nionio6915/Euclid_Probe/Firmware_Examples/Duet_RRF2.x/probe_deploy.png

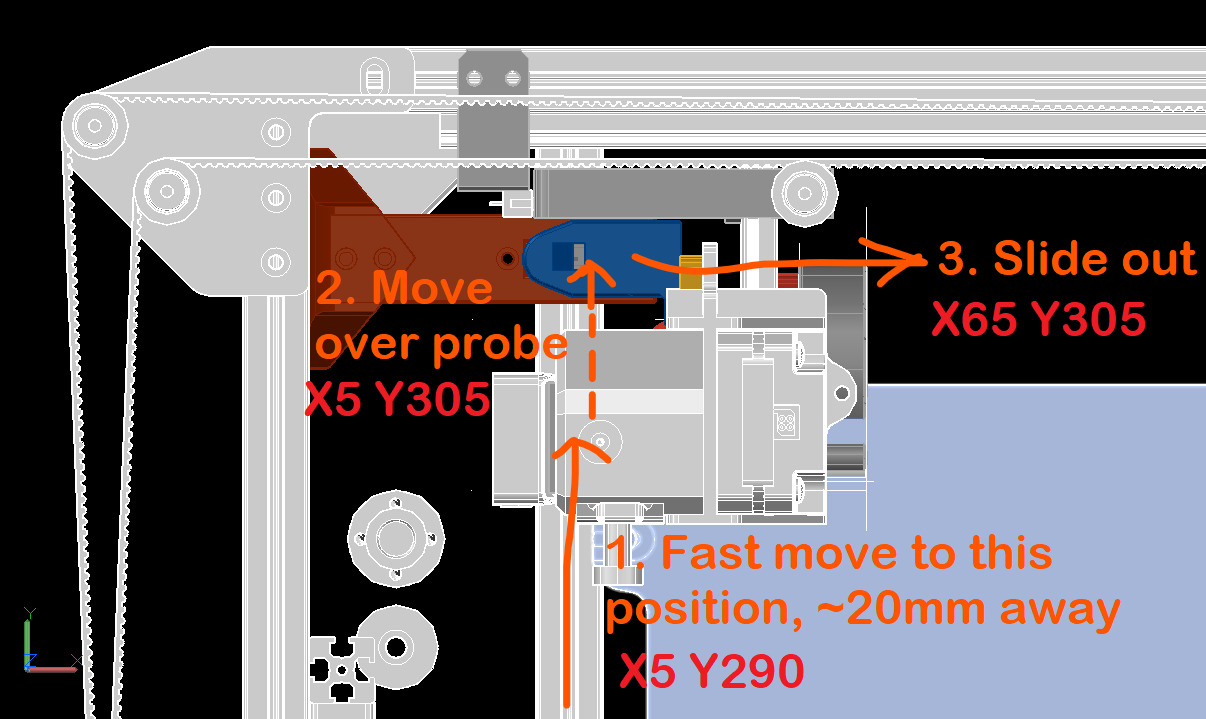
Firmware_Examples/Duet_RRF2.x/probe_deploy.png
