nionio6915/Euclid_Probe/Firmware_Examples/Klipper/user_contrib/FlashForgeCreator_Qidi/QIDI_BED.png

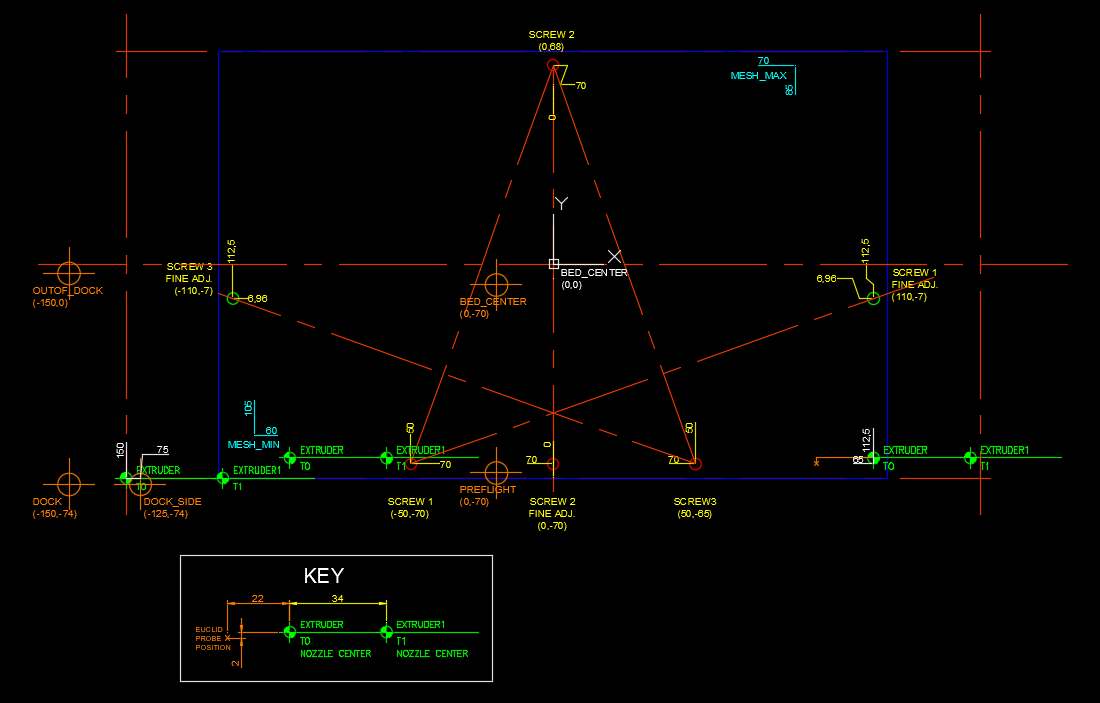
Firmware_Examples/Klipper/user_contrib/FlashForgeCreator_Qidi/QIDI_BED.png
