nionio6915/Euclid_Probe/Firmware_Examples/Klipper/user_contrib/V_Core/vcore3.png

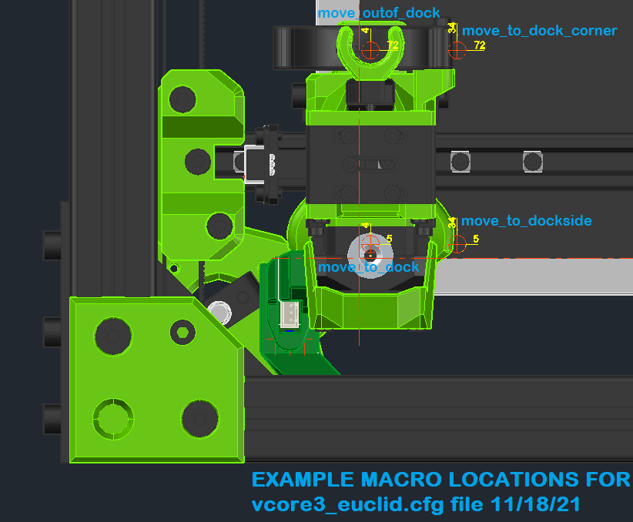
Firmware_Examples/Klipper/user_contrib/V_Core/vcore3.png
