nionio6915/Euclid_Probe/images/EnderMount.png

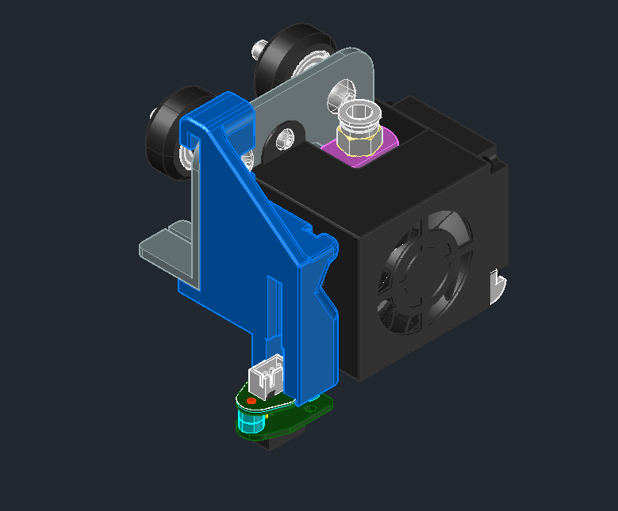
images/EnderMount.png
