nionio6915/Euclid_Probe/images/Front-Probe.png

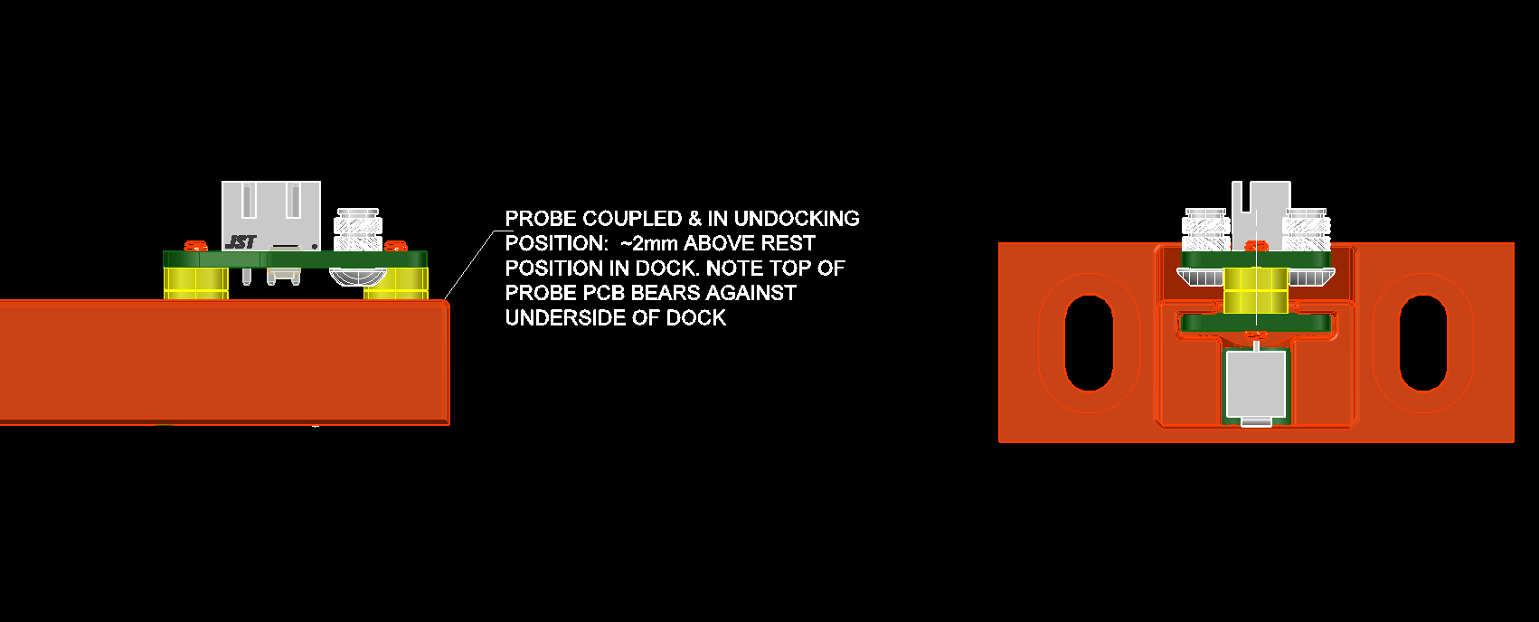
images/Front-Probe.png
