nionio6915/Euclid_Probe/images/Grafting_Mount1.png

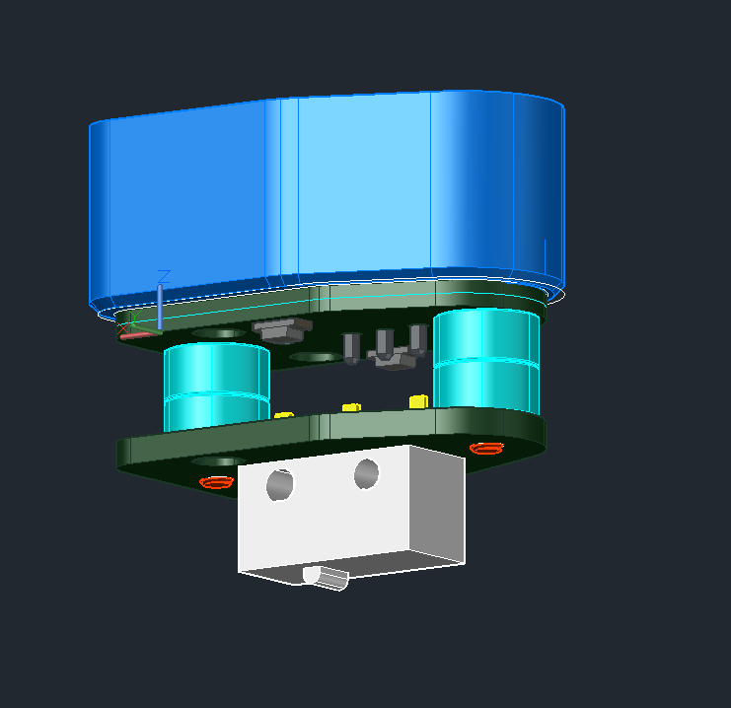
images/Grafting_Mount1.png
