nionio6915/Euclid_Probe/images/Grafting_Mount2.png

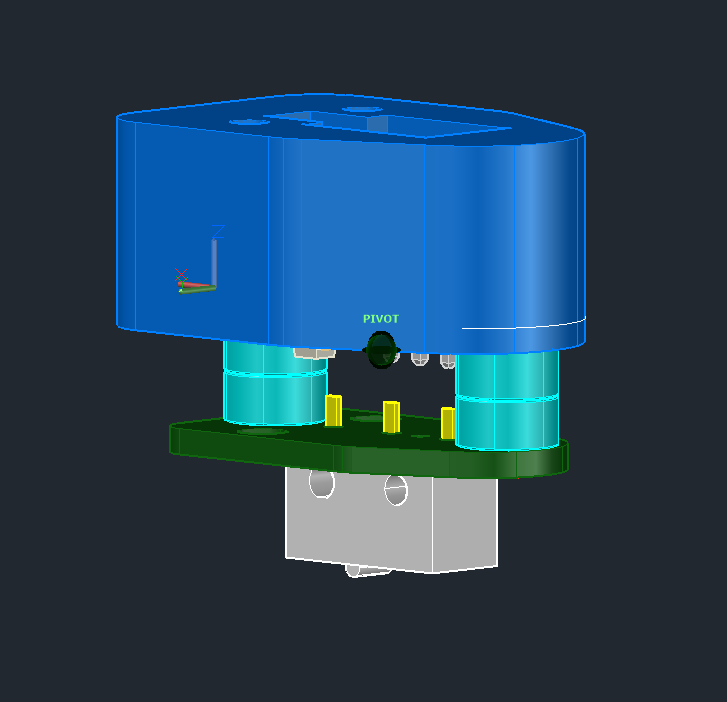
images/Grafting_Mount2.png
