nionio6915/Euclid_Probe/images/IMG_20210708_134827082.jpg

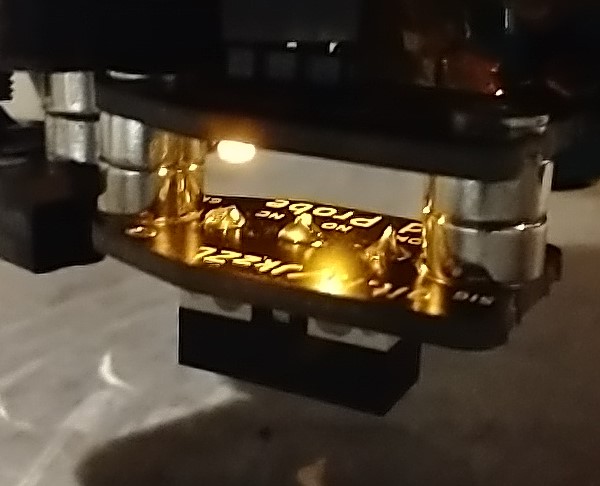
images/IMG_20210708_134827082.jpg
