nionio6915/Euclid_Probe/images/ISO_View1.png

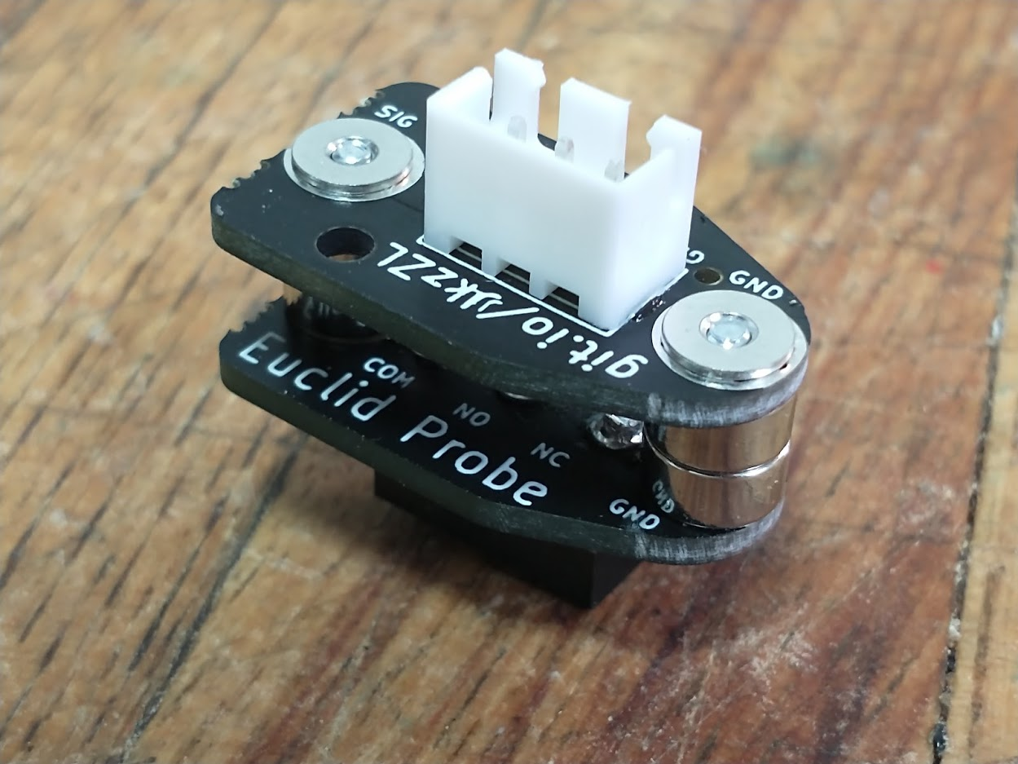
images/ISO_View1.png
