nionio6915/Euclid_Probe/images/ISO_View3.png

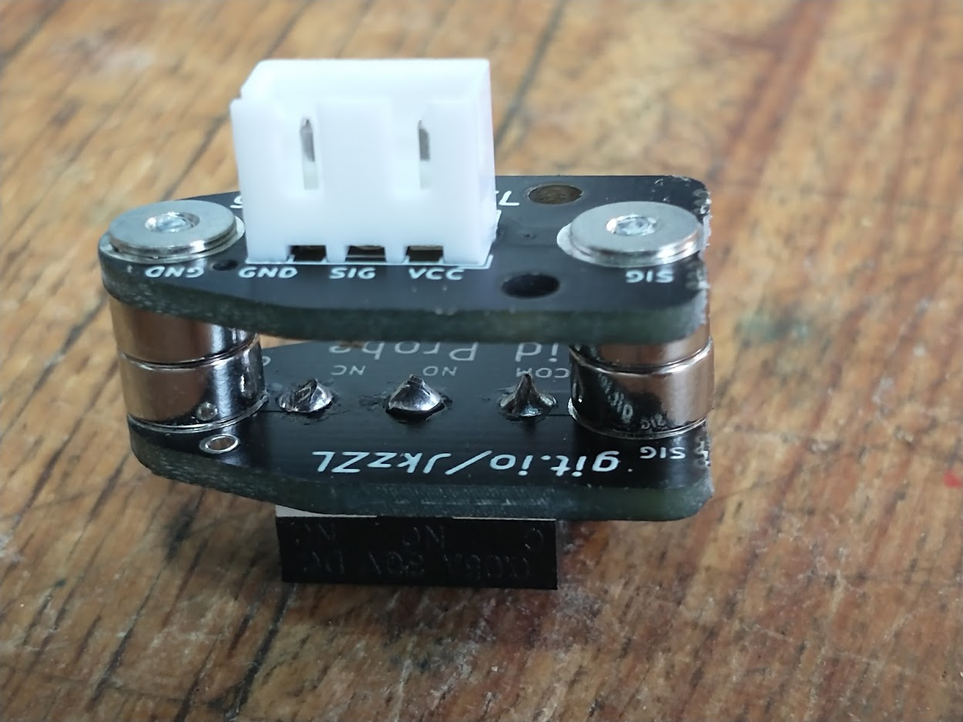
images/ISO_View3.png
