nionio6915/Euclid_Probe/images/ISO_View.png

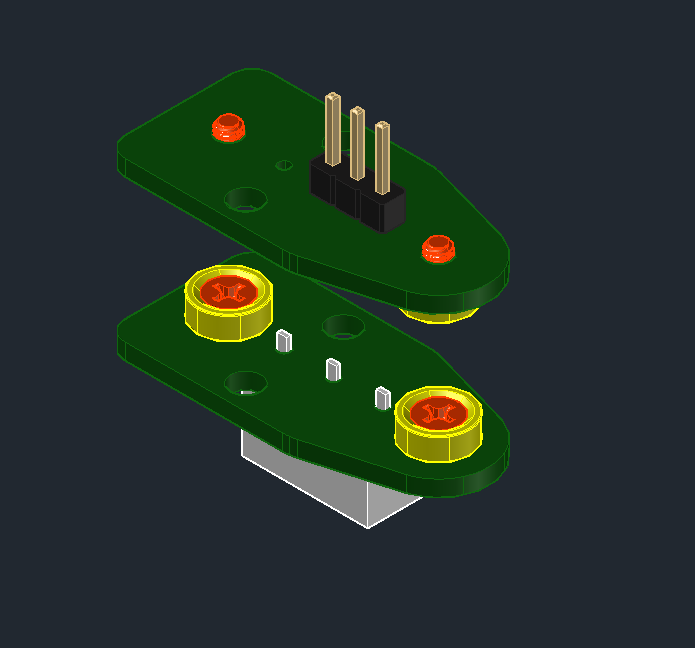
images/ISO_View.png
