nionio6915/Euclid_Probe/images/isobtm2.png

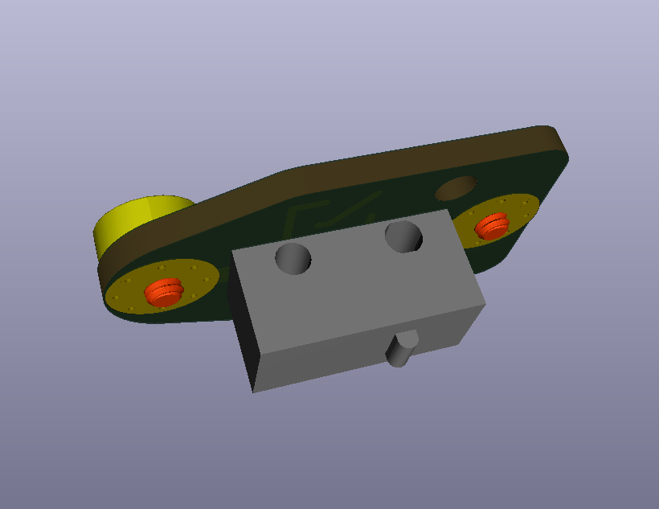
images/isobtm2.png
