nionio6915/Euclid_Probe/images/isobtm.png

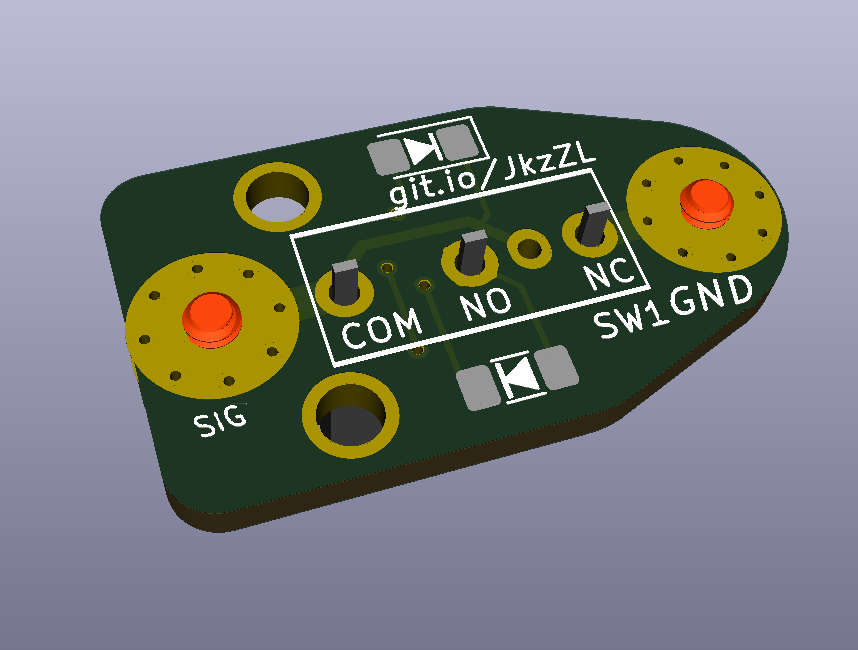
images/isobtm.png
