nionio6915/Euclid_Probe/images/isotop2.png

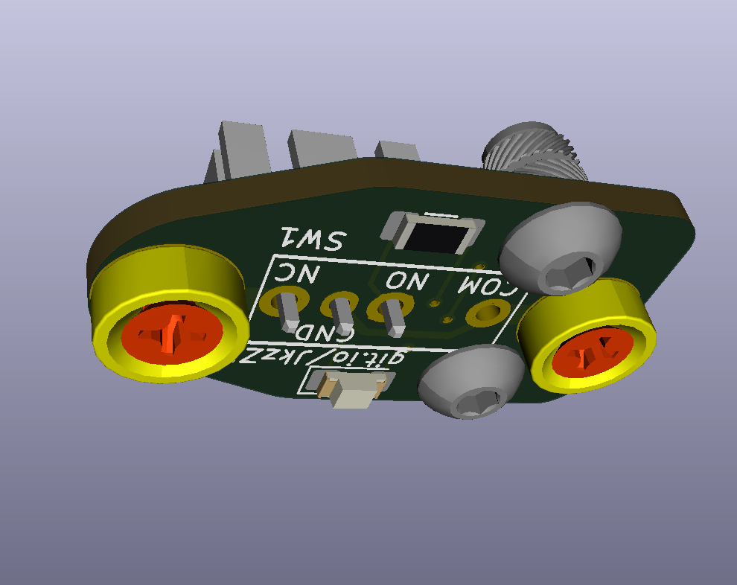
images/isotop2.png
