nionio6915/Euclid_Probe/images/isotop.png

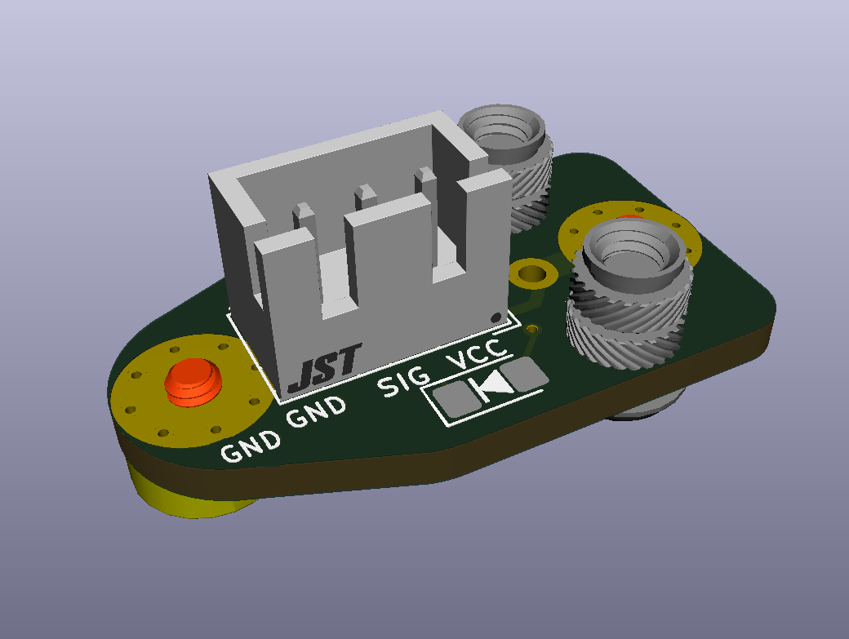
images/isotop.png
