nionio6915/Euclid_Probe/images/Left_View.png

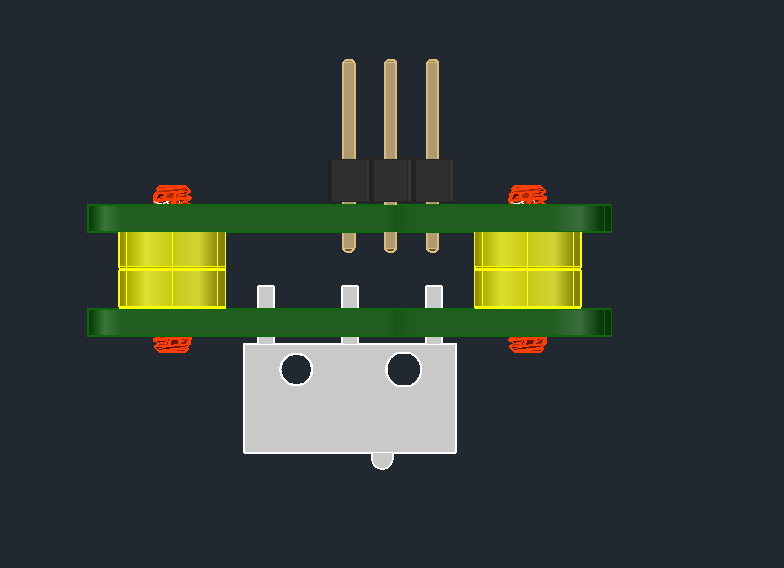
images/Left_View.png
