nionio6915/Euclid_Probe/images/mag-polarity.png

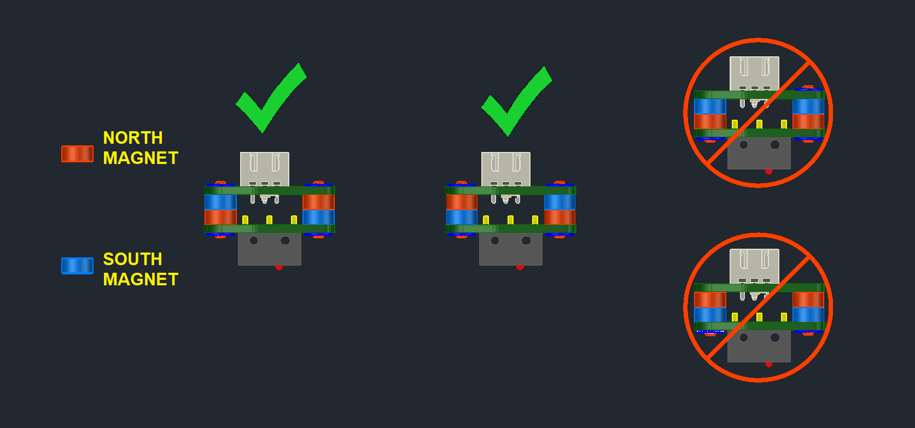
images/mag-polarity.png
