nionio6915/Euclid_Probe/images/PROBE-BOARD.png

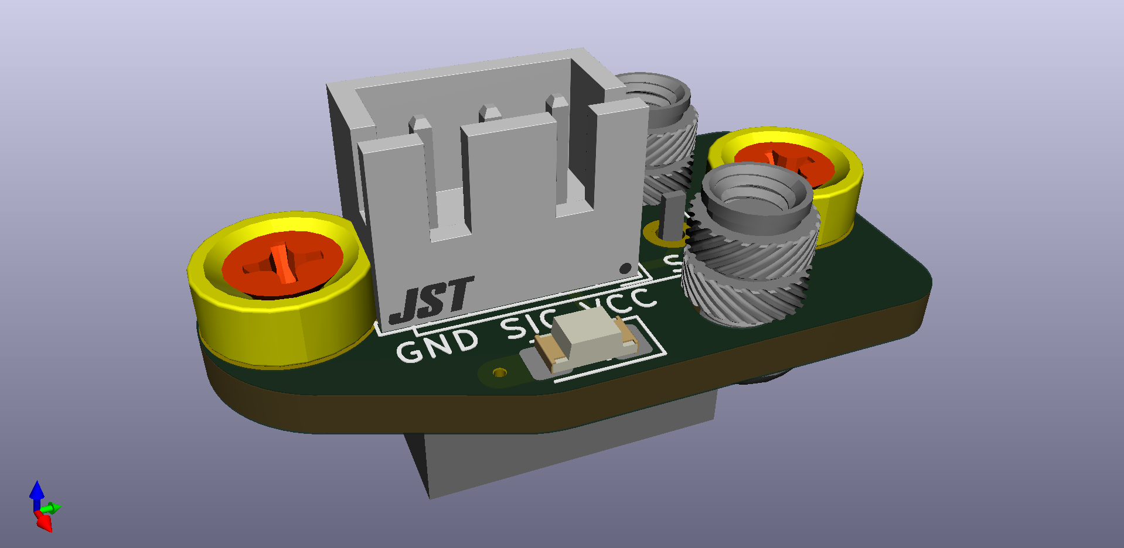
images/PROBE-BOARD.png
