nionio6915/Euclid_Probe/images/probe-offsets.png

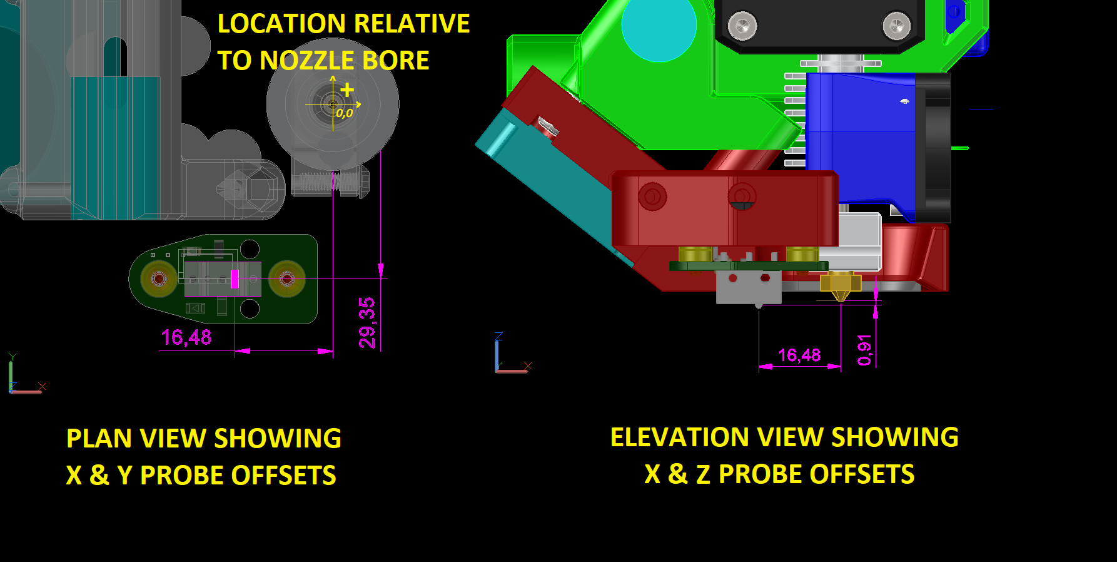
images/probe-offsets.png
