nionio6915/Euclid_Probe/images/Probe_Dock_Fixed.png

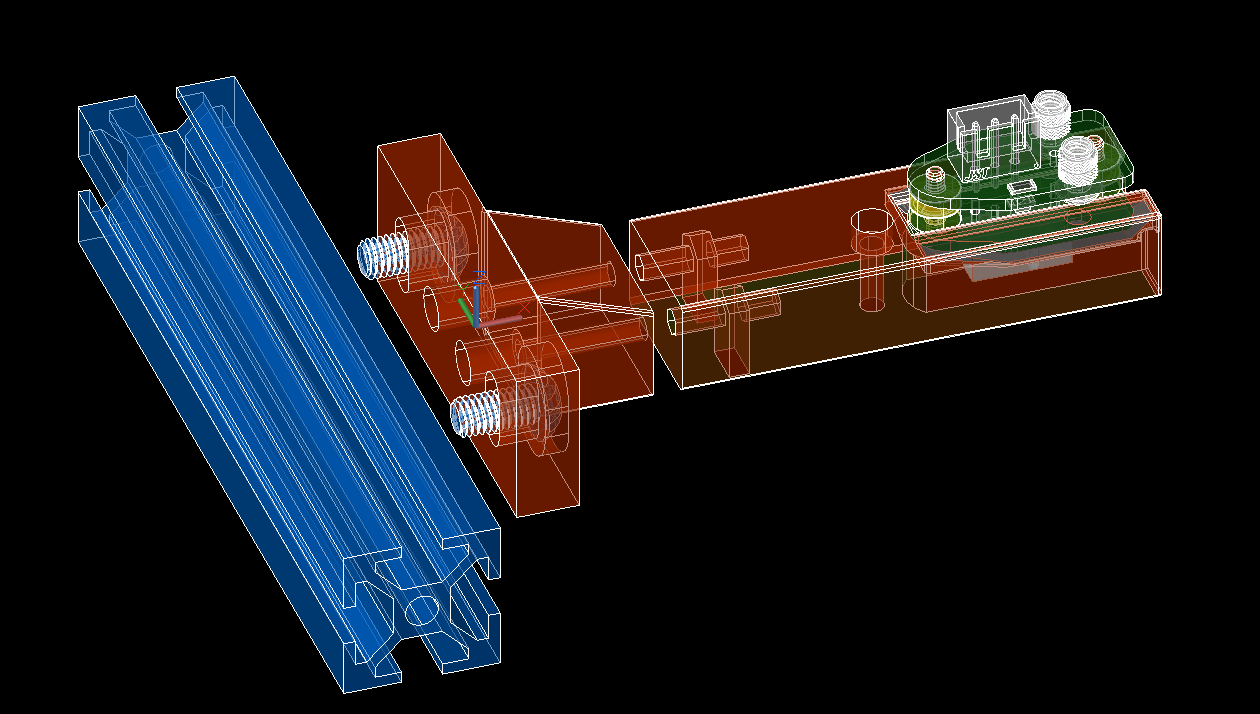
images/Probe_Dock_Fixed.png
