nionio6915/Euclid_Probe/images/RailCore_Native.png

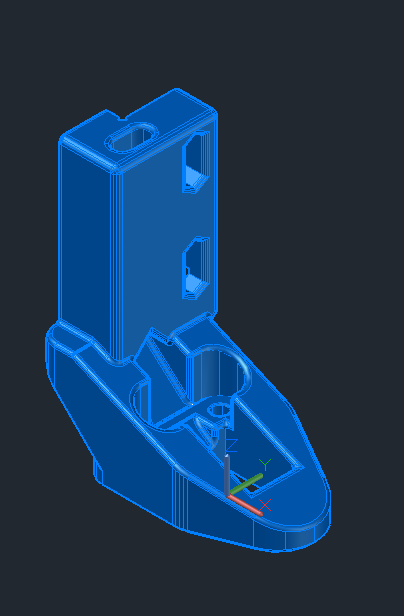
images/RailCore_Native.png
