nionio6915/Euclid_Probe/images/VoronStill3-TN.png

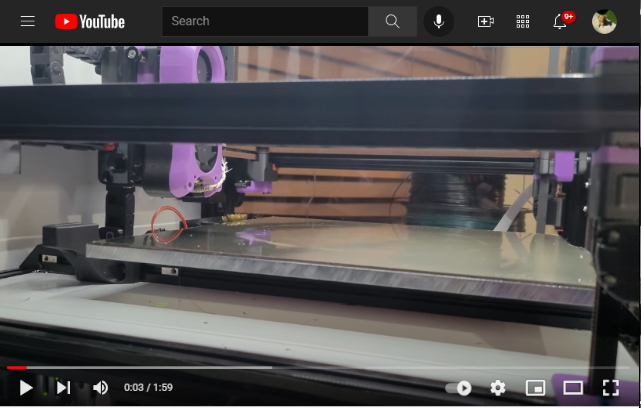
images/VoronStill3-TN.png
