nionio6915/Euclid_Probe/stls/Ender3/EnderDock.jpg

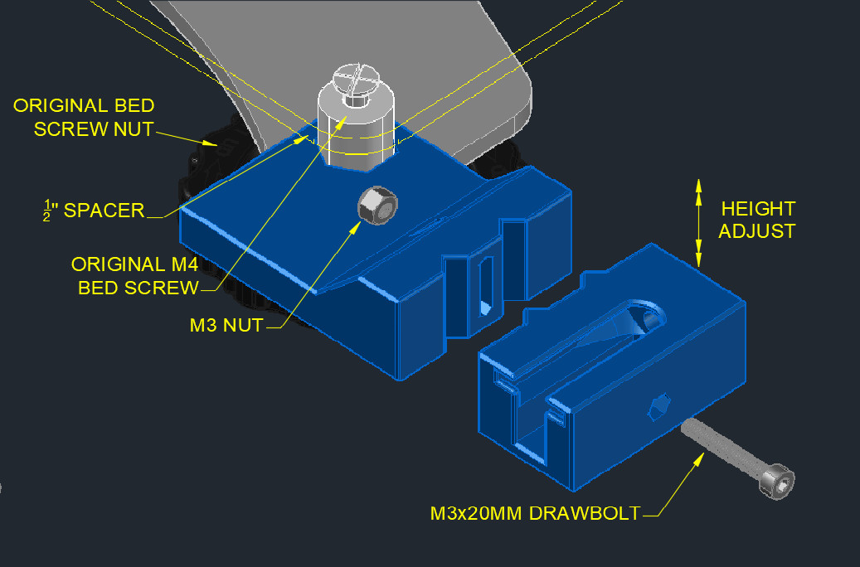
stls/Ender3/EnderDock.jpg
