nionio6915/Euclid_Probe/stls/Ender3/EnderProbeOffsets.jpg

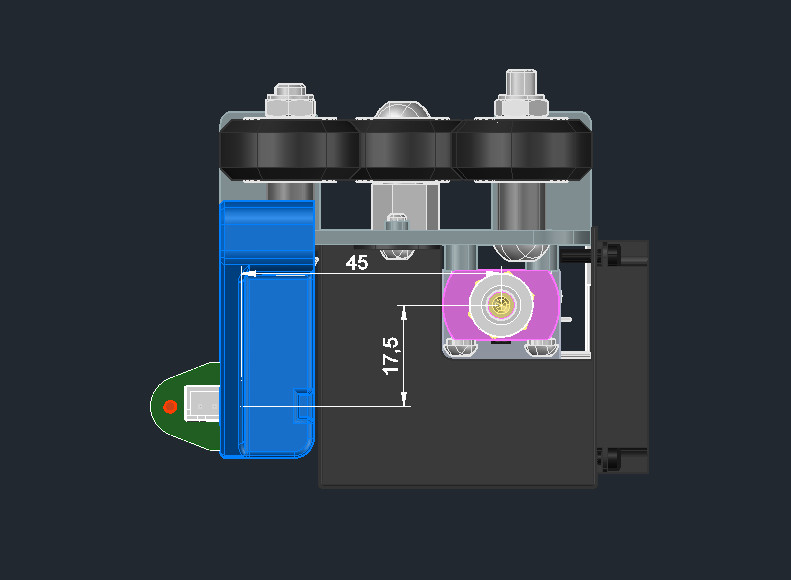
stls/Ender3/EnderProbeOffsets.jpg
