nionio6915/Euclid_Probe/stls/FlashForgeCreator-Qidi/Qidi1.jpg

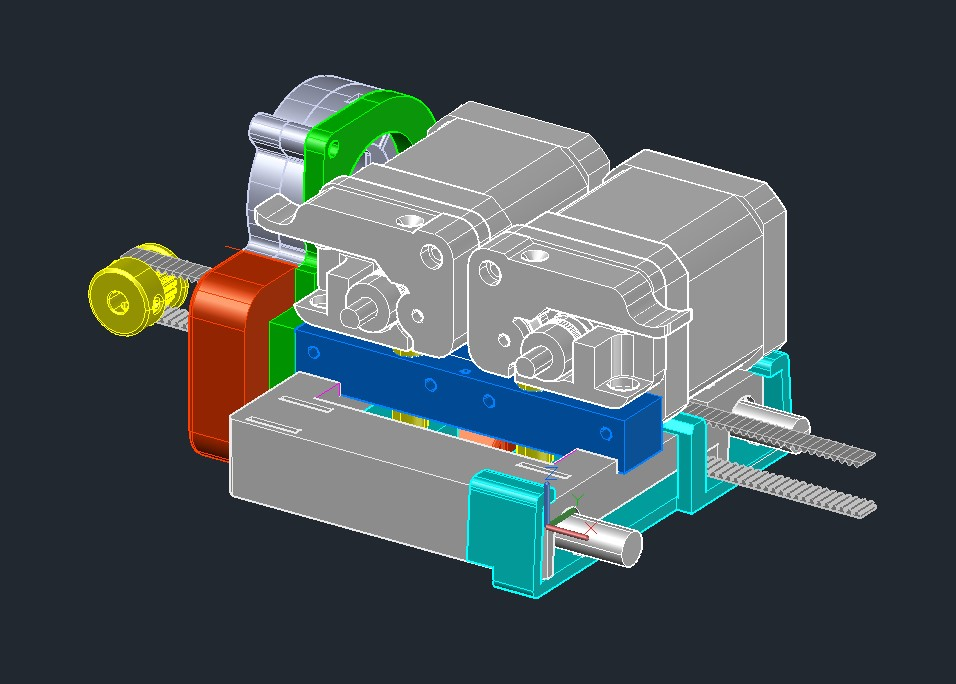
stls/FlashForgeCreator-Qidi/Qidi1.jpg
