nionio6915/Euclid_Probe/stls/FlashForgeCreator-Qidi/Qidi2.jpg

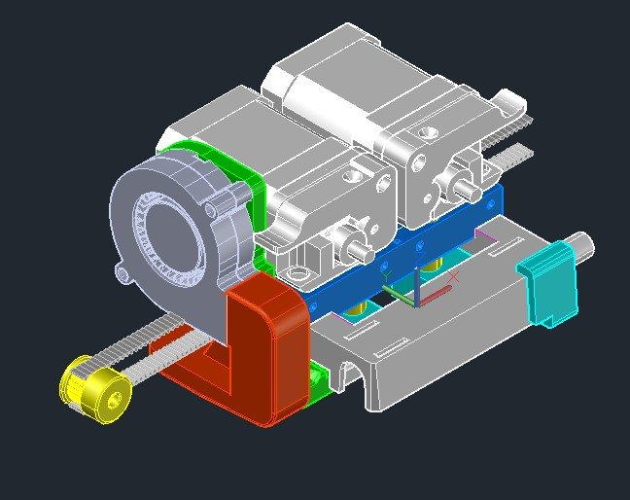
stls/FlashForgeCreator-Qidi/Qidi2.jpg
