nionio6915/Euclid_Probe/stls/FlashForgeCreator-Qidi/Qidi3.jpg

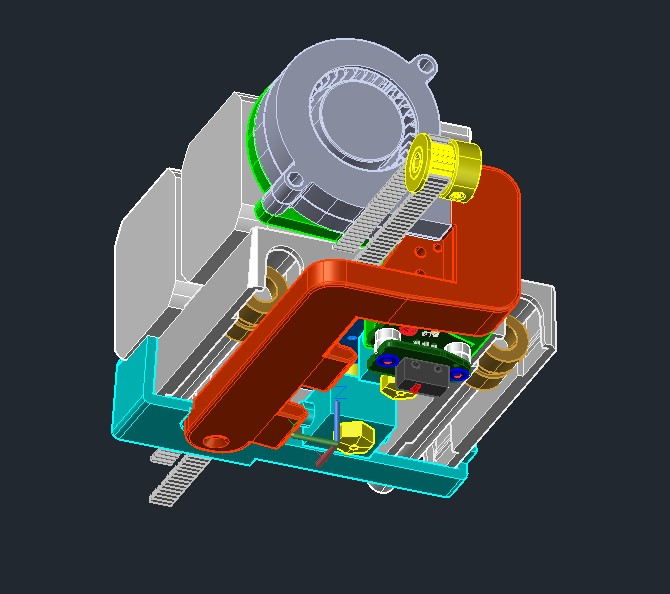
stls/FlashForgeCreator-Qidi/Qidi3.jpg
