nionio6915/Euclid_Probe/stls/Mount Adapters/12mm-186x300.jpg

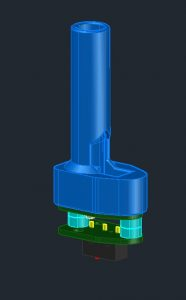
stls/Mount Adapters/12mm-186x300.jpg
