nionio6915/Euclid_Probe/stls/Mount Adapters/BLTouch/BLT.jpg

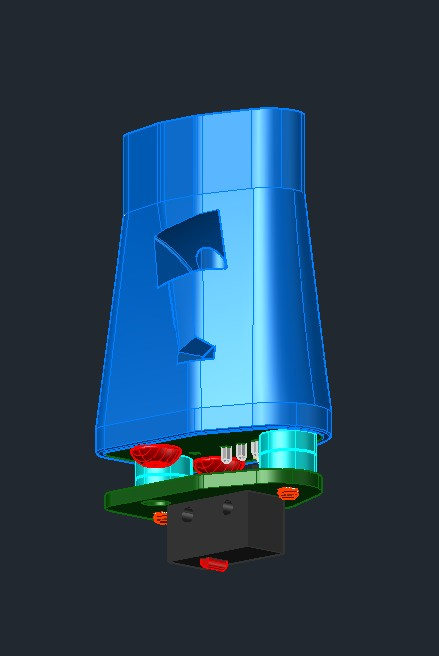
stls/Mount Adapters/BLTouch/BLT.jpg
