nionio6915/Euclid_Probe/stls/Mount Adapters/BLTouch/Screenshot 2022-03-06 101952.jpg

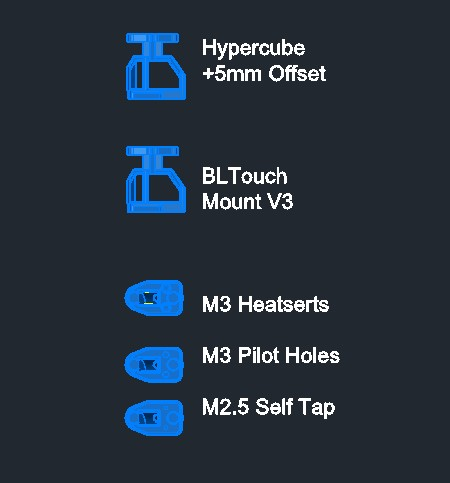
stls/Mount Adapters/BLTouch/Screenshot 2022-03-06 101952.jpg
