nionio6915/Euclid_Probe/stls/Rail Core/DrillJig1.png

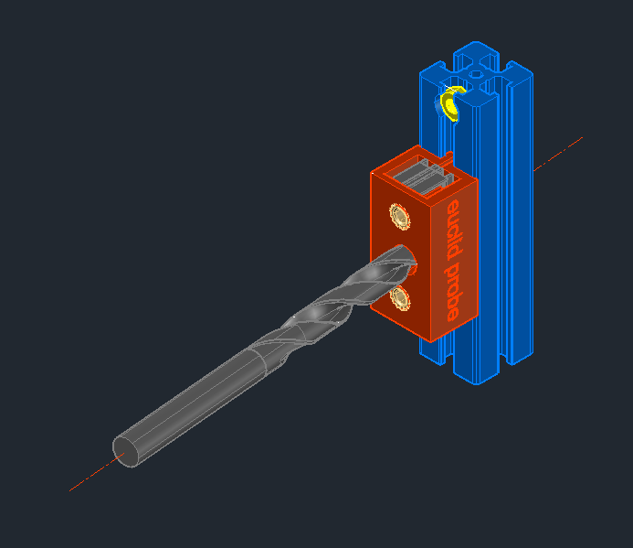
stls/Rail Core/DrillJig1.png
