nionio6915/Euclid_Probe/stls/Rail Core/DrillJig2.png

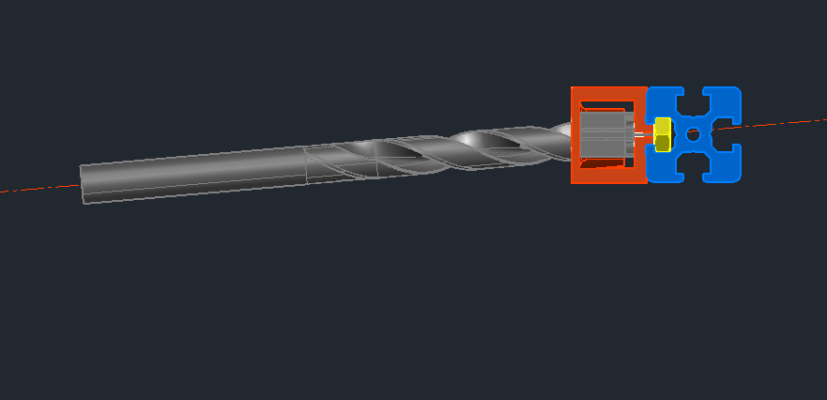
stls/Rail Core/DrillJig2.png
