nionio6915/Euclid_Probe/stls/V-Core/EVA_Mount/EVA2.x_MountV5.jpg

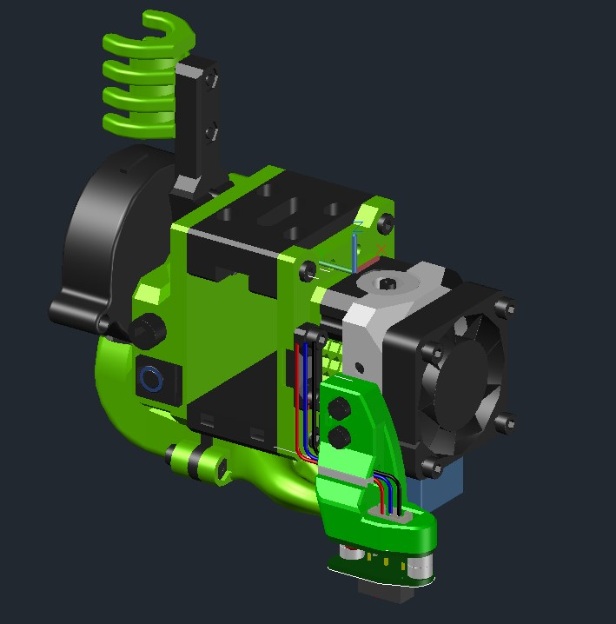
stls/V-Core/EVA_Mount/EVA2.x_MountV5.jpg
