nionio6915/Euclid_Probe/stls/V-Core/EVA_Mount/EVA3.x_Mount.webp

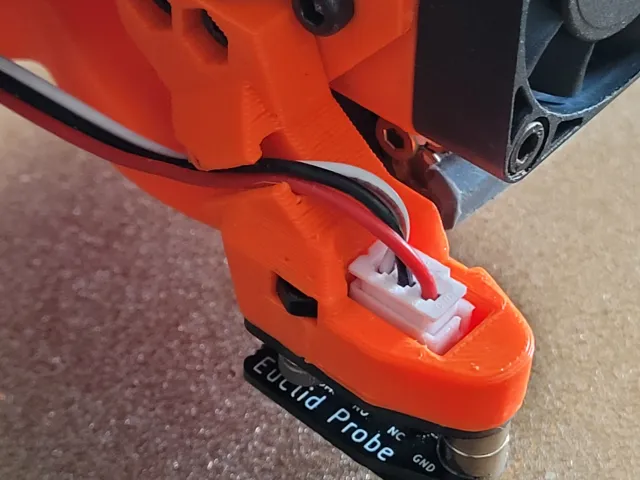
stls/V-Core/EVA_Mount/EVA3.x_Mount.webp
