nionio6915/Euclid_Probe/stls/V-Core/EVA_Mount/Screenshot 2021-12-29 203222.png

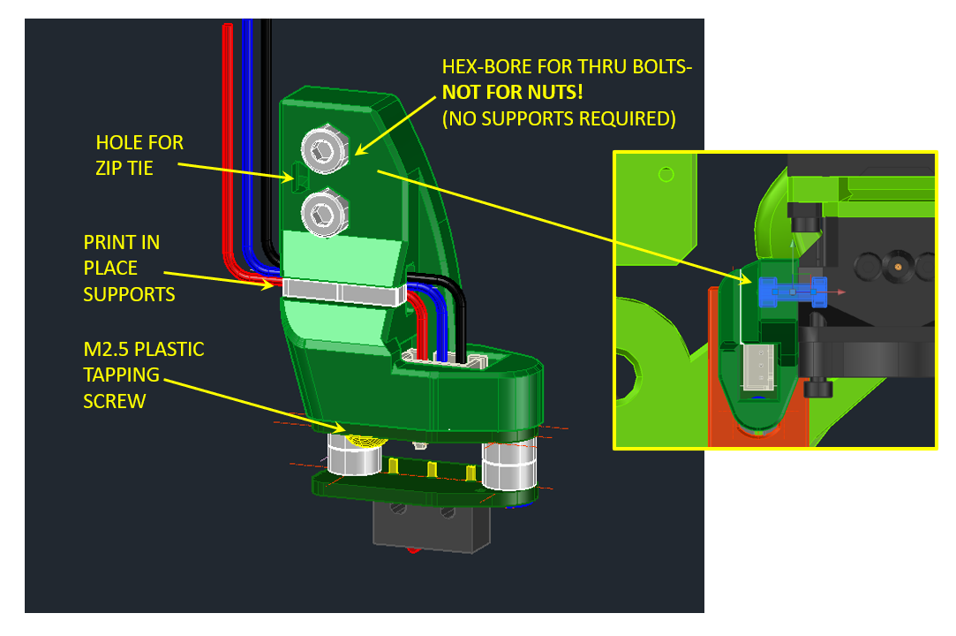
stls/V-Core/EVA_Mount/Screenshot 2021-12-29 203222.png
