nionio6915/Euclid_Probe/stls/V-Core/V-Core3/Euclid_Probe_Screen2.jpg

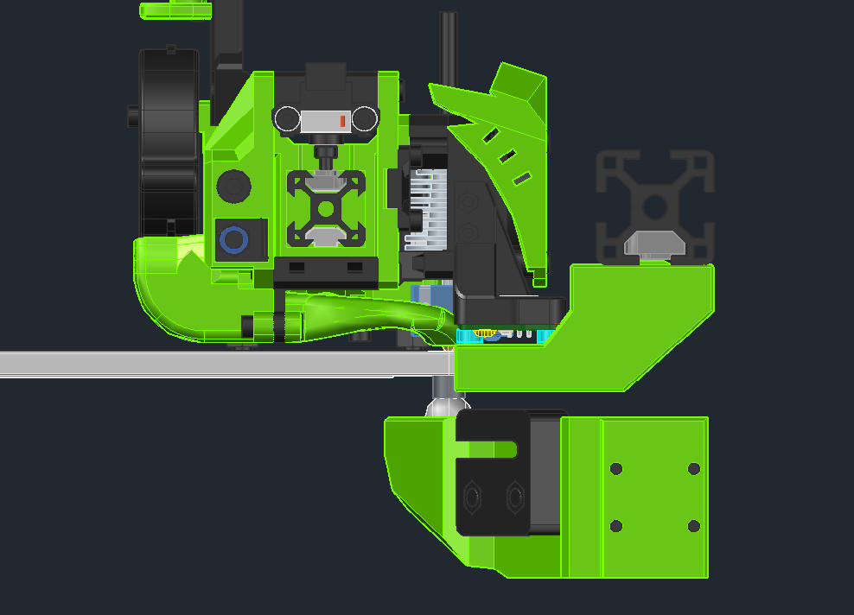
stls/V-Core/V-Core3/Euclid_Probe_Screen2.jpg
