nionio6915/Euclid_Probe/stls/V-Core/V-Core3/unknown-768x550.jpg

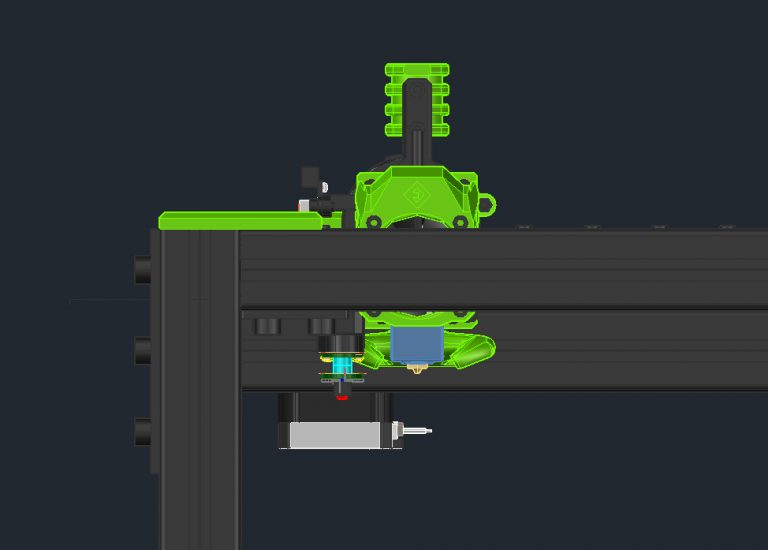
stls/V-Core/V-Core3/unknown-768x550.jpg
