nionio6915/Euclid_Probe/stls/Voron/User_Contrib/Dust_Gantry_Dock2.jpg

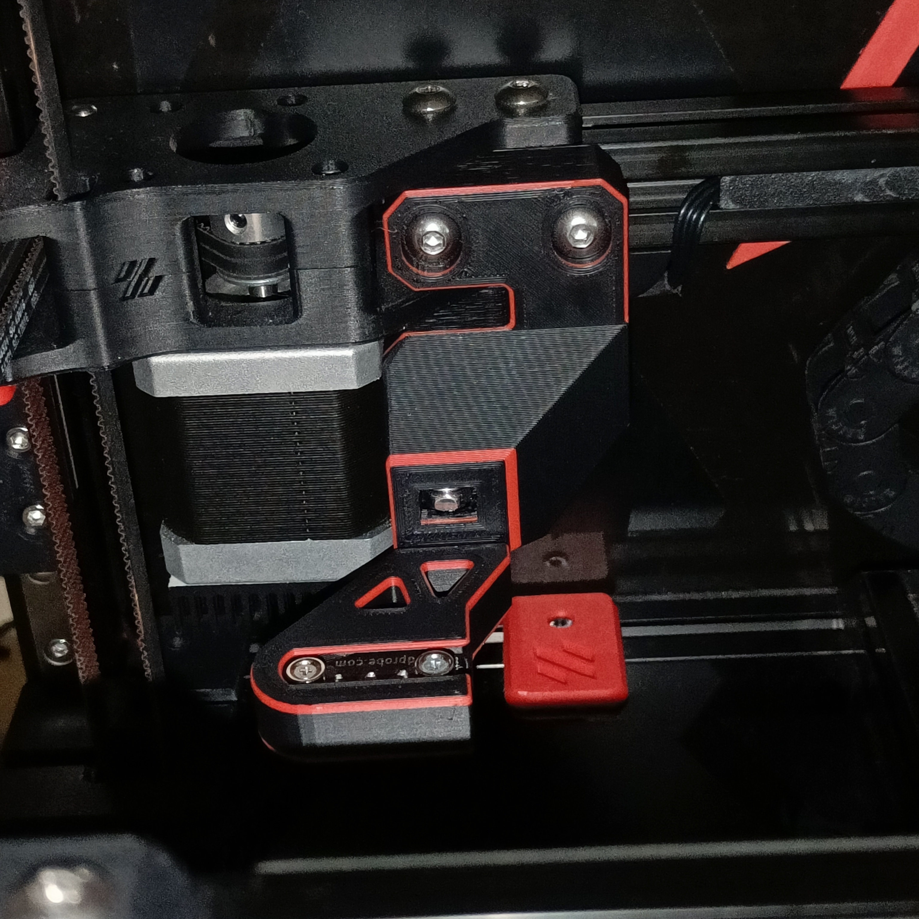
stls/Voron/User_Contrib/Dust_Gantry_Dock2.jpg
