nionio6915/Euclid_Probe/stls/Fan Mounts/5015_LeftP1.5V4.stl

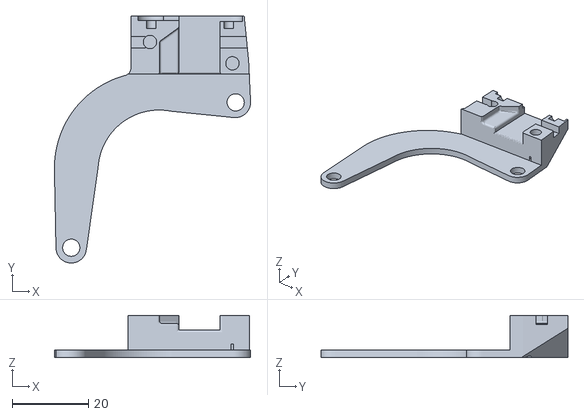
[picture p93: CAD file, 2021-12-24]
stls/Fan Mounts/5015_LeftP1.5V4.stl
51.3 x 64.6 x 11.0
