nionio6915/Euclid_Probe/stls/FlashForgeCreator-Qidi/FanMount.stl

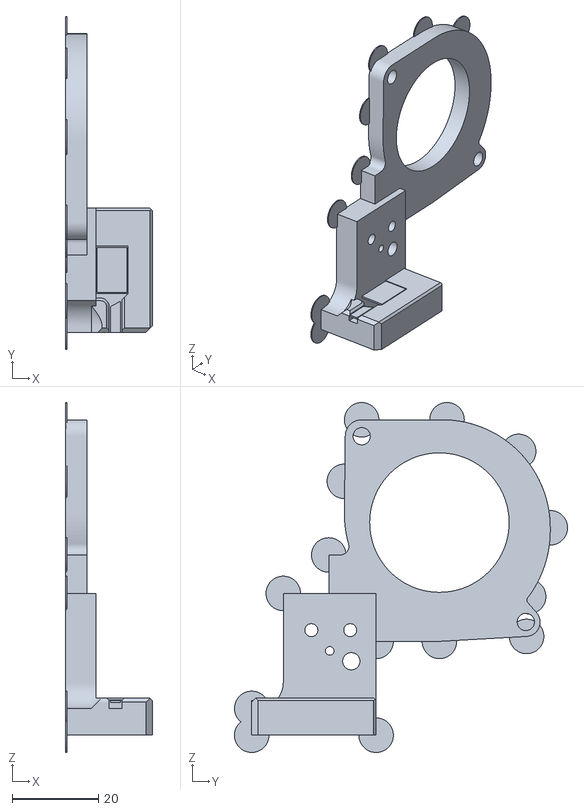
[picture p94: CAD file, 2023-03-29]
stls/FlashForgeCreator-Qidi/FanMount.stl
20.1 x 77.1 x 81.0
