nionio6915/Euclid_Probe/stls/Mount Adapters/18mmInductive.stl

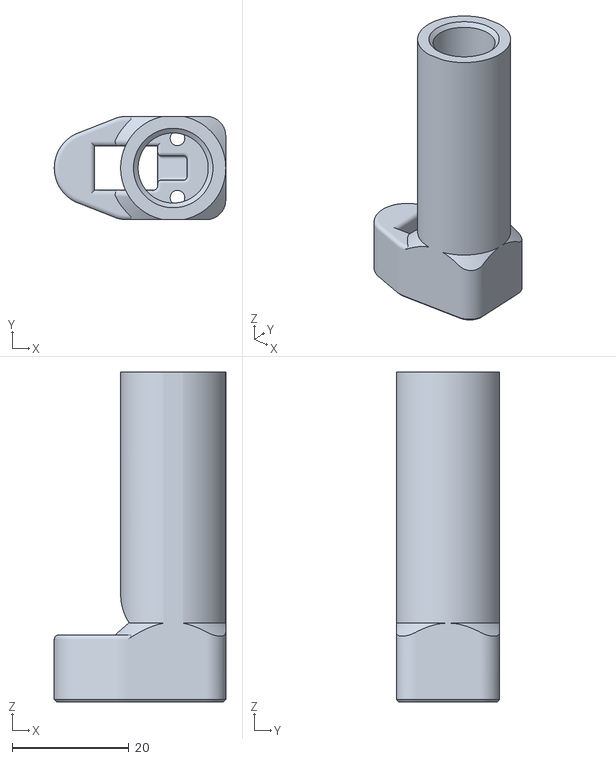
[picture p95: CAD file, 2021-08-17]
stls/Mount Adapters/18mmInductive.stl
29.4 x 17.7 x 56.5
