nionio6915/Euclid_Probe/stls/Mount Adapters/2020_End_Mount/2020_Rail_Vert.stl

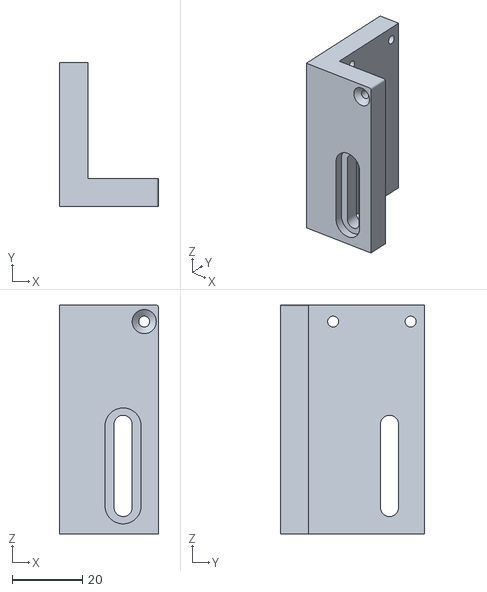
[picture p96: CAD file, 2021-06-21]
stls/Mount Adapters/2020_End_Mount/2020_Rail_Vert.stl
28.0 x 41.0 x 65.0
