nionio6915/Euclid_Probe/stls/Mount Adapters/Omron/OmronFotekV4.3mf

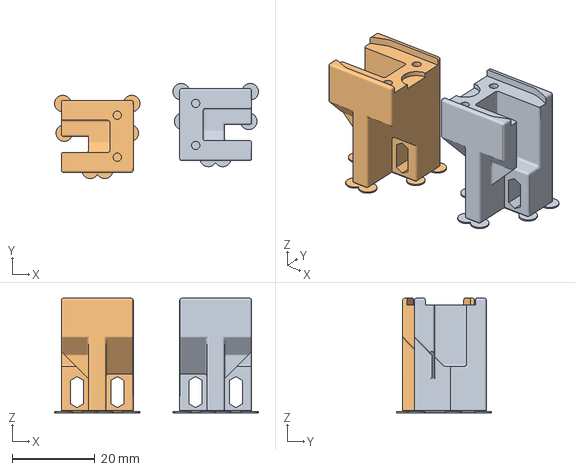
[picture p97: CAD file, 2023-02-20]
stls/Mount Adapters/Omron/OmronFotekV4.3mf
49.3 x 23.0 x 27.7 mm
OmronFotekV4.stl x 2
