nionio6915/Euclid_Probe/stls/probe-dock_fixed.stl

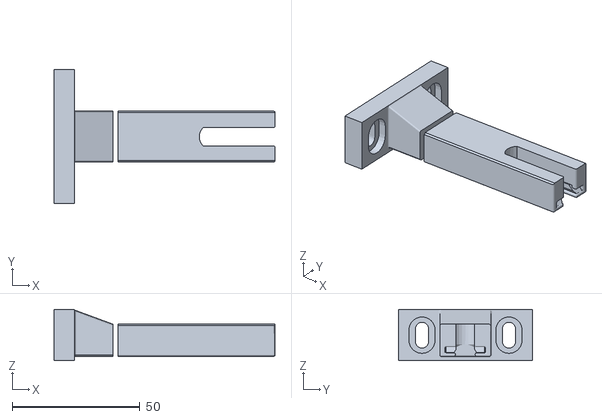
[picture p98: CAD file, 2021-06-24]
stls/probe-dock_fixed.stl
86.4 x 52.2 x 20.1
