nionio6915/Euclid_Probe/stls/Rail Core/RailcoreMount713NativeV5_M3Holes.3mf

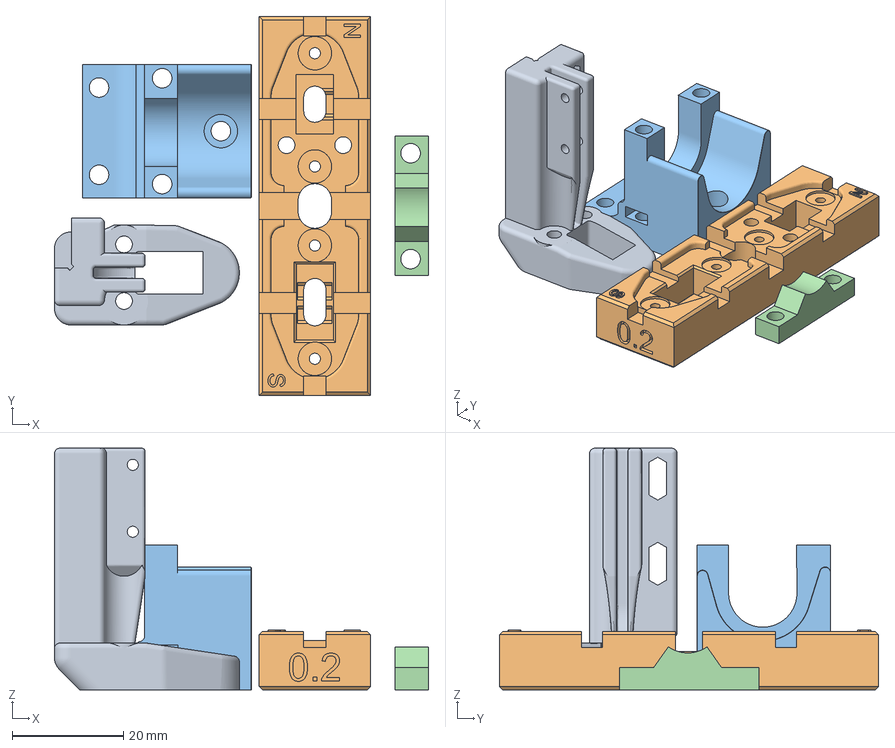
[picture p99: CAD file, 2023-11-06]
stls/Rail Core/RailcoreMount713NativeV5_M3Holes.3mf
67.1 x 68.0 x 43.4 mm
RailcoreMount713NativeV5_M3Holes.stl
soldering_jigV5-0.2mm_margin.stl
E3DV6_Mount.stl
E3DV6_clamp.stl
