nionio6915/Euclid_Probe/stls/UserContrib/akhamar_No Short Cover/euclid_noshort_cover.stl

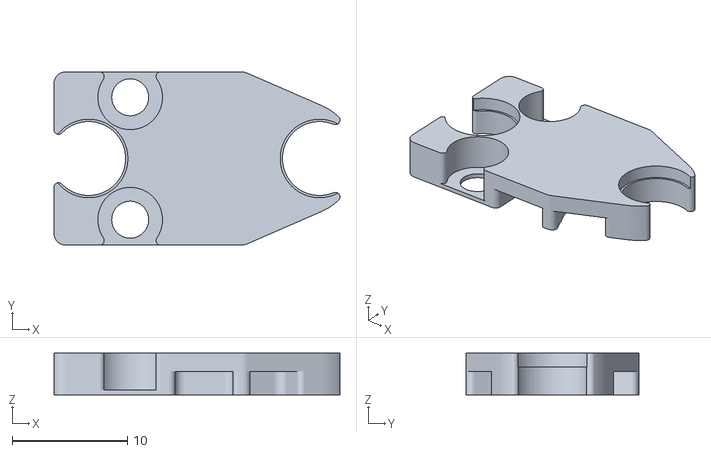
[picture p100: CAD file, 2022-07-11]
stls/UserContrib/akhamar_No Short Cover/euclid_noshort_cover.stl
24.8 x 15.0 x 3.60
