nionio6915/Euclid_Probe/stls/UserContrib/esc247_vzbot_vzprinthead/Euclid mount VZ-printhead v5.stl

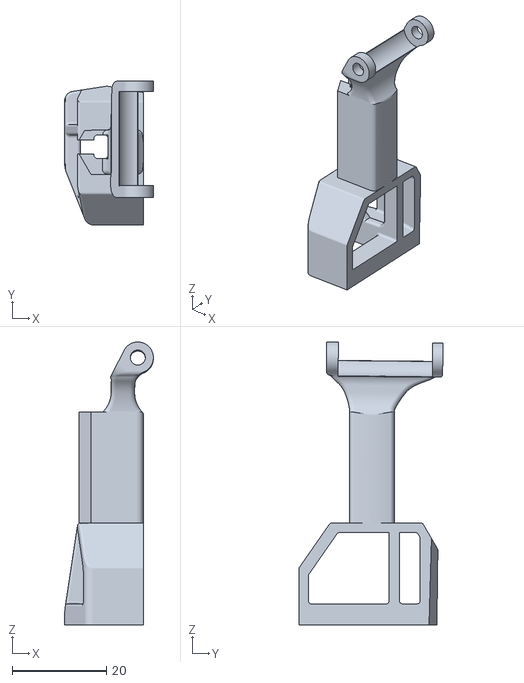
[picture p101: CAD file, 2023-08-14]
stls/UserContrib/esc247_vzbot_vzprinthead/Euclid mount VZ-printhead v5.stl
18.8 x 30.6 x 60.1
