nionio6915/Euclid_Probe/stls/UserContrib/v6cl_skinny_mount/euclid_slim.stl

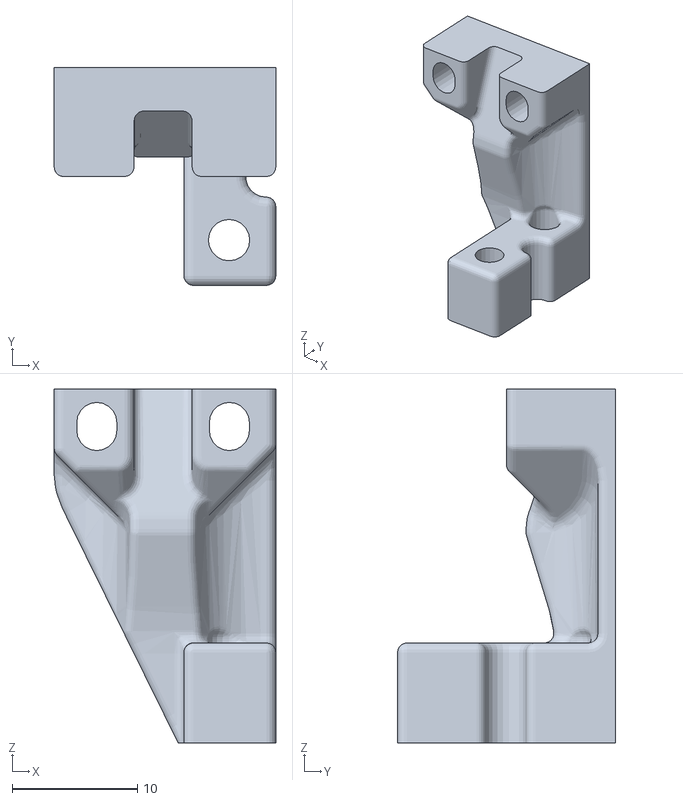
[picture p102: CAD file, 2022-07-11]
stls/UserContrib/v6cl_skinny_mount/euclid_slim.stl
17.7 x 17.4 x 28.3
