nionio6915/Euclid_Probe/stls/V-Core/EVA_Mount/EuclidDock_EVA3_0_v01.stl

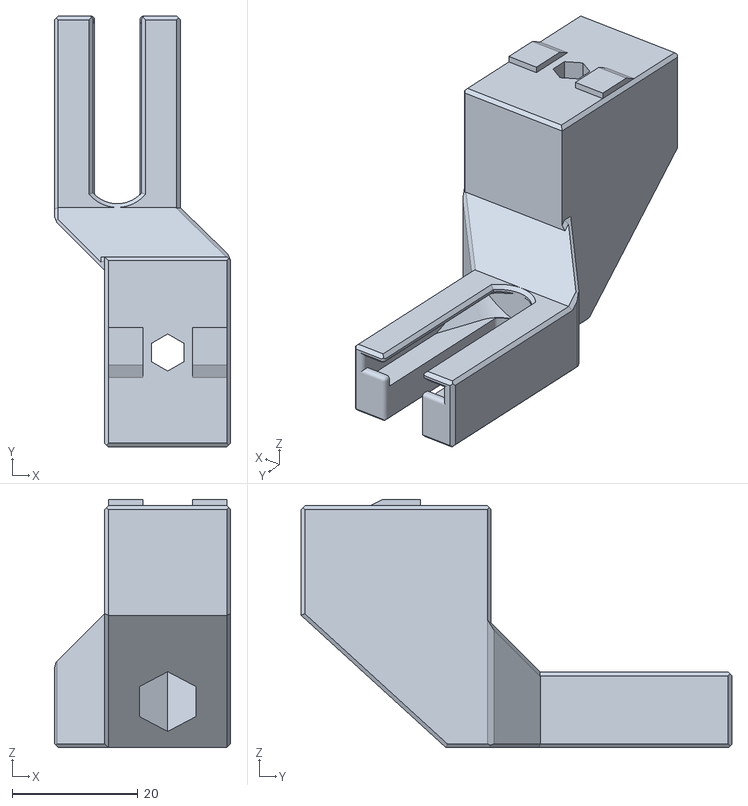
[picture p103: CAD file, 2022-06-29]
stls/V-Core/EVA_Mount/EuclidDock_EVA3_0_v01.stl
28.0 x 68.4 x 39.4
