nionio6915/Euclid_Probe/stls/V-Core/V-Core3/Euclid_EVA_DockV5_3030.stl

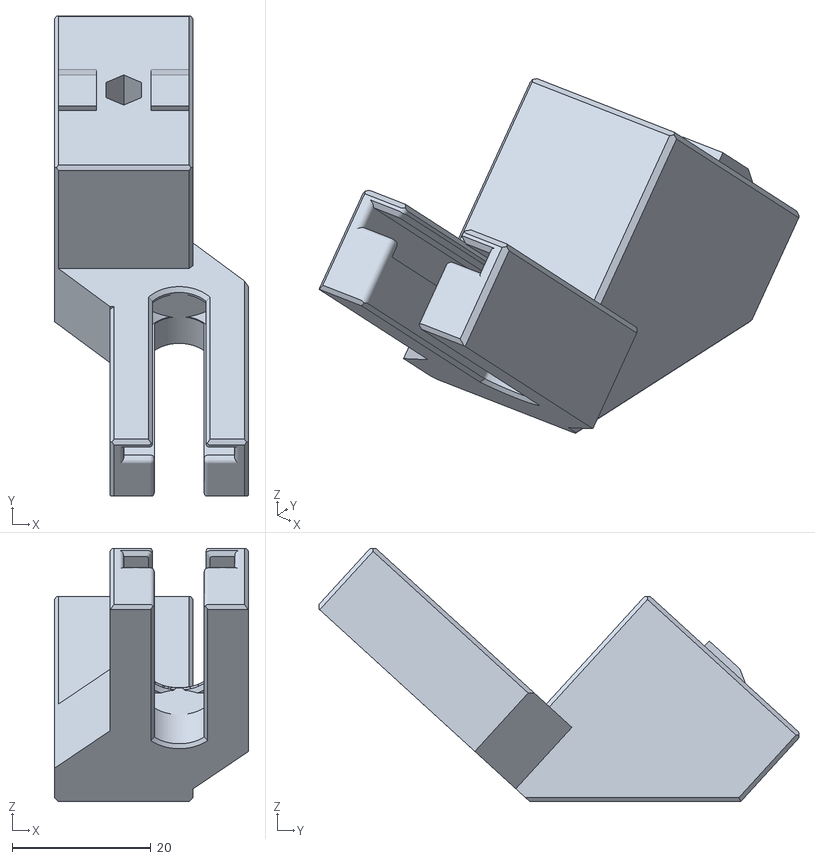
[picture p104: CAD file, 2021-12-25]
stls/V-Core/V-Core3/Euclid_EVA_DockV5_3030.stl
28.0 x 69.2 x 36.5
