nionio6915/Euclid_Probe/stls/Voron/Clockwork2_Euclid_MGN12X_RIGHT_Carriage_Ver2.stl

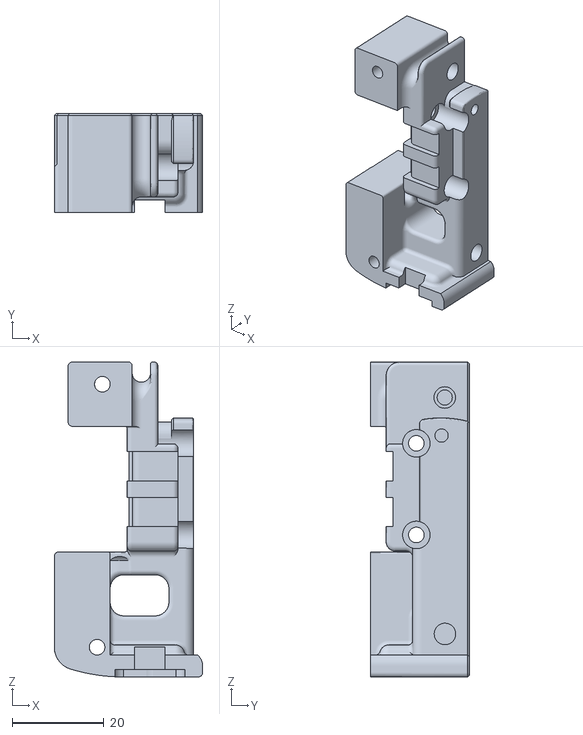
[picture p105: CAD file, 2022-10-25]
stls/Voron/Clockwork2_Euclid_MGN12X_RIGHT_Carriage_Ver2.stl
32.4 x 21.6 x 68.8
