nionio6915/Euclid_Probe/stls/Voron/User_Contrib/Dust_Euclid_Gantry_Face_Mount.stl

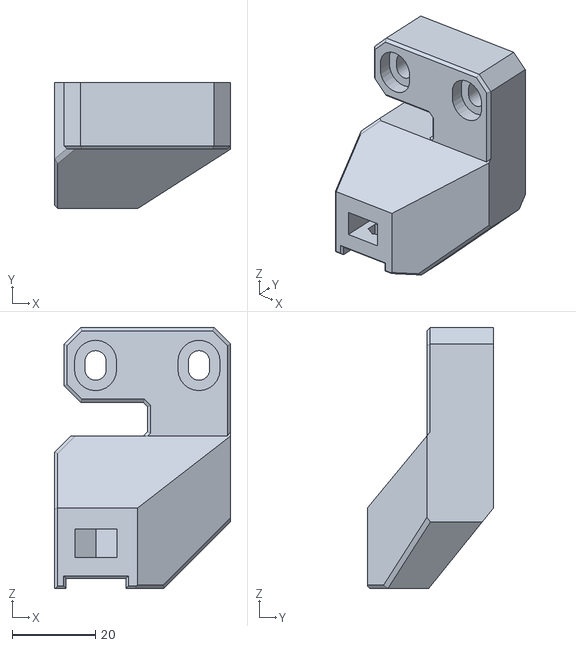
[picture p106: CAD file, 2022-11-09]
stls/Voron/User_Contrib/Dust_Euclid_Gantry_Face_Mount.stl
42.3 x 30.3 x 62.6
