nionio6915/Euclid_Probe/CAD/Building_Blocks/CleanDock.stp

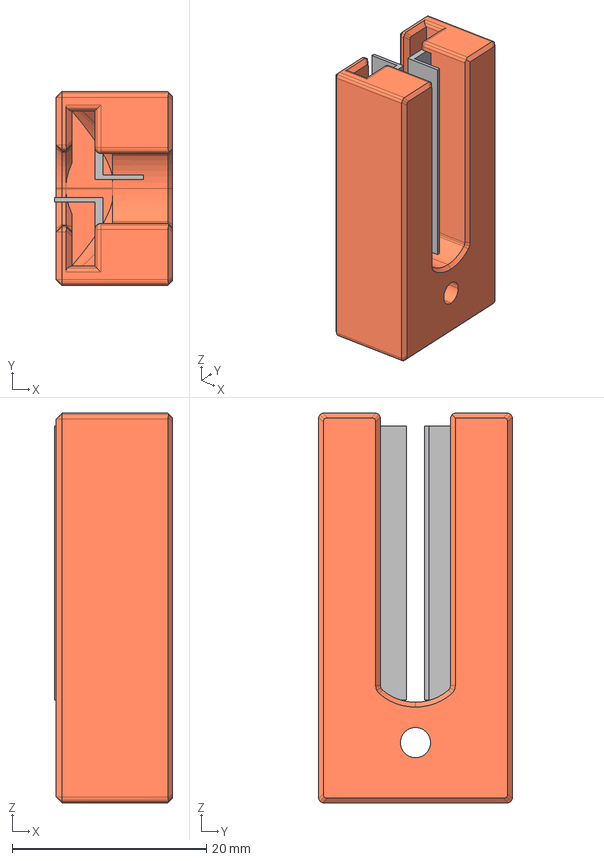
[picture p107: CAD file, 2022-05-13]
CAD/Building_Blocks/CleanDock.stp
12.2 x 20.0 x 40.2 mm
