nionio6915/Euclid_Probe/CAD/MountAdapters/BLTouch-M3HeatSerts.stp

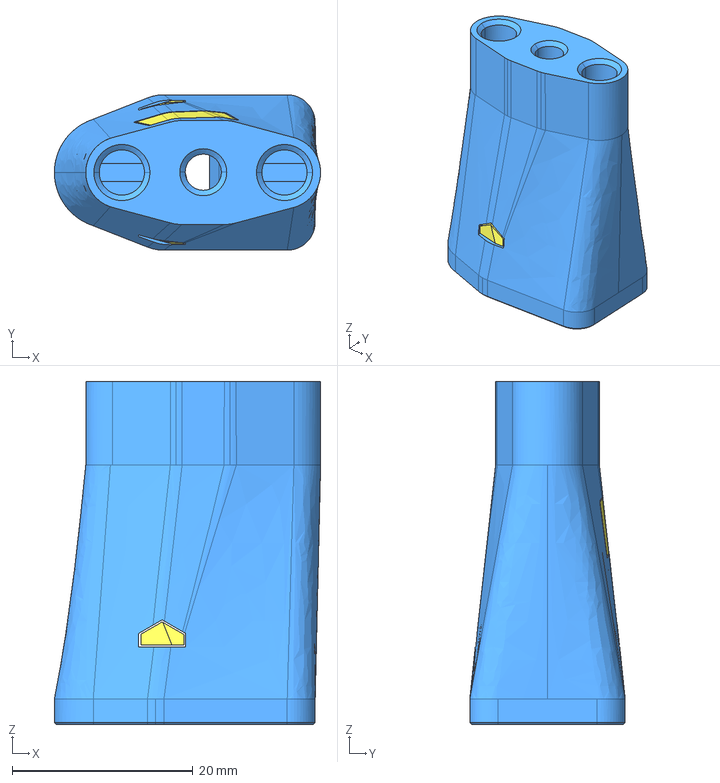
[picture p108: CAD file, 2022-03-06]
CAD/MountAdapters/BLTouch-M3HeatSerts.stp
29.5 x 17.2 x 38.0 mm
