nionio6915/Euclid_Probe/CAD/Rat-Rig V-Core/EuclidDockVCore3_3030_V5.stp

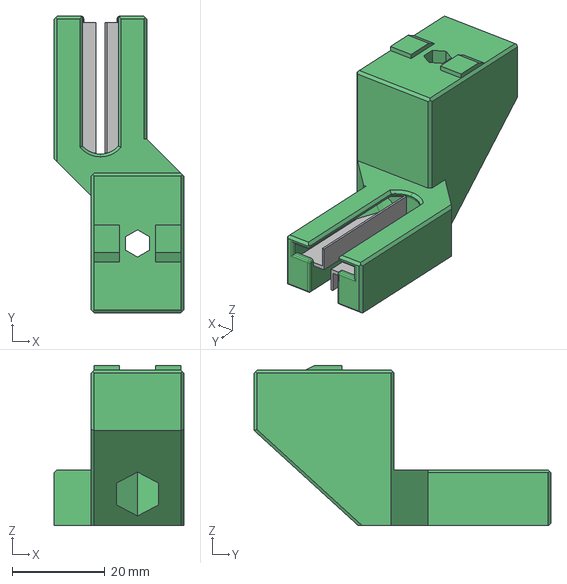
[picture p109: CAD file, 2021-12-30]
CAD/Rat-Rig V-Core/EuclidDockVCore3_3030_V5.stp
28.0 x 64.1 x 34.6 mm
