nionio6915/Euclid_Probe/CAD/Voron/Voron_Adjustable_Bed_DockV2_Beta.stp

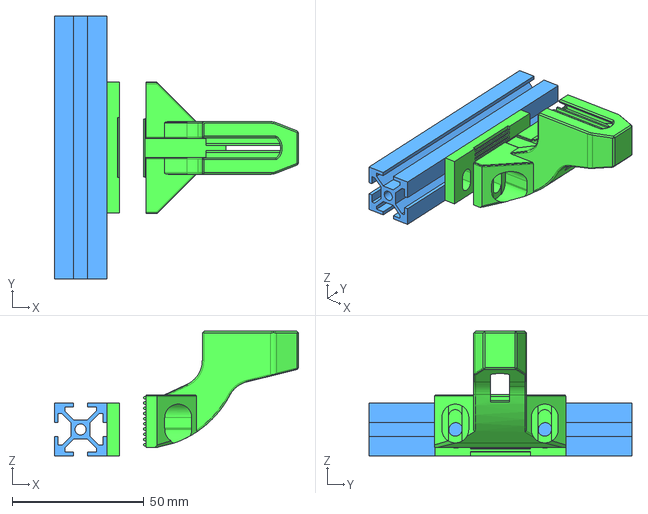
[picture p110: CAD file, 2022-06-29]
CAD/Voron/Voron_Adjustable_Bed_DockV2_Beta.stp
92.9 x 100.0 x 47.3 mm
