nionio6915/Euclid_Probe/scad/board-with_threads.stl

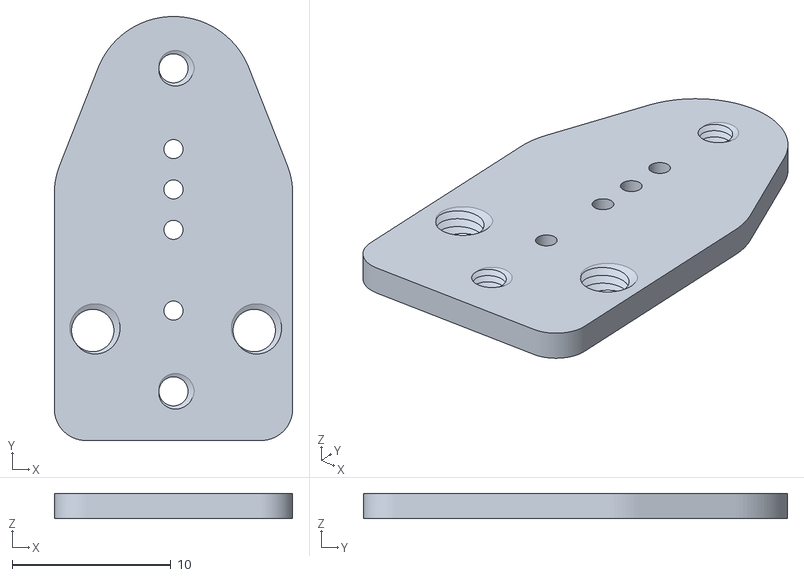
[picture p111: CAD file, 2020-12-01]
scad/board-with_threads.stl
15.0 x 26.7 x 1.60
