nionio6915/Euclid_Probe/stls/Building Blocks/Grafting_DockV3.stl

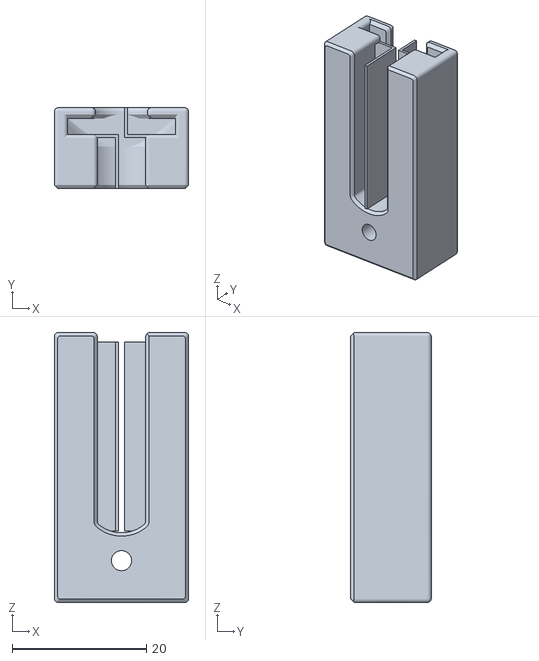
[picture p112: CAD file, 2021-12-24]
stls/Building Blocks/Grafting_DockV3.stl
20.0 x 12.0 x 40.2
