nionio6915/Euclid_Probe/stls/Bump Dock/dock_V5.stl

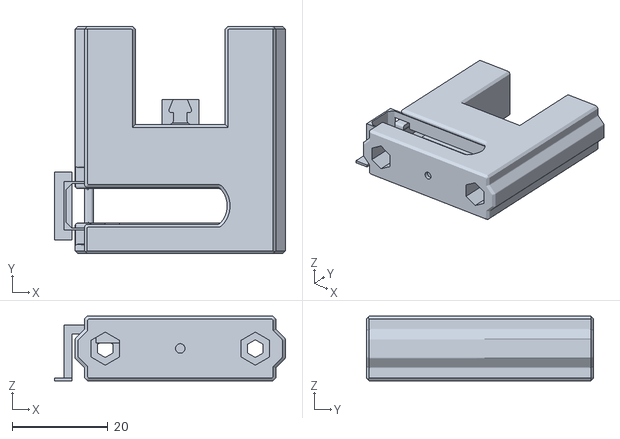
[picture p113: CAD file, 2023-03-30]
stls/Bump Dock/dock_V5.stl
48.3 x 47.6 x 13.5
