nionio6915/Euclid_Probe/stls/Ender3/M4_DblNut_Spacer_Handwheels.stl

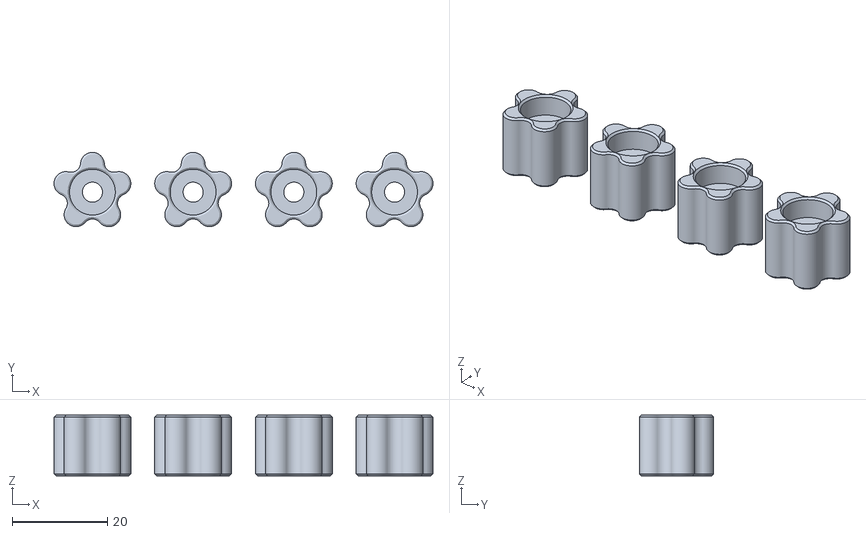
[picture p114: CAD file, 2022-03-24]
stls/Ender3/M4_DblNut_Spacer_Handwheels.stl
79.5 x 15.6 x 12.7
