nionio6915/Euclid_Probe/stls/Ender5/Ender5MountV8_Alt.stl

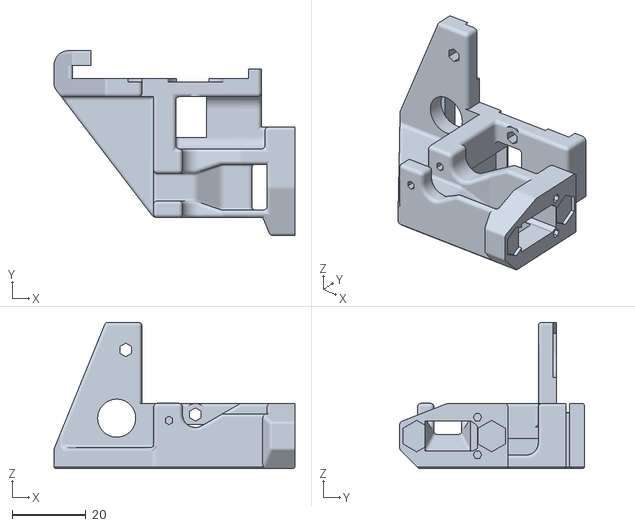
[picture p115: CAD file, 2021-12-24]
stls/Ender5/Ender5MountV8_Alt.stl
65.3 x 50.1 x 39.7
