nionio6915/Euclid_Probe/stls/FlashForgeCreator-Qidi/PartFanCoolingDuct.stl

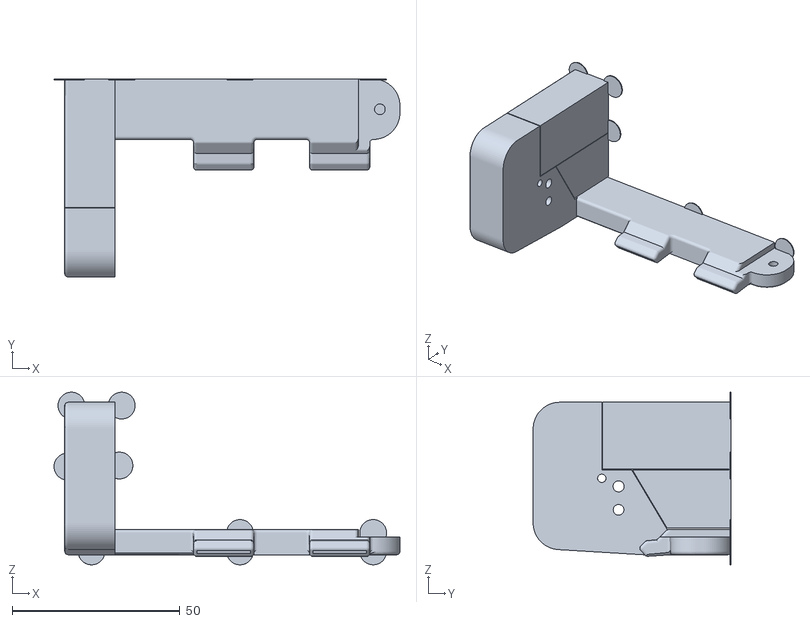
[picture p117: CAD file, 2023-03-03]
stls/FlashForgeCreator-Qidi/PartFanCoolingDuct.stl
103.2 x 59.0 x 51.5
