nionio6915/Euclid_Probe/stls/Mount Adapters/12mmInductive.stl

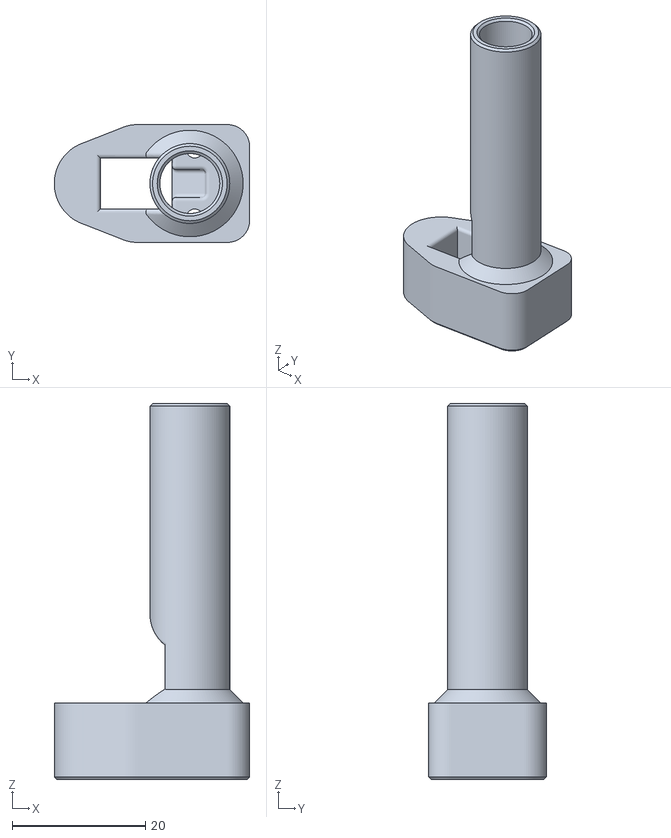
[picture p118: CAD file, 2021-08-17]
stls/Mount Adapters/12mmInductive.stl
29.4 x 17.7 x 56.5
