nionio6915/Euclid_Probe/stls/Mount Adapters/2020_End_Mount/2020_Rail_Horiz_PIPSprts.stl

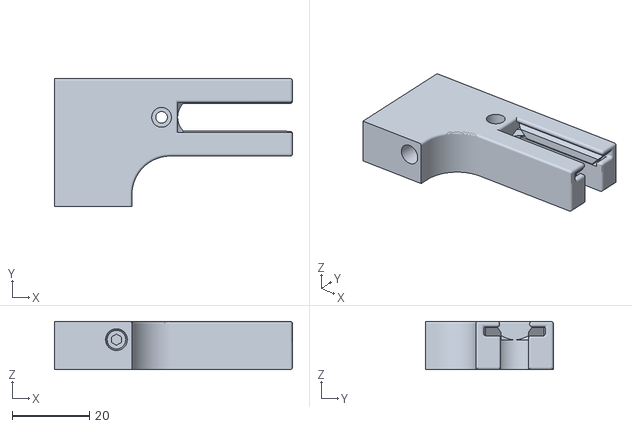
[picture p119: CAD file, 2021-06-21]
stls/Mount Adapters/2020_End_Mount/2020_Rail_Horiz_PIPSprts.stl
61.4 x 33.0 x 12.4
