nionio6915/Euclid_Probe/stls/Mount Adapters/BLTouch/BLTouch-M3HeatSerts.stl

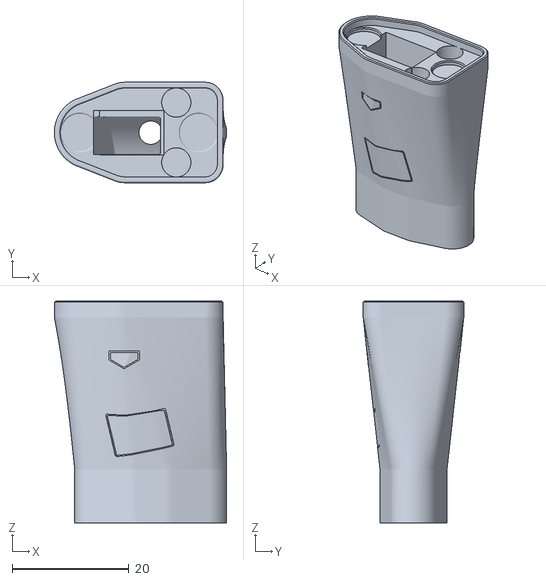
[picture p120: CAD file, 2022-03-06]
stls/Mount Adapters/BLTouch/BLTouch-M3HeatSerts.stl
29.5 x 17.2 x 38.0
