nionio6915/Euclid_Probe/stls/Mount Adapters/Omron/OmronFotek_90_V4.stl

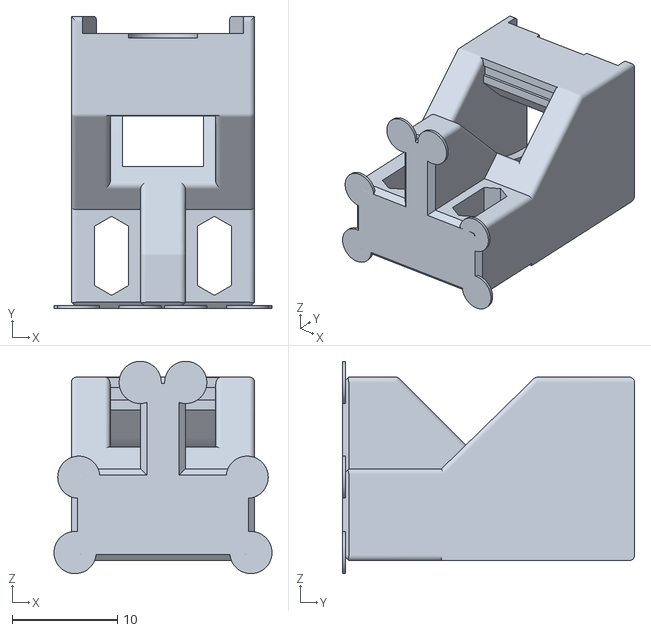
[picture p121: CAD file, 2022-10-25]
stls/Mount Adapters/Omron/OmronFotek_90_V4.stl
20.7 x 27.7 x 20.1
