nionio6915/Euclid_Probe/stls/Rail Core/1515ExpanderDrillingJigM3Nuts.stl

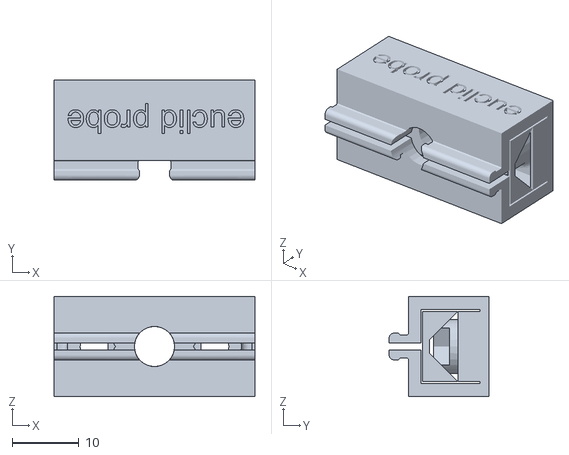
[picture p123: CAD file, 2023-03-29]
stls/Rail Core/1515ExpanderDrillingJigM3Nuts.stl
30.0 x 14.9 x 15.0
