nionio6915/Euclid_Probe/stls/UserContrib/esc247_vzbot_vzprinthead/VoronGantryMountRev_4_Set.stl

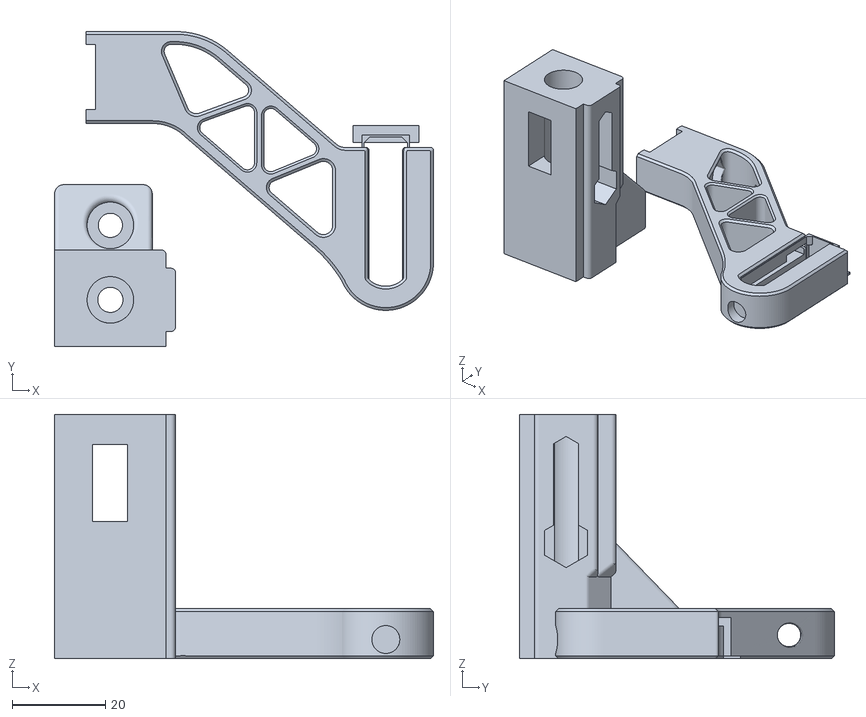
[picture p124: CAD file, 2022-05-12]
stls/UserContrib/esc247_vzbot_vzprinthead/VoronGantryMountRev_4_Set.stl
81.4 x 67.6 x 52.4
