nionio6915/Euclid_Probe/stls/V-Core/EVA_Mount/EuclidMount_EVA3_0_v05.stl

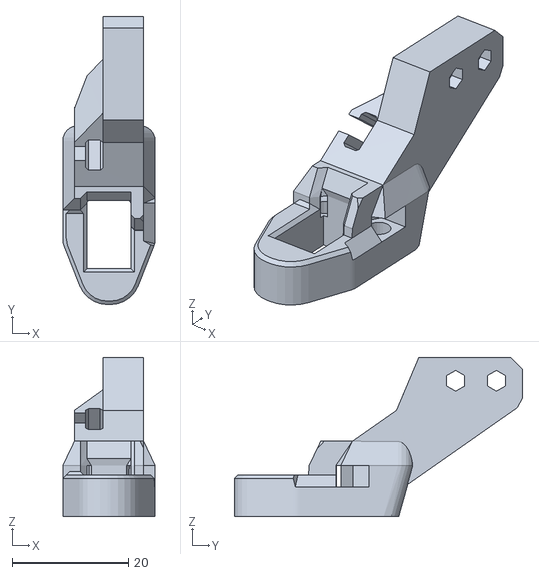
[picture p125: CAD file, 2022-06-29]
stls/V-Core/EVA_Mount/EuclidMount_EVA3_0_v05.stl
15.9 x 49.5 x 27.3
