nionio6915/Euclid_Probe/stls/Voron/User_Contrib/Dust_Euclid_Dock.stl

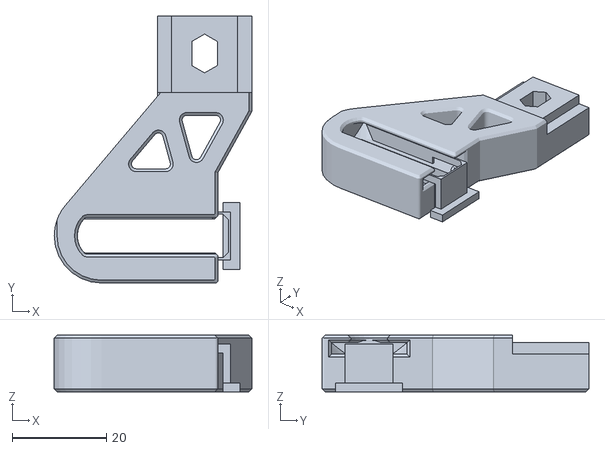
[picture p127: CAD file, 2022-11-09]
stls/Voron/User_Contrib/Dust_Euclid_Dock.stl
41.8 x 56.6 x 12.0
