nionio6915/Euclid_Probe/CAD/Ender/Ender5DockV7.stp

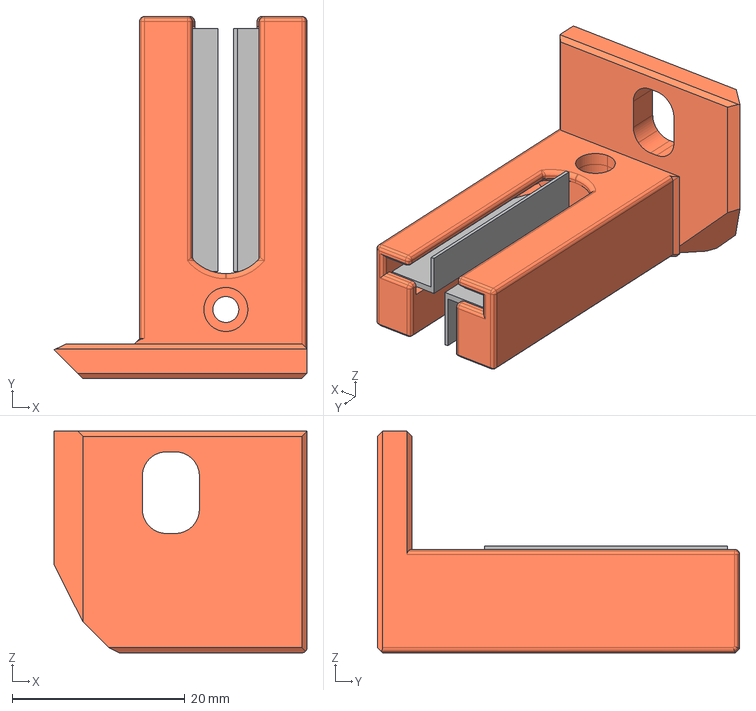
[picture p128: CAD file, 2022-04-05]
CAD/Ender/Ender5DockV7.stp
29.3 x 42.0 x 25.7 mm
