nionio6915/Euclid_Probe/CAD/PROBE-BOARD_Bot.step

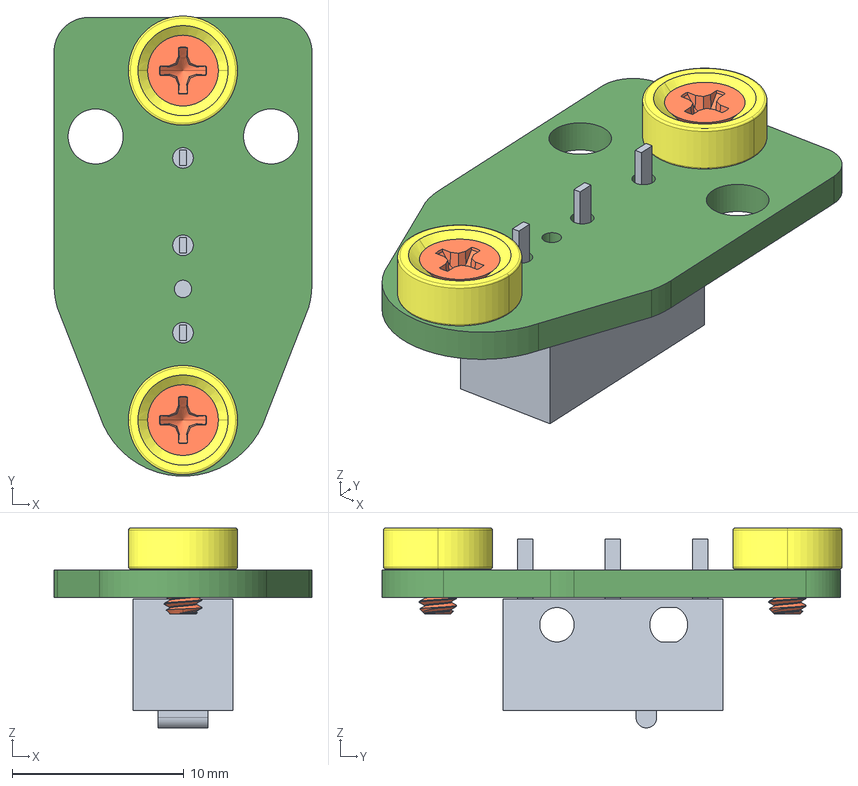
[picture p129: CAD file, 2020-11-25]
CAD/PROBE-BOARD_Bot.step
15.0 x 26.7 x 11.6 mm
