nionio6915/Euclid_Probe/CAD/RailCore/RC_Corner1515_DockMountV4.stp

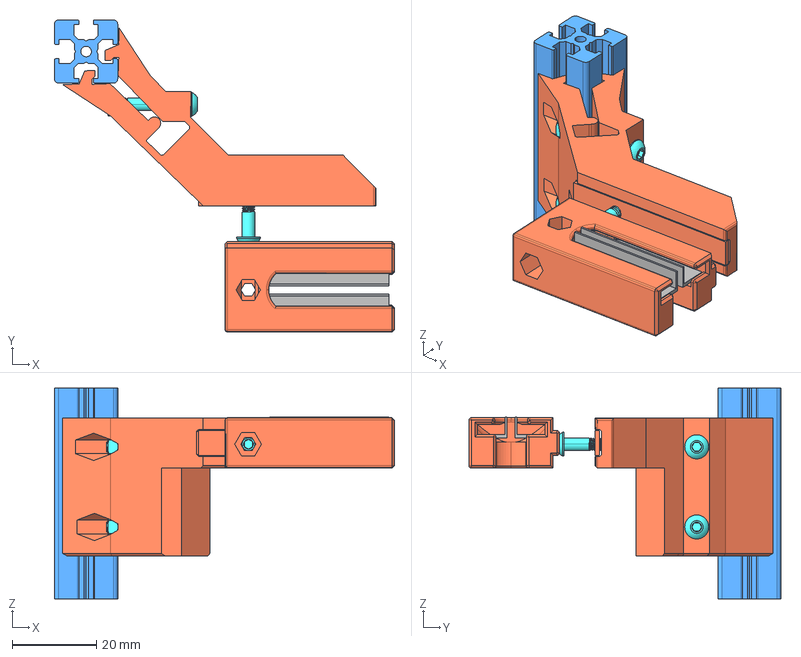
[picture p130: CAD file, 2022-05-06]
CAD/RailCore/RC_Corner1515_DockMountV4.stp
80.6 x 74.0 x 50.0 mm
