nionio6915/Euclid_Probe/CAD/Rat-Rig V-Core/VCoreProDock_2040.stp

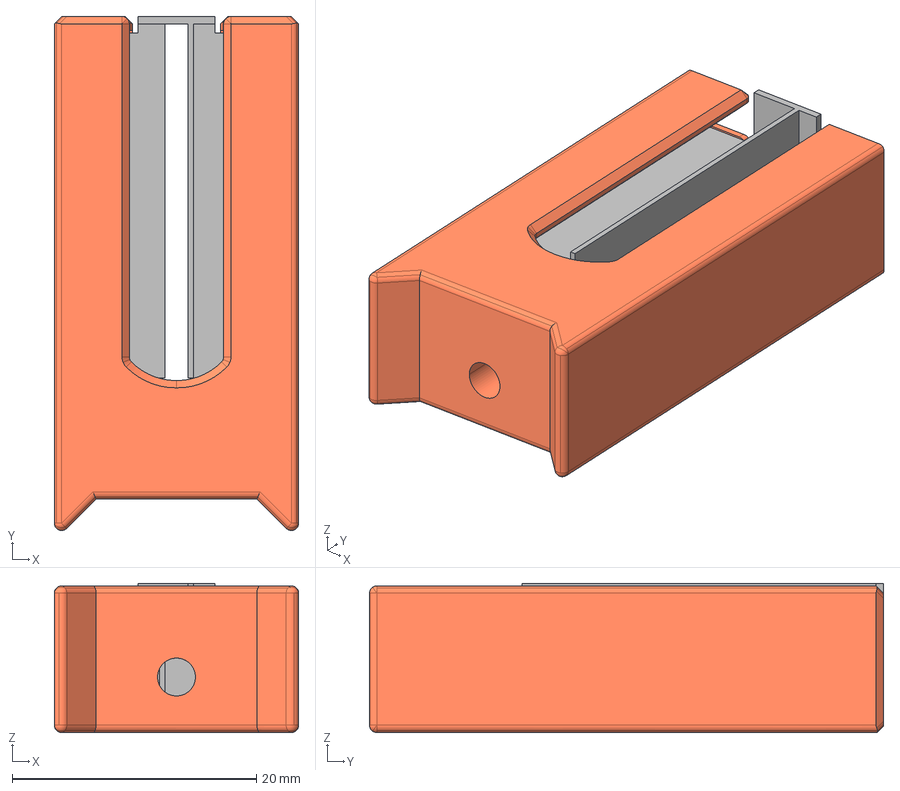
[picture p131: CAD file, 2021-12-30]
CAD/Rat-Rig V-Core/VCoreProDock_2040.stp
20.0 x 42.1 x 12.2 mm
