nionio6915/Euclid_Probe/CAD/Voron/Voron2.4BedMountV3.stp

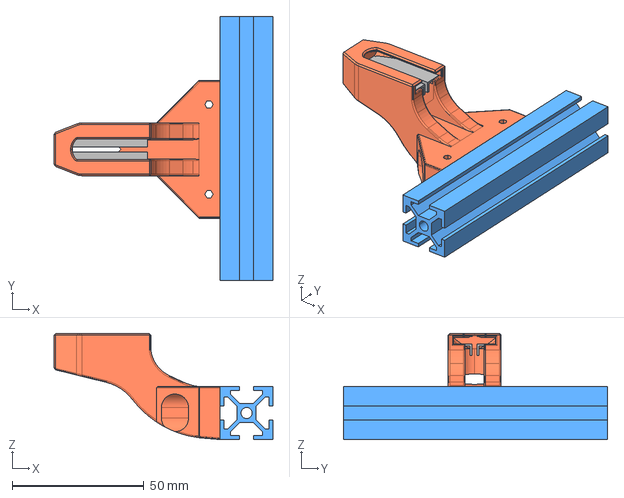
[picture p132: CAD file, 2022-06-29]
CAD/Voron/Voron2.4BedMountV3.stp
82.9 x 100.0 x 40.2 mm
