nionio6915/Euclid_Probe/scad/board.stl

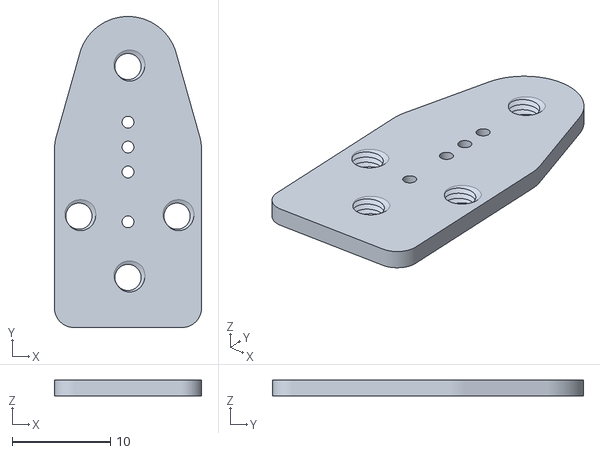
[picture p133: CAD file, 2020-11-25]
scad/board.stl
15.0 x 31.7 x 1.60
