nionio6915/Euclid_Probe/stls/Building Blocks/Modular_Parts.stl

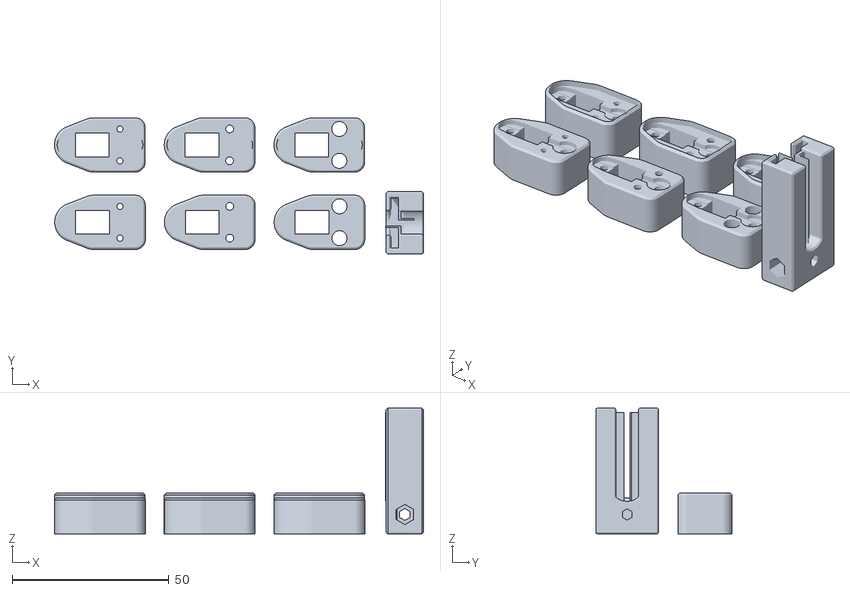
[picture p134: CAD file, 2021-12-06]
stls/Building Blocks/Modular_Parts.stl
117.7 x 43.5 x 40.2
