nionio6915/Euclid_Probe/stls/Ender3/Ender3DockMountV4.stl

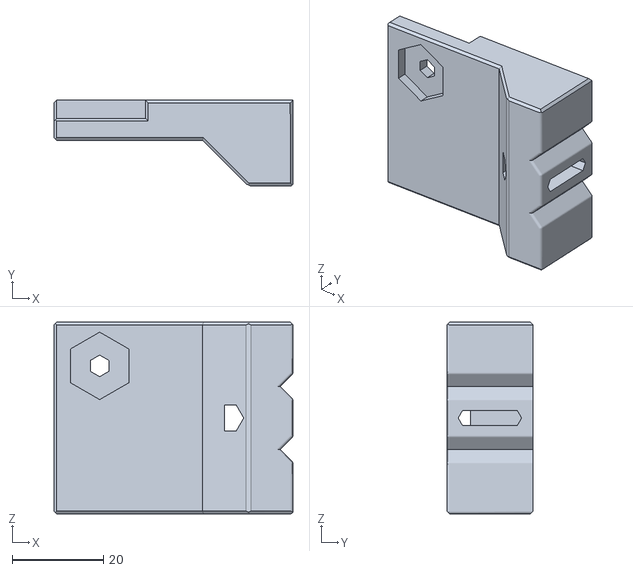
[picture p135: CAD file, 2021-12-08]
stls/Ender3/Ender3DockMountV4.stl
52.3 x 18.8 x 42.0
