nionio6915/Euclid_Probe/stls/Ender5/Ender5DockV8.stl

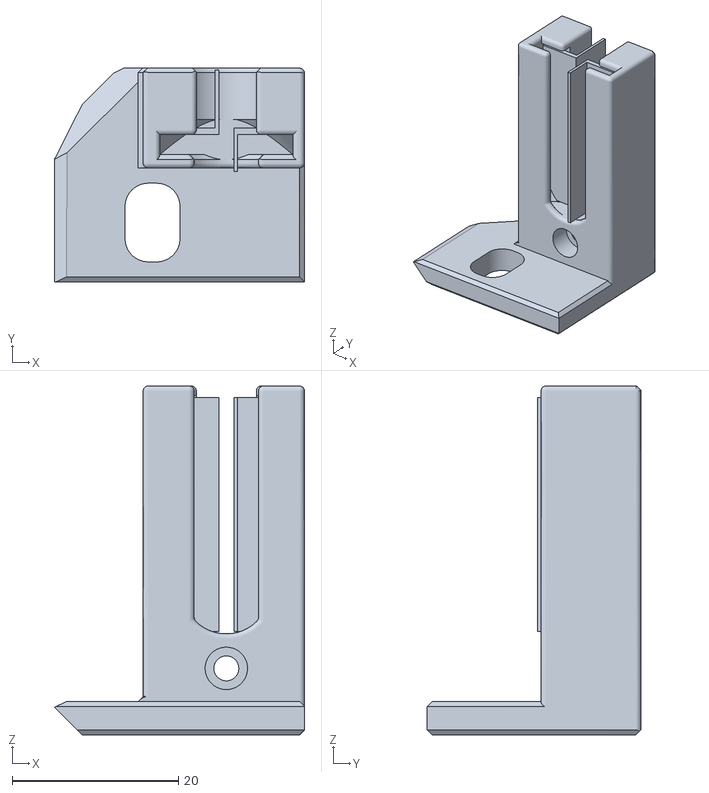
[picture p136: CAD file, 2021-12-08]
stls/Ender5/Ender5DockV8.stl
30.1 x 25.7 x 42.0
