nionio6915/Euclid_Probe/stls/Fan Mounts/5015_LeftV4.stl

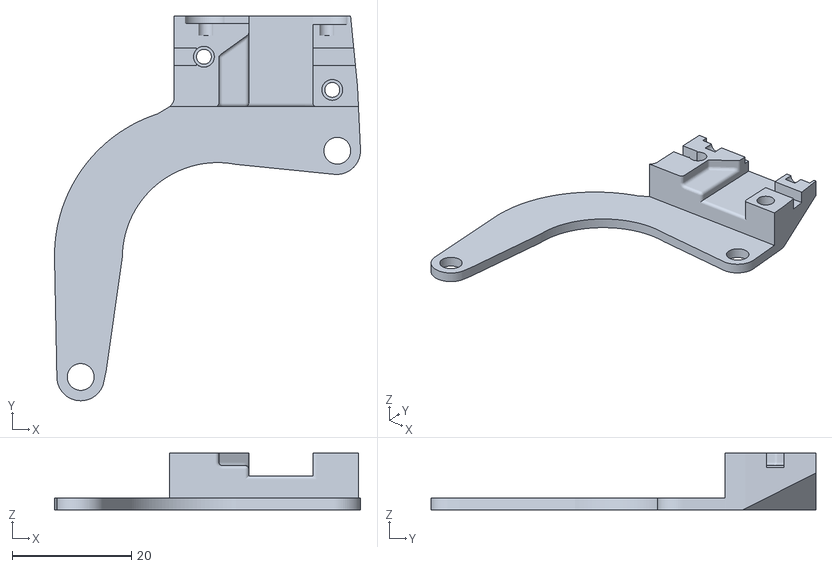
[picture p137: CAD file, 2021-12-24]
stls/Fan Mounts/5015_LeftV4.stl
51.4 x 64.6 x 9.50
