nionio6915/Euclid_Probe/stls/FlashForgeCreator-Qidi/DuctSupport.stl

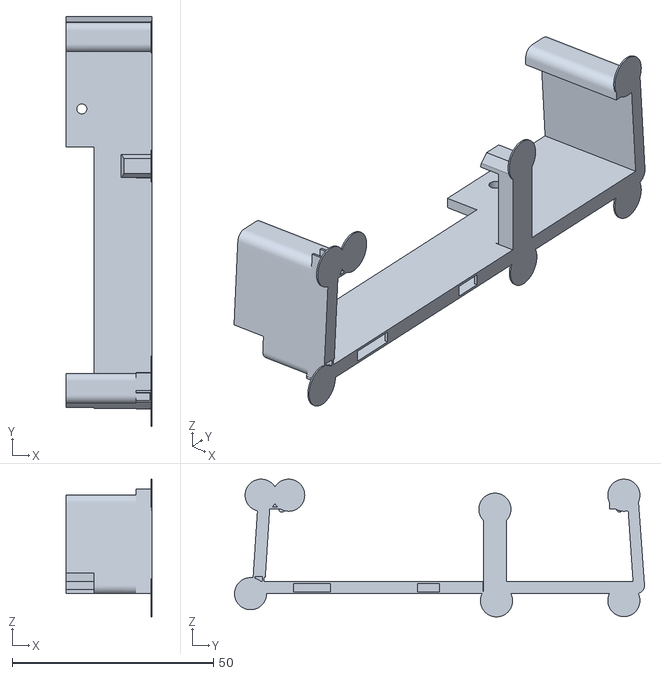
[picture p138: CAD file, 2023-03-03]
stls/FlashForgeCreator-Qidi/DuctSupport.stl
21.5 x 102.0 x 34.3
