nionio6915/Euclid_Probe/stls/Mount Adapters/BLTouch/BLTouch4HypercubeM3Nuts.stl

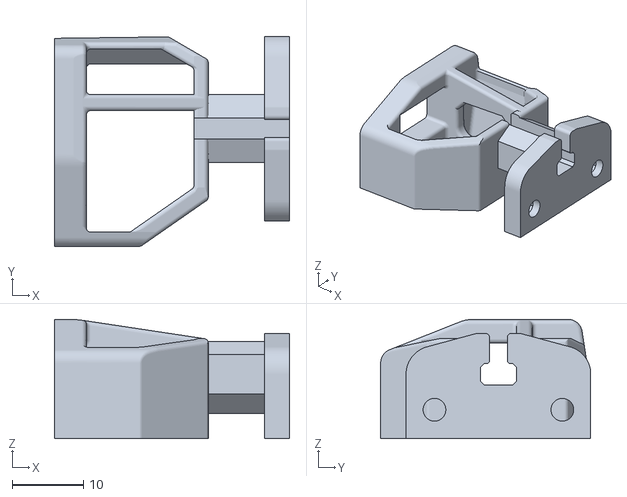
[picture p139: CAD file, 2022-01-26]
stls/Mount Adapters/BLTouch/BLTouch4HypercubeM3Nuts.stl
33.1 x 29.5 x 16.8
