nionio6915/Euclid_Probe/stls/probe-dock_fixed_1.stl

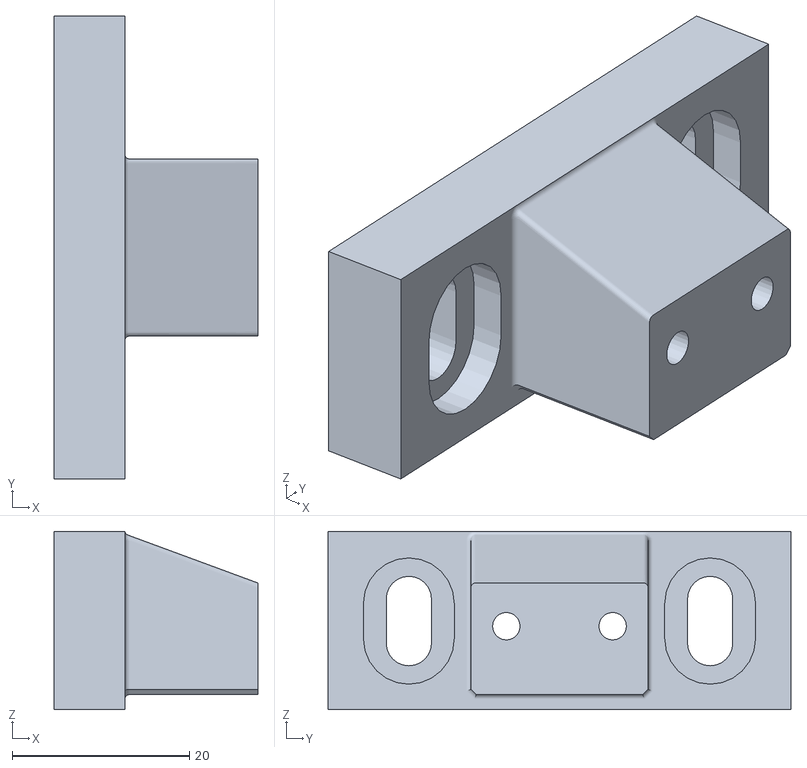
[picture p141: CAD file, 2021-06-21]
stls/probe-dock_fixed_1.stl
23.0 x 52.2 x 20.1
