nionio6915/Euclid_Probe/stls/UserContrib/esc247_vzbot_vzprinthead/VoronGantryMountRev_4.stl

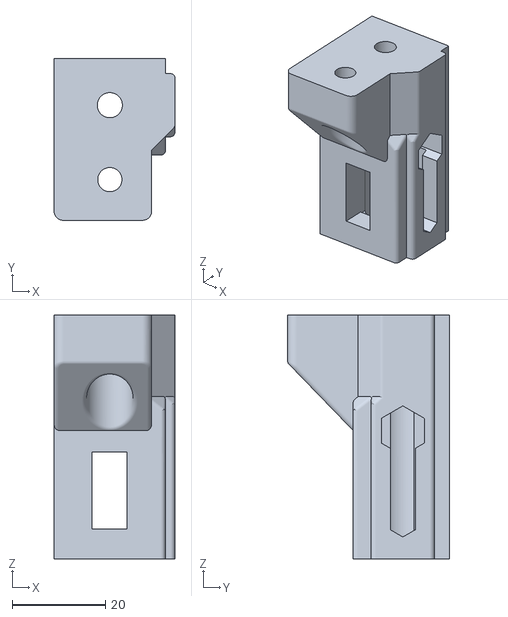
[picture p142: CAD file, 2022-04-10]
stls/UserContrib/esc247_vzbot_vzprinthead/VoronGantryMountRev_4.stl
26.0 x 34.8 x 52.4
