nionio6915/Euclid_Probe/stls/Voron/User_Contrib/euclid_mgn12_cw2_left.3mf

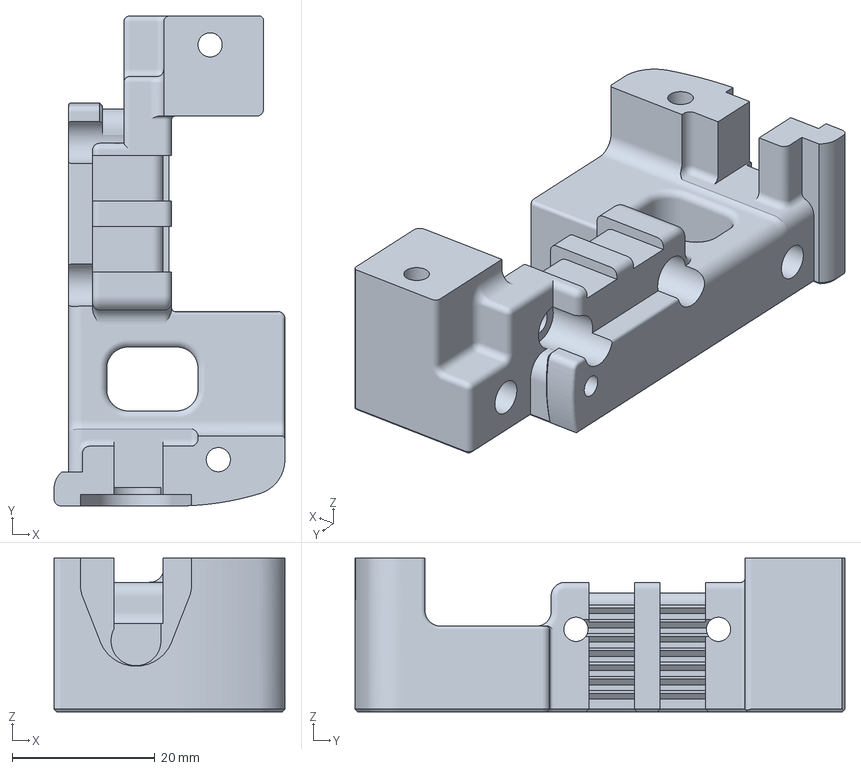
[picture p143: CAD file, 2022-07-11]
stls/Voron/User_Contrib/euclid_mgn12_cw2_left.3mf
32.4 x 68.8 x 21.6 mm
