nionio6915/Euclid_Probe/stls/Voron/Voron_Adjustable_Bed_DockV2A.stl

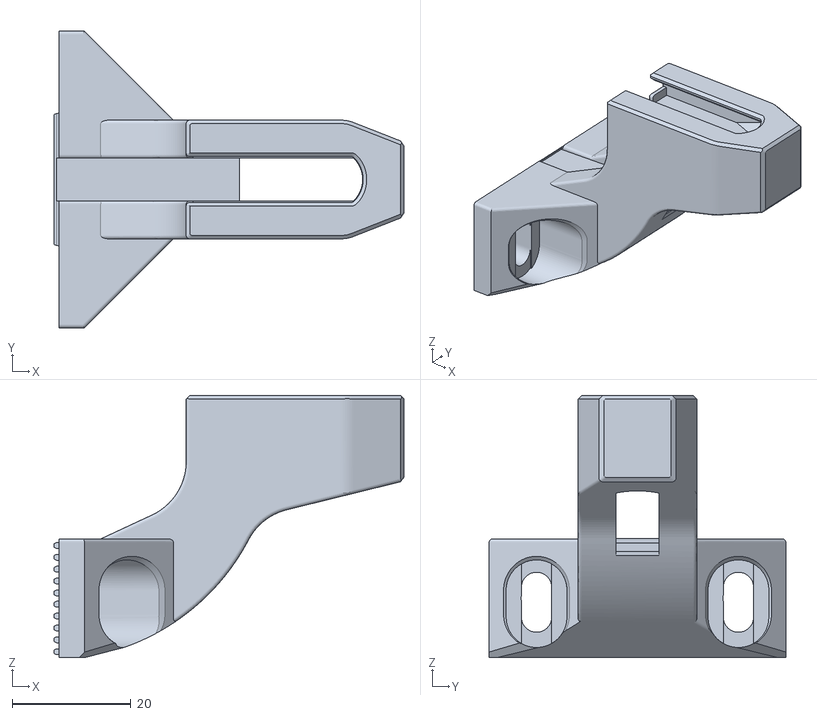
[picture p144: CAD file, 2022-06-27]
stls/Voron/Voron_Adjustable_Bed_DockV2A.stl
58.9 x 50.0 x 44.2
