nionio6915/Euclid_Probe/CAD/Ender/Ender3_Dock_Modular_All_Parts.stp

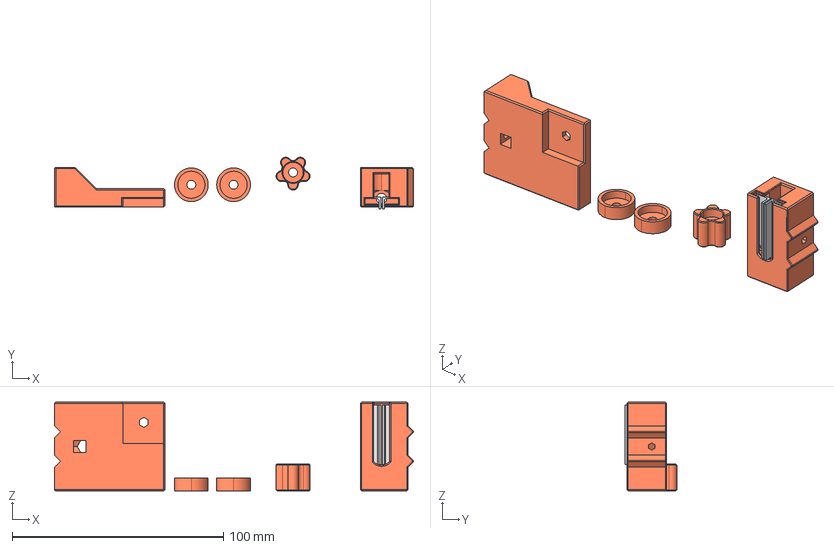
[picture p145: CAD file, 2022-04-05]
CAD/Ender/Ender3_Dock_Modular_All_Parts.stp
170.1 x 24.5 x 42.0 mm
