nionio6915/Euclid_Probe/CAD/PROBE-BOARD.step

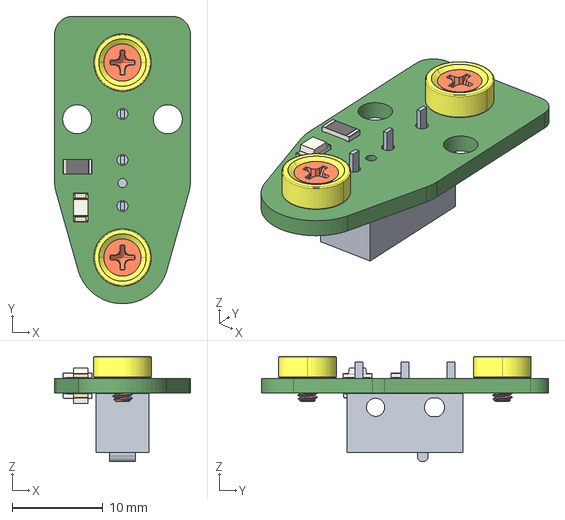
[picture p146: CAD file, 2020-11-21]
CAD/PROBE-BOARD.step
15.0 x 31.7 x 11.6 mm
