nionio6915/Euclid_Probe/CAD/RailCore/RailcoreMount713Native.stp

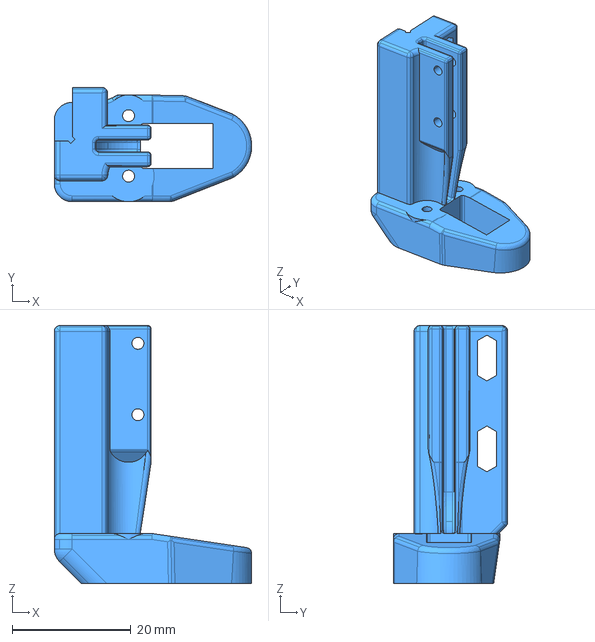
[picture p147: CAD file, 2022-04-20]
CAD/RailCore/RailcoreMount713Native.stp
33.2 x 19.2 x 43.4 mm
