nionio6915/Euclid_Probe/CAD/Rat-Rig V-Core/VCoreProDockMount2040.stp

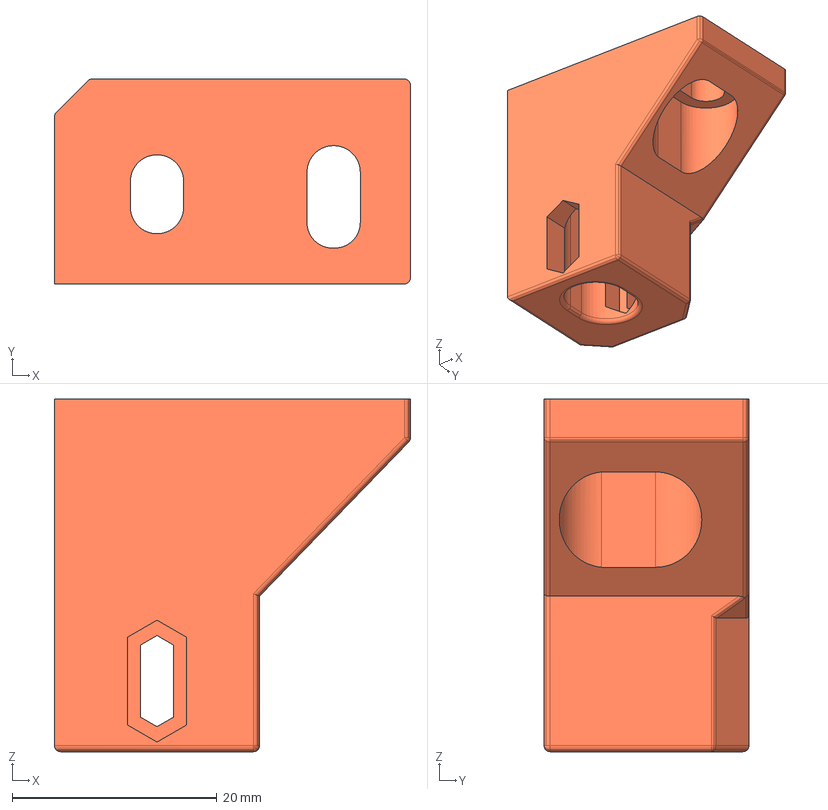
[picture p148: CAD file, 2021-12-30]
CAD/Rat-Rig V-Core/VCoreProDockMount2040.stp
34.7 x 20.0 x 34.4 mm
