nionio6915/Euclid_Probe/CAD/Voron/Voron2.4BedMount_TallerV3.stp

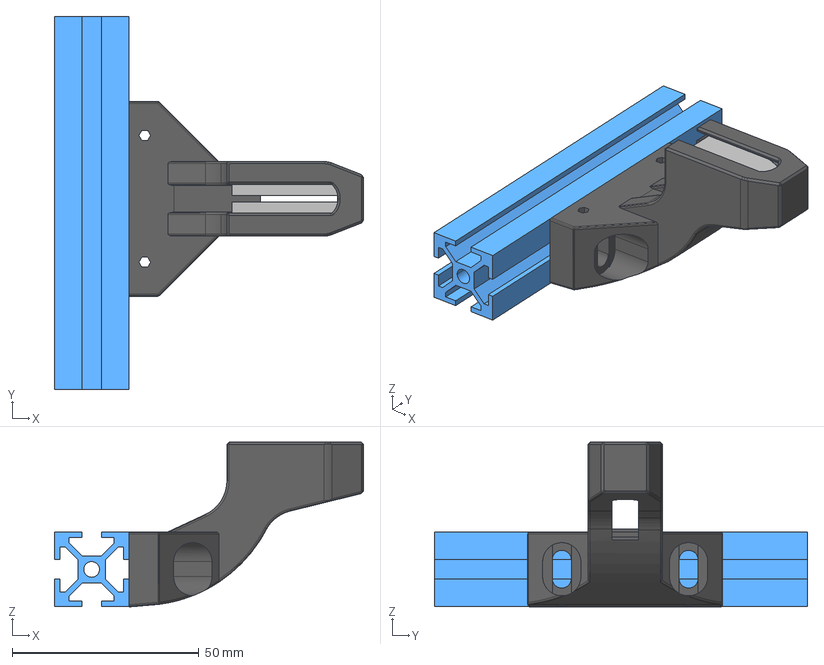
[picture p149: CAD file, 2022-06-29]
CAD/Voron/Voron2.4BedMount_TallerV3.stp
82.9 x 100.0 x 44.2 mm
