nionio6915/Euclid_Probe/stls/Ender3/Ender3DockV4.stl

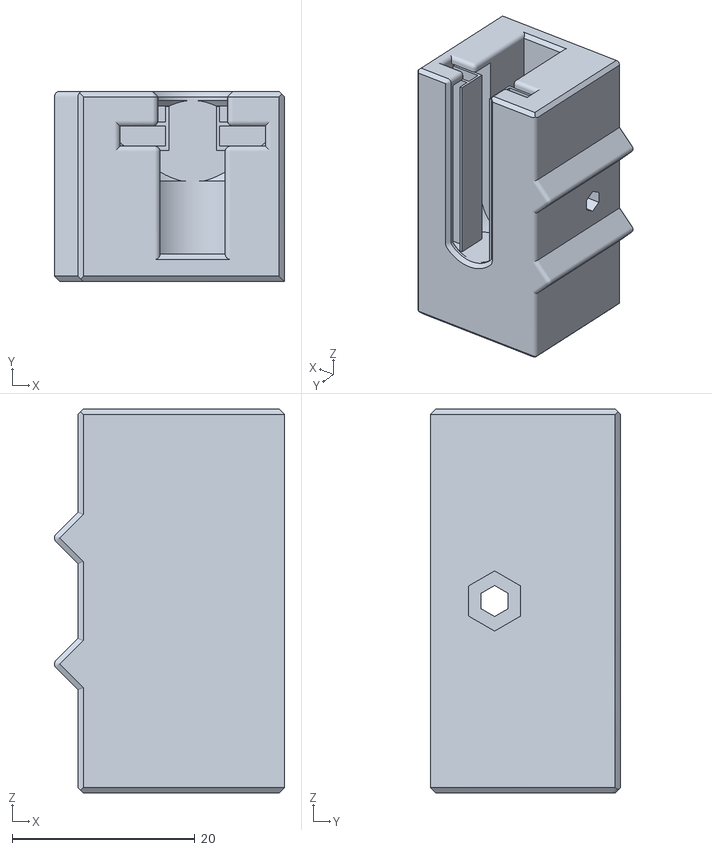
[picture p151: CAD file, 2021-12-06]
stls/Ender3/Ender3DockV4.stl
25.2 x 20.8 x 42.0
