nionio6915/Euclid_Probe/stls/FlashForgeCreator-Qidi/FanDuctSupport6.stl

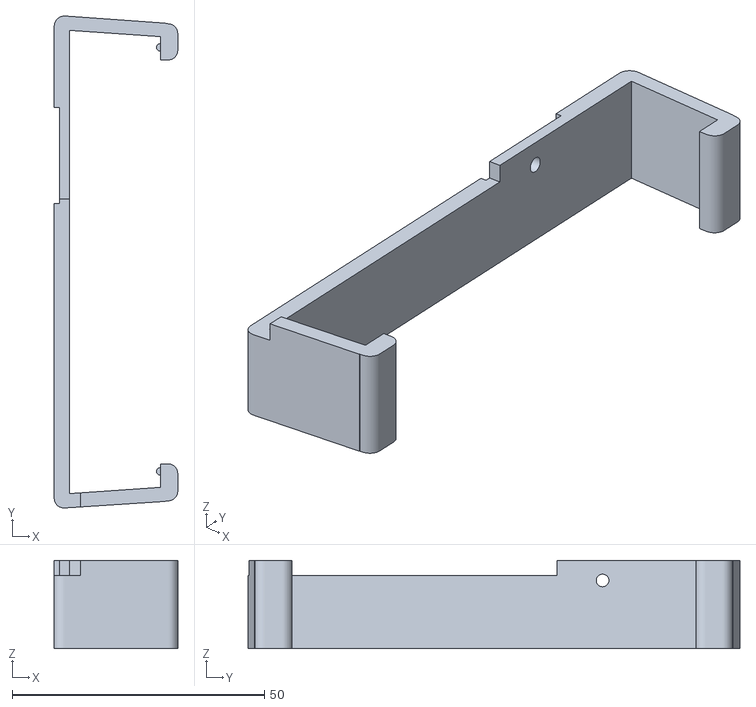
[picture p152: CAD file, 2021-12-10]
stls/FlashForgeCreator-Qidi/FanDuctSupport6.stl
24.5 x 97.5 x 17.5
