nionio6915/Euclid_Probe/stls/Mount Adapters/Omron/OmronFotek90HeatsertV3.stl

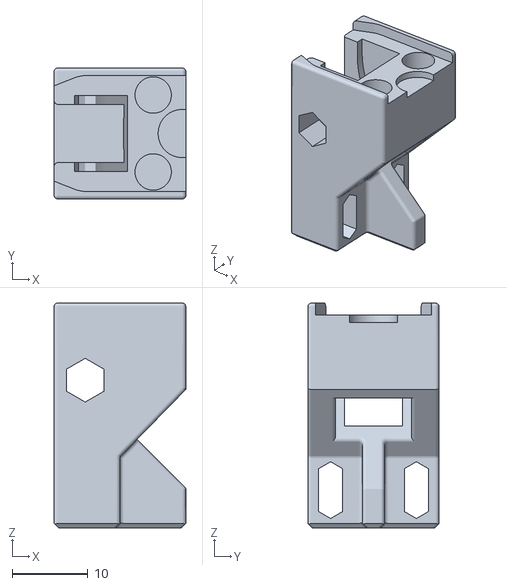
[picture p153: CAD file, 2021-12-12]
stls/Mount Adapters/Omron/OmronFotek90HeatsertV3.stl
17.4 x 17.3 x 29.7
