nionio6915/Euclid_Probe/stls/probe-dock_fixed_2PIP.stl

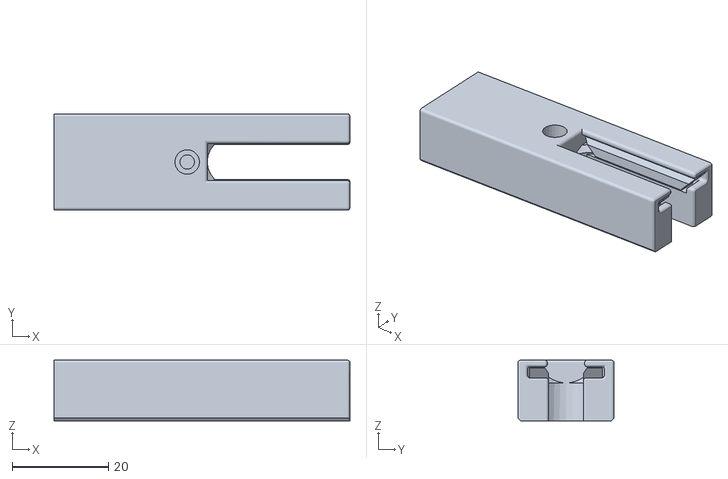
[picture p154: CAD file, 2021-06-21]
stls/probe-dock_fixed_2PIP.stl
61.4 x 20.0 x 12.6
