nionio6915/Euclid_Probe/stls/Rail Core/1515ExpanderDrillingJigHeatsert85deg.stl

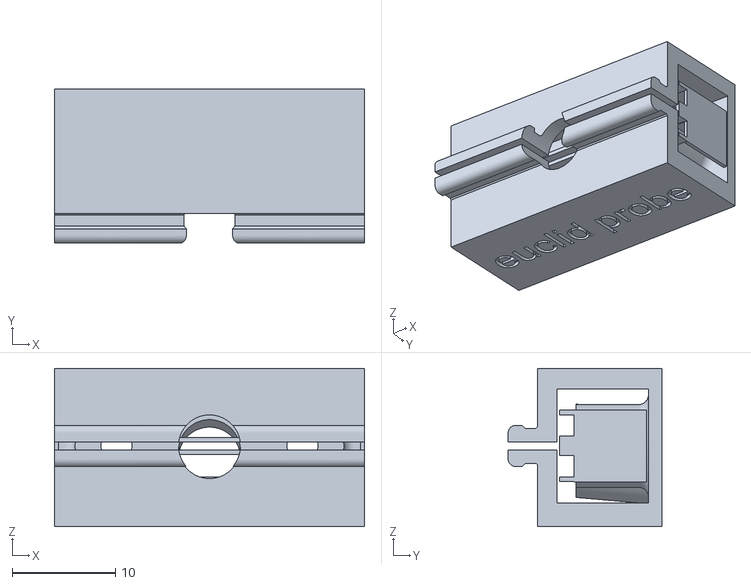
[picture p155: CAD file, 2022-04-08]
stls/Rail Core/1515ExpanderDrillingJigHeatsert85deg.stl
30.0 x 14.9 x 15.3
