nionio6915/Euclid_Probe/stls/UserContrib/esc247_vzbot_vzprinthead/VoronGantryMountRev_4Dock.stl

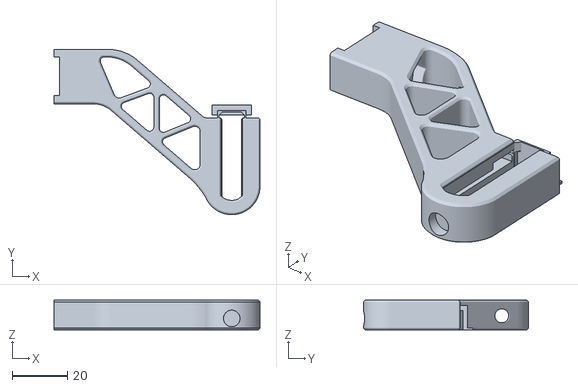
[picture p156: CAD file, 2022-04-10]
stls/UserContrib/esc247_vzbot_vzprinthead/VoronGantryMountRev_4Dock.stl
74.6 x 59.9 x 10.7
