nionio6915/Euclid_Probe/stls/Voron/Voron_Adjustable_Bed_DockV2B.stl

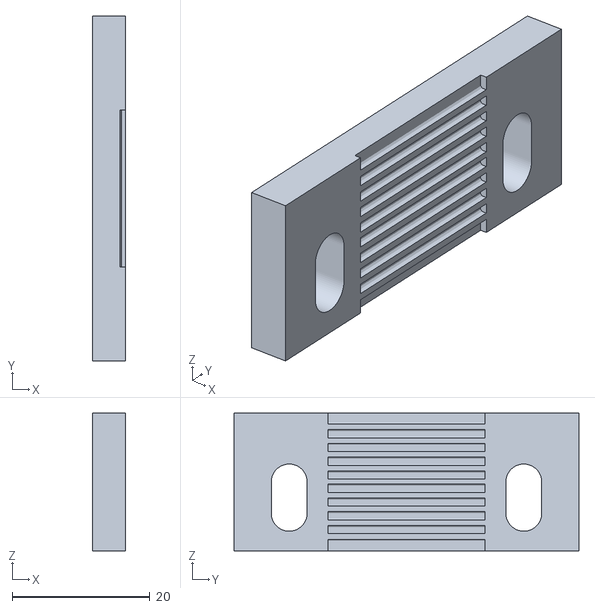
[picture p158: CAD file, 2022-06-27]
stls/Voron/Voron_Adjustable_Bed_DockV2B.stl
4.80 x 50.0 x 20.0
