nionio6915/Euclid_Probe/CAD/Ender/Ender_Spacer_Handwheels.stp

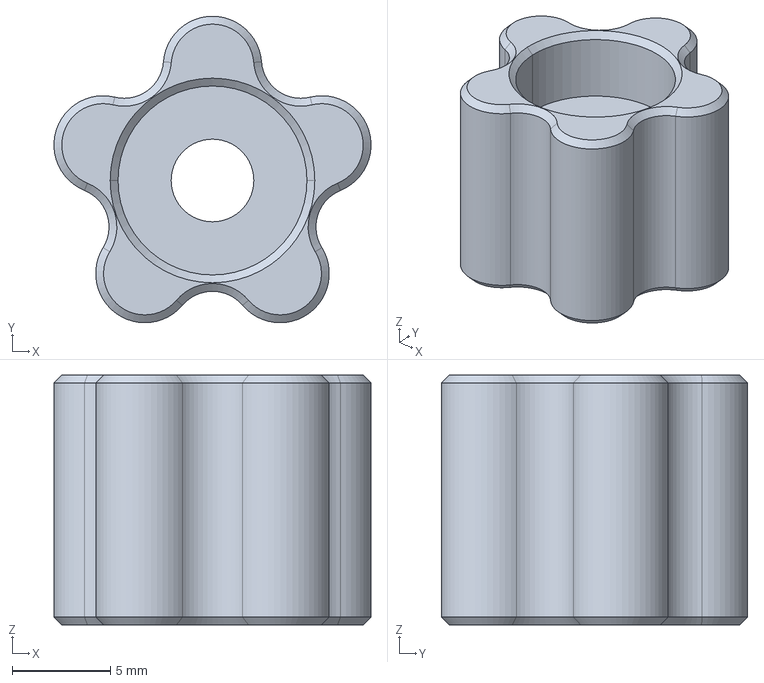
[picture p159: CAD file, 2022-04-05]
CAD/Ender/Ender_Spacer_Handwheels.stp
16.1 x 15.6 x 12.7 mm
