nionio6915/Euclid_Probe/CAD/MountAdapters/BLTouchV3.stp

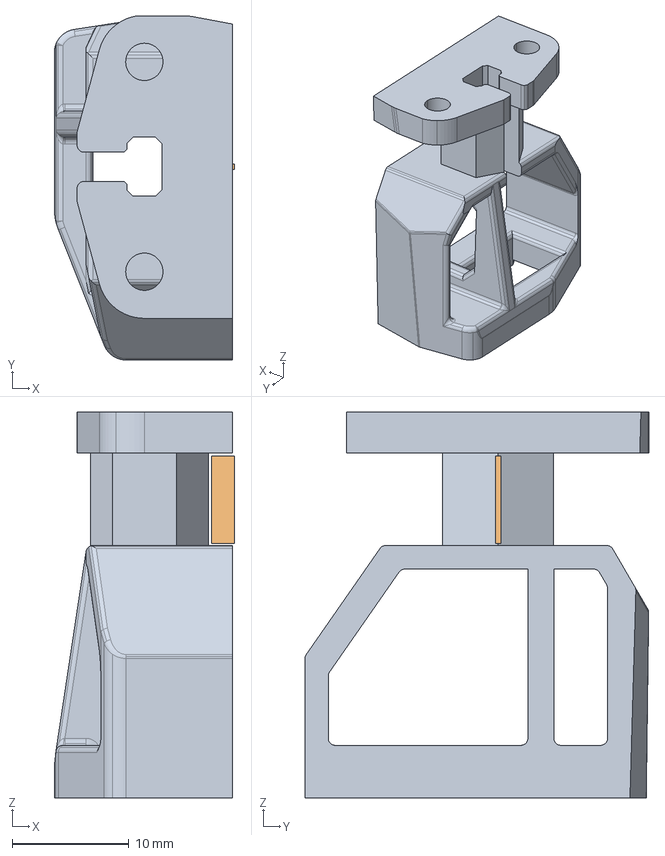
[picture p160: CAD file, 2022-03-06]
CAD/MountAdapters/BLTouchV3.stp
15.5 x 29.5 x 33.1 mm
