nionio6915/Euclid_Probe/CAD/RailCore/RailCoreMountMRW_SD_MountV4.stp

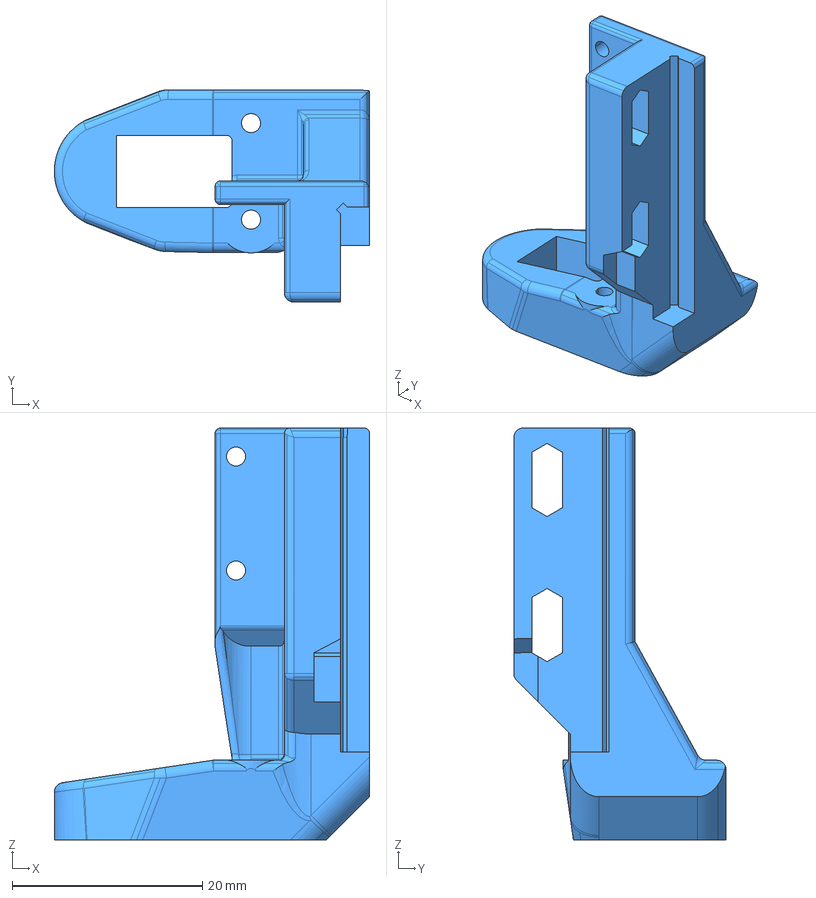
[picture p161: CAD file, 2022-01-05]
CAD/RailCore/RailCoreMountMRW_SD_MountV4.stp
33.2 x 22.3 x 43.4 mm
