nionio6915/Euclid_Probe/CAD/Voron/Gantry_Face_Mount.stp

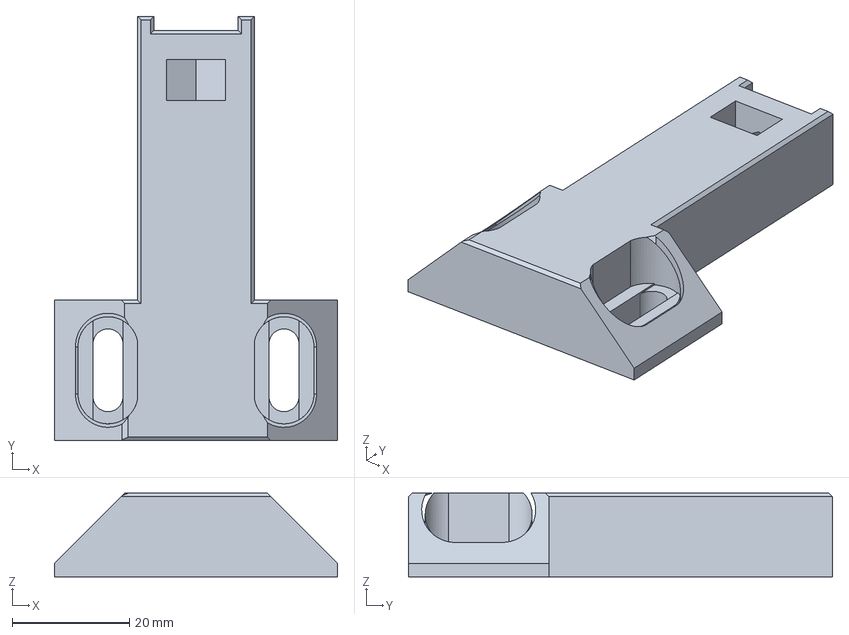
[picture p162: CAD file, 2022-06-27]
CAD/Voron/Gantry_Face_Mount.stp
48.2 x 72.4 x 14.3 mm
CADSOFTTOOLS 4.1
CADSOFTTOOLS 4.2
CADSOFTTOOLS 4.3
CADSOFTTOOLS 4.4
CADSOFTTOOLS 4.5
CADSOFTTOOLS 4.6
CADSOFTTOOLS 4.7
CADSOFTTOOLS 4.8
CADSOFTTOOLS 4.9
CADSOFTTOOLS 4.10
CADSOFTTOOLS 4.11
CADSOFTTOOLS 4.12
CADSOFTTOOLS 4.13
CADSOFTTOOLS 4.14
CADSOFTTOOLS 4.15
CADSOFTTOOLS 4.16
CADSOFTTOOLS 4.17
CADSOFTTOOLS 4.18
CADSOFTTOOLS 4.19
CADSOFTTOOLS 4.20
CADSOFTTOOLS 4.21
CADSOFTTOOLS 4.22
CADSOFTTOOLS 4.23
CADSOFTTOOLS 4.24
CADSOFTTOOLS 4.25
CADSOFTTOOLS 4.26
CADSOFTTOOLS 4.27
CADSOFTTOOLS 4.28
CADSOFTTOOLS 4.29
CADSOFTTOOLS 4.30
CADSOFTTOOLS 4.31
CADSOFTTOOLS 4.32
CADSOFTTOOLS 4.33
CADSOFTTOOLS 4.34
CADSOFTTOOLS 4.35
CADSOFTTOOLS 4.36
CADSOFTTOOLS 4.37
CADSOFTTOOLS 4.38
CADSOFTTOOLS 4.39
CADSOFTTOOLS 4.40
CADSOFTTOOLS 4.41
CADSOFTTOOLS 4.42
CADSOFTTOOLS 4.43
CADSOFTTOOLS 4.44
CADSOFTTOOLS 4.45
CADSOFTTOOLS 4.46
CADSOFTTOOLS 4.47
CADSOFTTOOLS 4.48
CADSOFTTOOLS 4.49
CADSOFTTOOLS 4.50
CADSOFTTOOLS 4.51
CADSOFTTOOLS 4.52
CADSOFTTOOLS 4.53
CADSOFTTOOLS 4.54
CADSOFTTOOLS 4.55
CADSOFTTOOLS 4.56
CADSOFTTOOLS 4.57
CADSOFTTOOLS 4.58
CADSOFTTOOLS 4.59
CADSOFTTOOLS 4.60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
