nionio6915/Euclid_Probe/stls/Building Blocks/Modular_Parts_M2.0Holes.stl

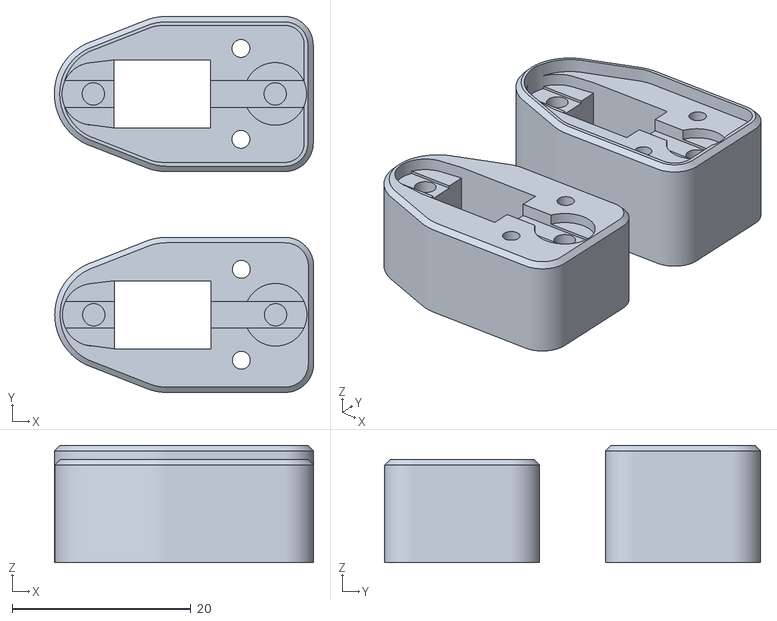
[picture p163: CAD file, 2021-12-06]
stls/Building Blocks/Modular_Parts_M2.0Holes.stl
29.0 x 42.0 x 13.1
