nionio6915/Euclid_Probe/stls/Ender3/Ender3SpacerRisers.stl

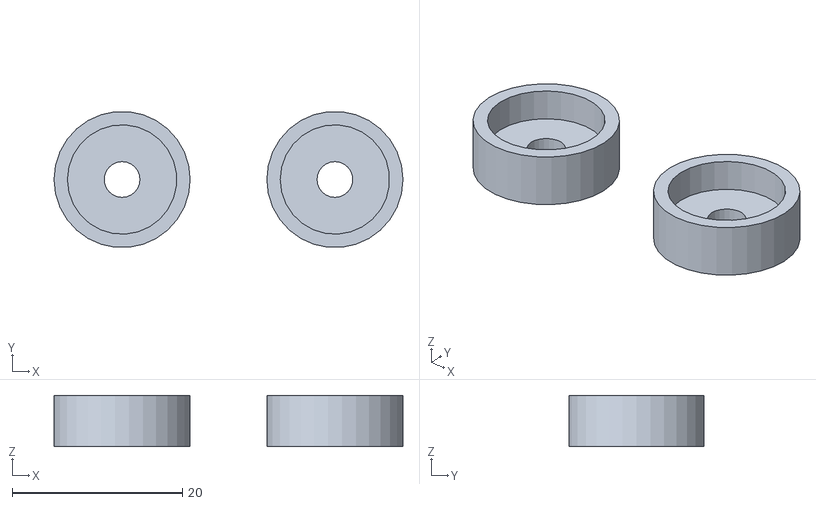
[picture p164: CAD file, 2021-09-30]
stls/Ender3/Ender3SpacerRisers.stl
41.0 x 15.9 x 6.00
