nionio6915/Euclid_Probe/stls/FlashForgeCreator-Qidi/FanBracketV6.stl

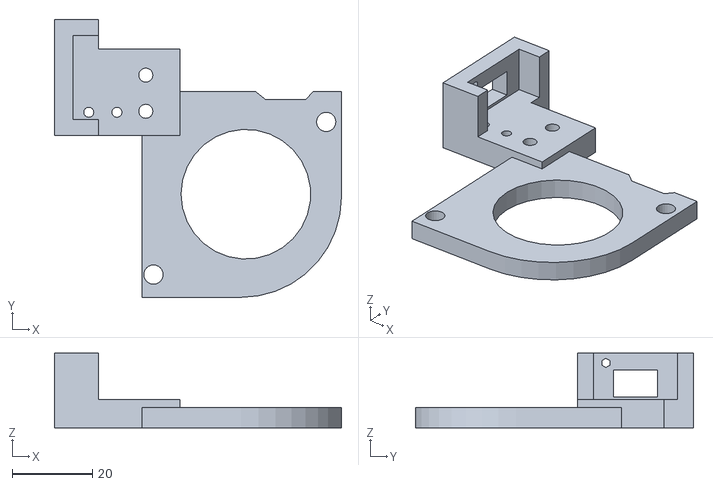
[picture p165: CAD file, 2021-12-10]
stls/FlashForgeCreator-Qidi/FanBracketV6.stl
71.4 x 69.1 x 18.6
