nionio6915/Euclid_Probe/stls/UserContrib/esc247_vzbot_vzprinthead/VoronGantryMountRev2_Short.stl

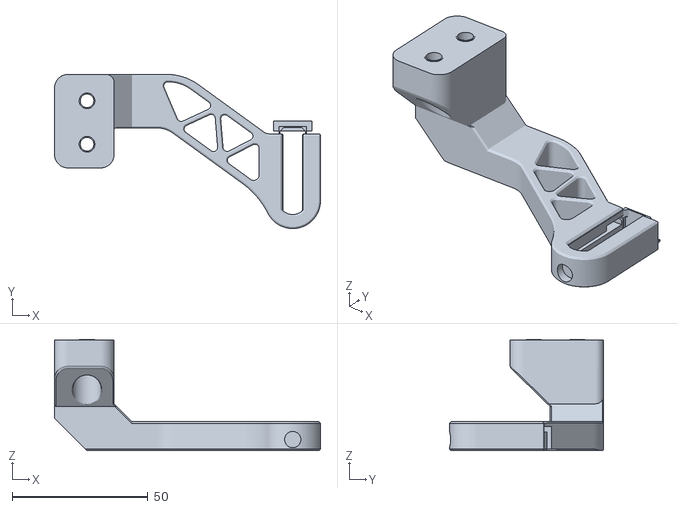
[picture p166: CAD file, 2022-03-30]
stls/UserContrib/esc247_vzbot_vzprinthead/VoronGantryMountRev2_Short.stl
98.1 x 56.9 x 41.1
