nionio6915/Euclid_Probe/stls/Voron/User_Contrib/Euclid_x_carriage_mgn12_m3_locknut_for_new_lgx_adapter.3mf

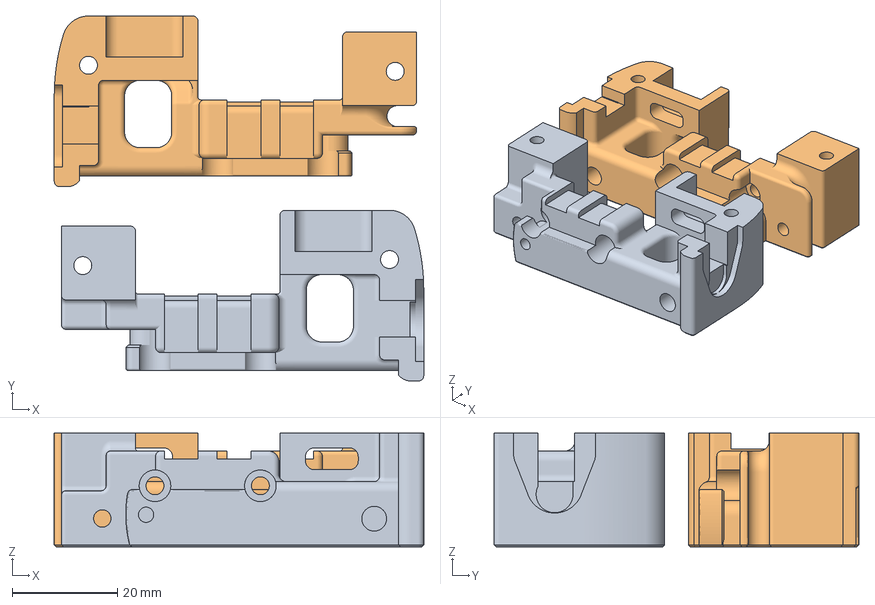
[picture p167: CAD file, 2022-07-11]
stls/Voron/User_Contrib/Euclid_x_carriage_mgn12_m3_locknut_for_new_lgx_adapter.3mf
70.1 x 69.3 x 21.6 mm
