nionio6915/Euclid_Probe/stls/Voron/Voron_Adjustable_Bed_Dock_Experimental_1.stl

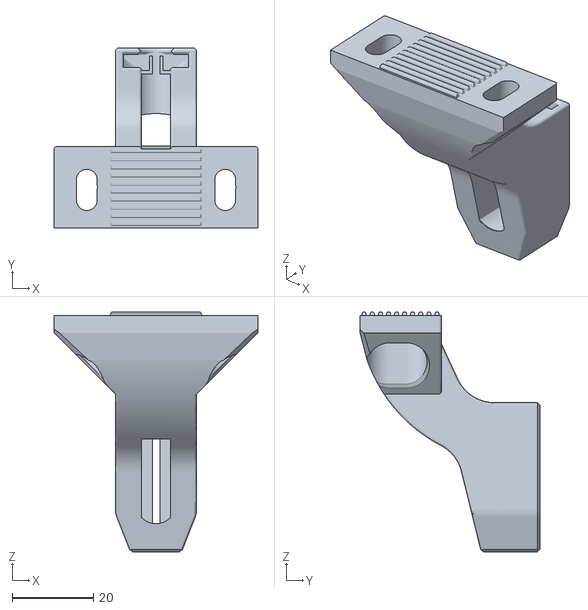
[picture p168: CAD file, 2022-06-12]
stls/Voron/Voron_Adjustable_Bed_Dock_Experimental_1.stl
50.0 x 44.2 x 58.9
