nionio6915/Euclid_Probe/CAD/RailCore/RailCoreDockTopMountV3.stp

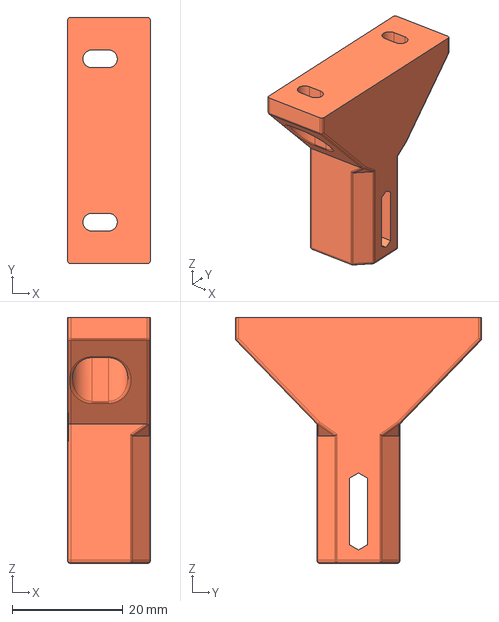
[picture p169: CAD file, 2021-07-21]
CAD/RailCore/RailCoreDockTopMountV3.stp
15.0 x 44.5 x 44.4 mm
