nionio6915/Euclid_Probe/CAD/Voron/Gantry_Face_Mount_90dock_Dock.stp

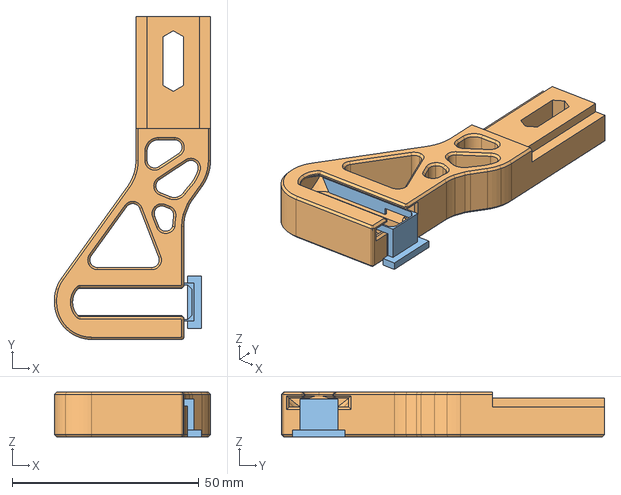
[picture p170: CAD file, 2022-06-27]
CAD/Voron/Gantry_Face_Mount_90dock_Dock.stp
41.8 x 86.5 x 12.0 mm
