nionio6915/Euclid_Probe/stls/Assembly Jigs/EuclidTappingJig2.stl

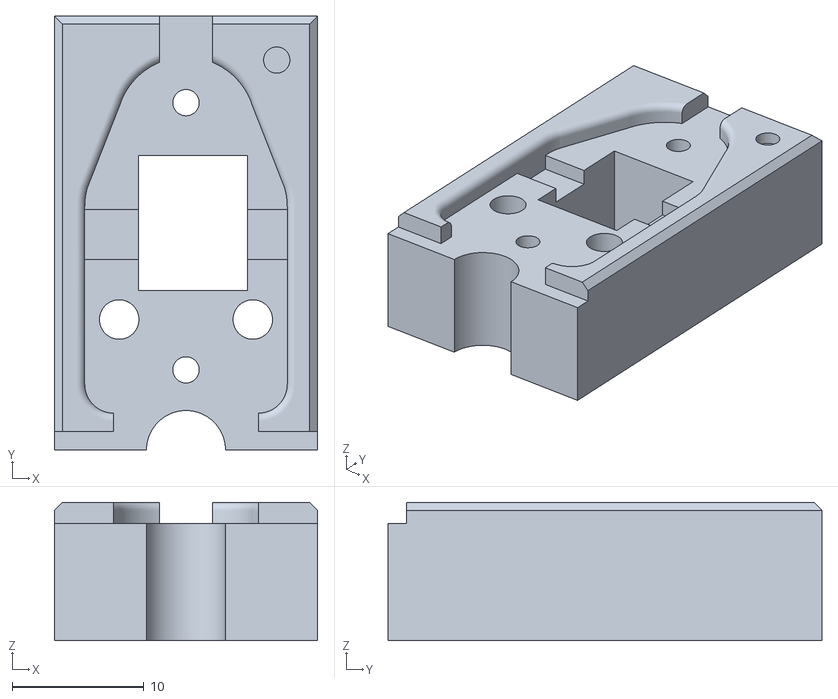
[picture p171: CAD file, 2021-08-17]
stls/Assembly Jigs/EuclidTappingJig2.stl
20.0 x 33.0 x 10.5
