nionio6915/Euclid_Probe/stls/Building Blocks/Modular_Parts_M4.8Holes.stl

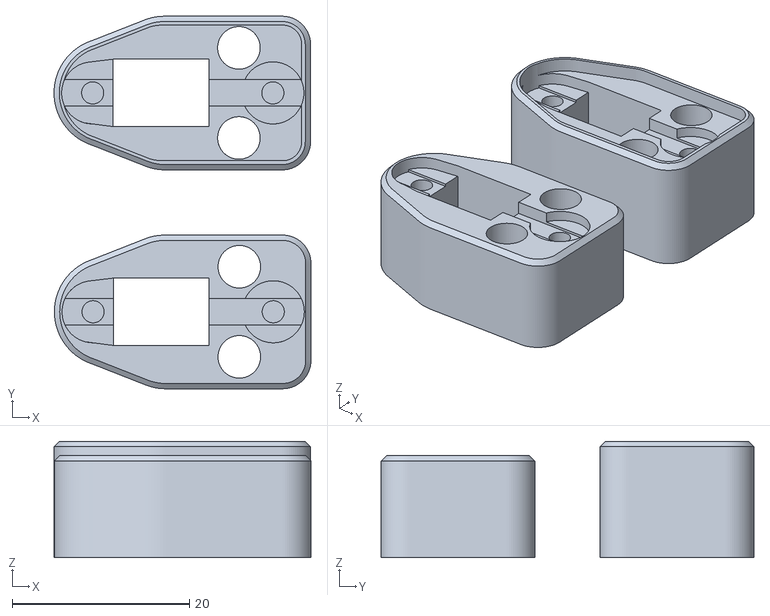
[picture p172: CAD file, 2021-12-06]
stls/Building Blocks/Modular_Parts_M4.8Holes.stl
29.0 x 42.0 x 13.1
