nionio6915/Euclid_Probe/stls/FlashForgeCreator-Qidi/FanDuct6.stl

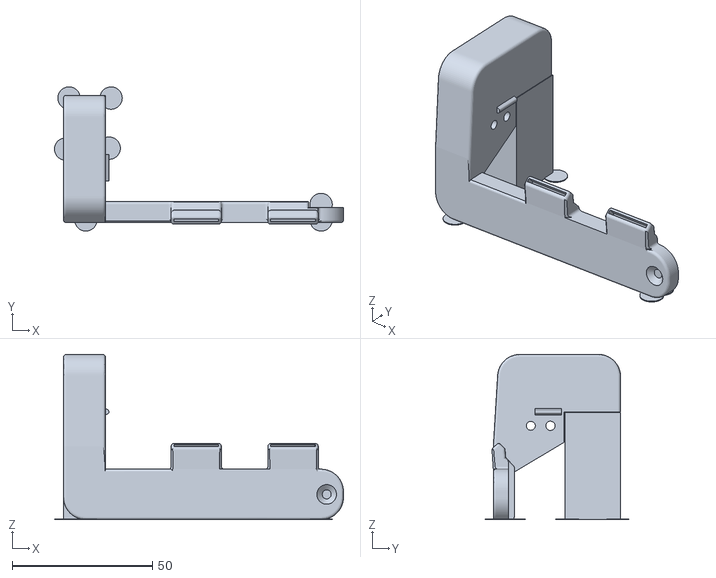
[picture p173: CAD file, 2021-12-10]
stls/FlashForgeCreator-Qidi/FanDuct6.stl
103.2 x 51.5 x 59.0
