nionio6915/Euclid_Probe/CAD/RailCore/RailCoreDockTopMount_DockV3.stp

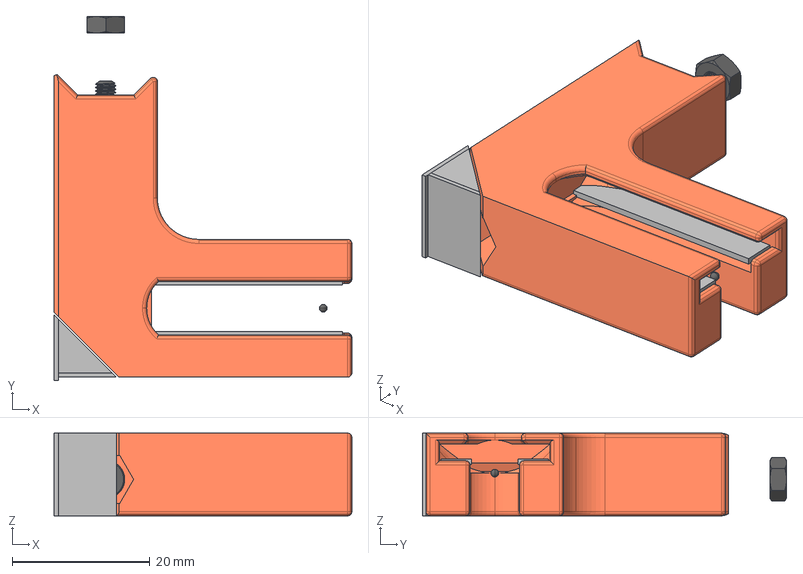
[picture p175: CAD file, 2021-07-21]
CAD/RailCore/RailCoreDockTopMount_DockV3.stp
43.2 x 52.9 x 12.0 mm
