nionio6915/Euclid_Probe/CAD/Voron/VoronGantryMount_MrSnuffleupagus.stp

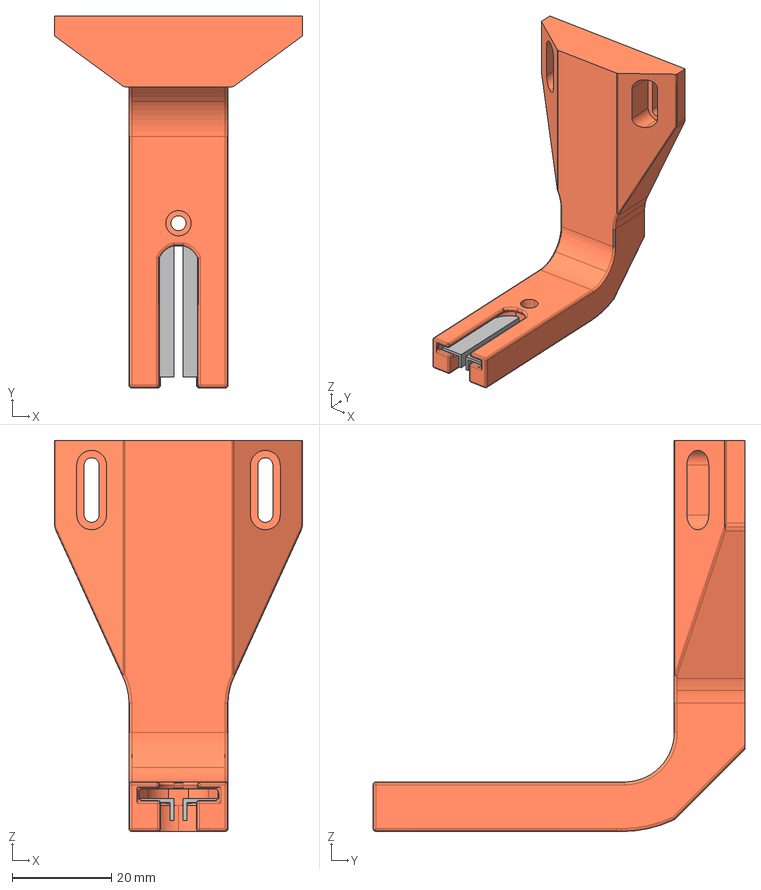
[picture p176: CAD file, 2022-06-27]
CAD/Voron/VoronGantryMount_MrSnuffleupagus.stp
50.0 x 74.9 x 78.8 mm
