nionio6915/Euclid_Probe/stls/FlashForgeCreator-Qidi/DockMount.stl

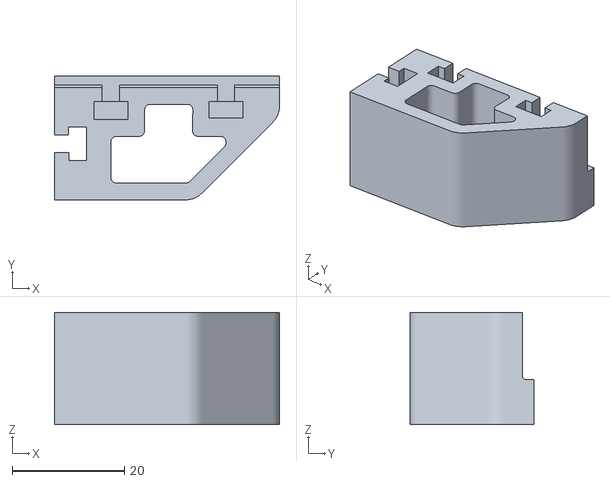
[picture p178: CAD file, 2021-12-10]
stls/FlashForgeCreator-Qidi/DockMount.stl
40.0 x 22.0 x 20.0
