nionio6915/Euclid_Probe/stls/Mount Adapters/Omron/OmronFotekM2_V3.stl

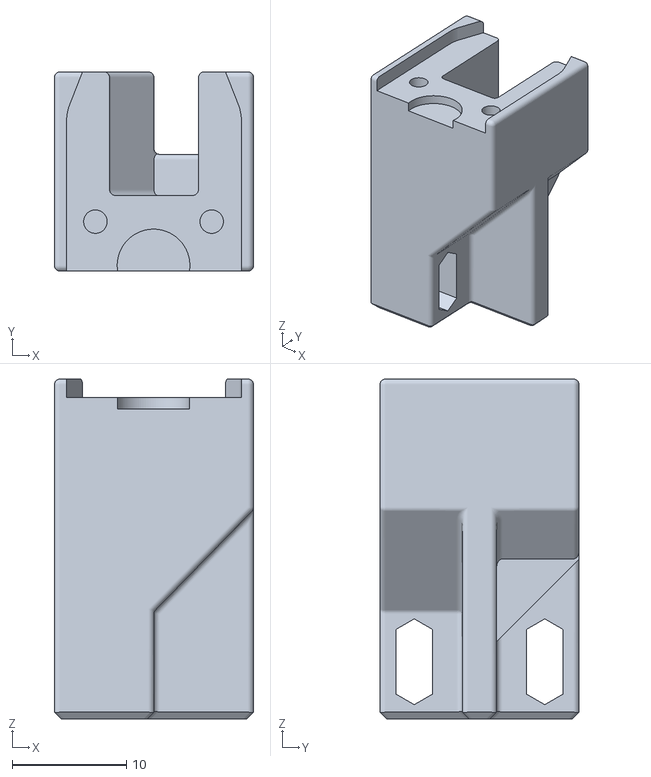
[picture p179: CAD file, 2021-12-12]
stls/Mount Adapters/Omron/OmronFotekM2_V3.stl
17.4 x 17.4 x 29.7
