nionio6915/Euclid_Probe/stls/Voron/Trident_TopMountCloseV1.1Mirrored.stl

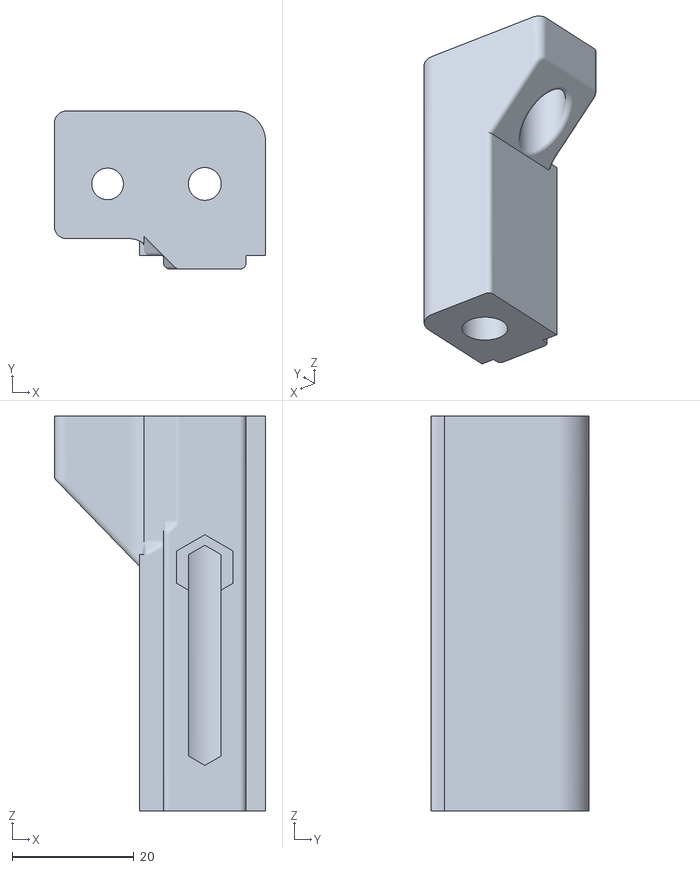
[picture p180: CAD file, 2022-04-05]
stls/Voron/Trident_TopMountCloseV1.1Mirrored.stl
34.7 x 26.0 x 65.0
