nionio6915/Euclid_Probe/CAD/Voron/Gantry_Face_Mount_Straight_Dock.stp

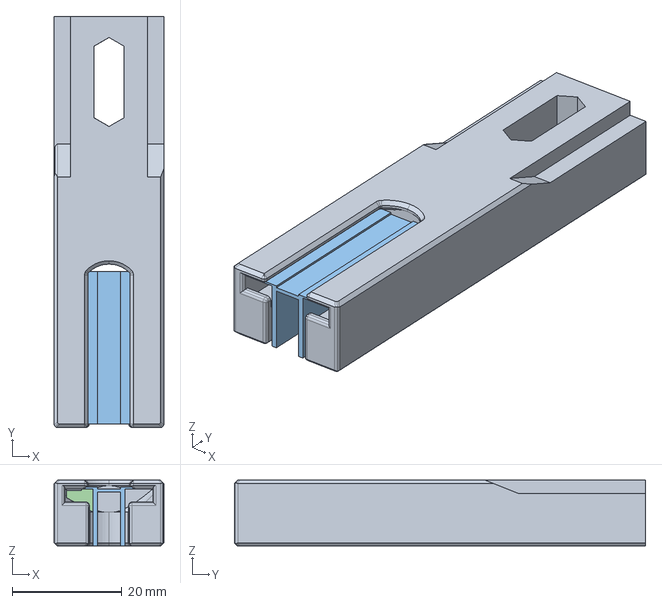
[picture p181: CAD file, 2022-06-27]
CAD/Voron/Gantry_Face_Mount_Straight_Dock.stp
20.0 x 75.0 x 12.0 mm
