nionio6915/Euclid_Probe/stls/Building Blocks/Grafting_MountM2Holes.stl

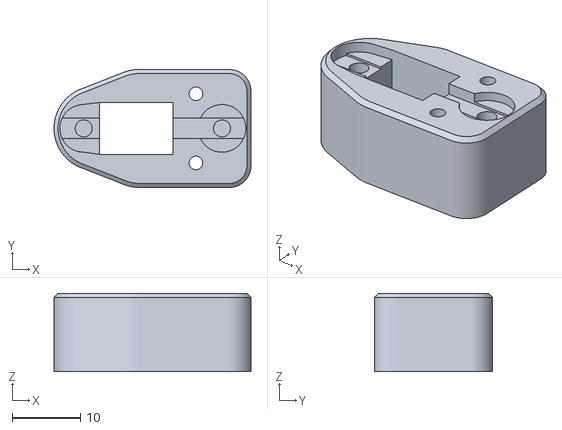
[picture p182: CAD file, 2021-12-06]
stls/Building Blocks/Grafting_MountM2Holes.stl
28.9 x 17.3 x 11.5
