nionio6915/Euclid_Probe/stls/FlashForgeCreator-Qidi/Dock.stl

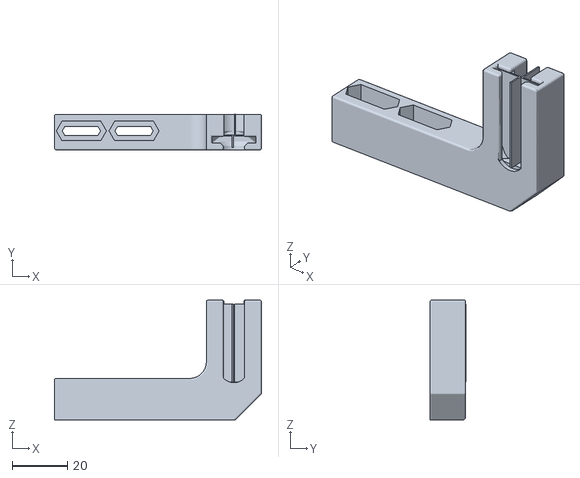
[picture p183: CAD file, 2021-12-10]
stls/FlashForgeCreator-Qidi/Dock.stl
74.7 x 13.0 x 43.2
