nionio6915/Euclid_Probe/stls/Rail Core/RailCoreTopMountShort.stl

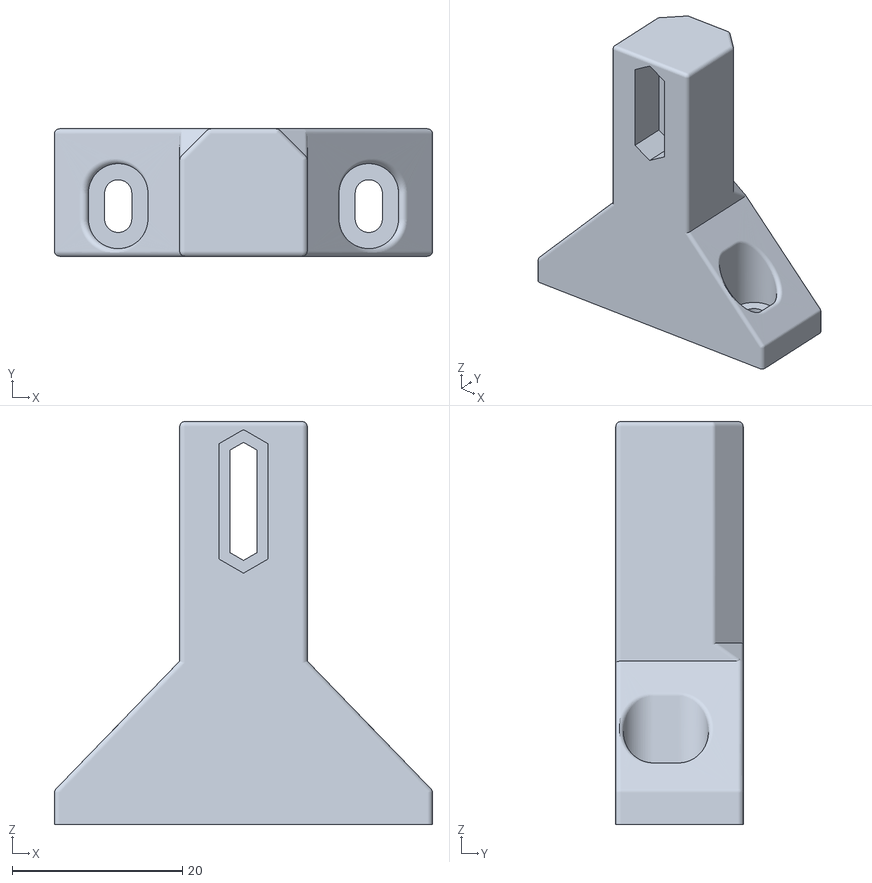
[picture p184: CAD file, 2022-01-09]
stls/Rail Core/RailCoreTopMountShort.stl
44.5 x 15.0 x 47.4
