nionio6915/Euclid_Probe/stls/Voron/Trident_TopMountDockCloseV1.1Mirrored.stl

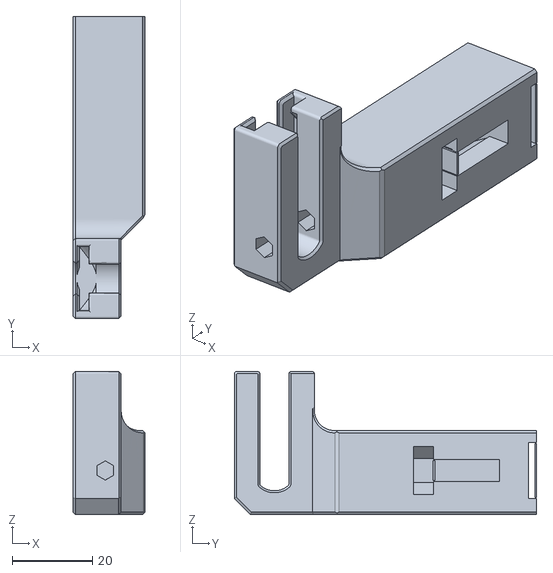
[picture p185: CAD file, 2022-03-31]
stls/Voron/Trident_TopMountDockCloseV1.1Mirrored.stl
18.1 x 75.5 x 35.7
