nionio6915/Euclid_Probe/stls/Building Blocks/GraftingDockSurfaceMtM3Heatserts.stl

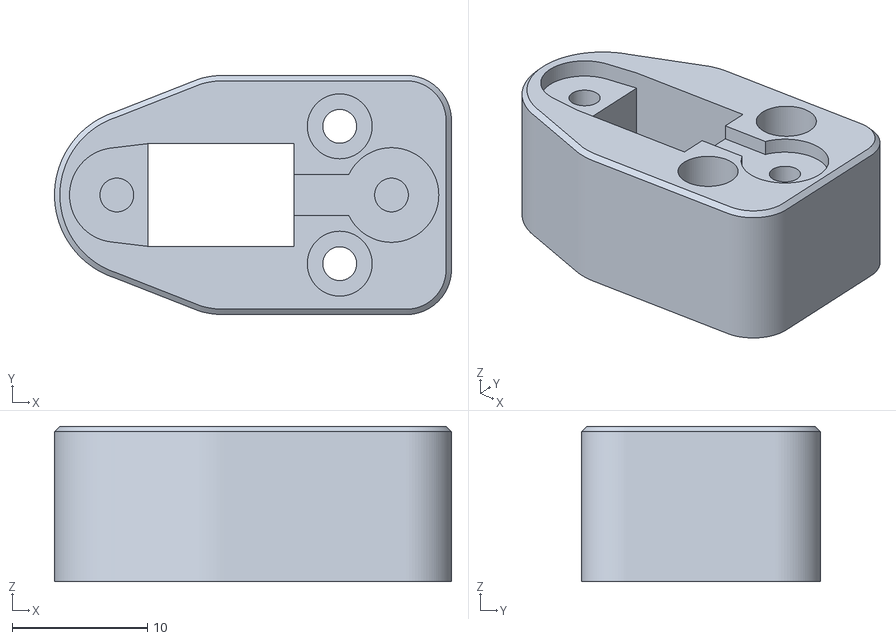
[picture p186: CAD file, 2021-08-17]
stls/Building Blocks/GraftingDockSurfaceMtM3Heatserts.stl
29.4 x 17.7 x 11.5
