nionio6915/Euclid_Probe/stls/FlashForgeCreator-Qidi/DrillingTemplate.stl

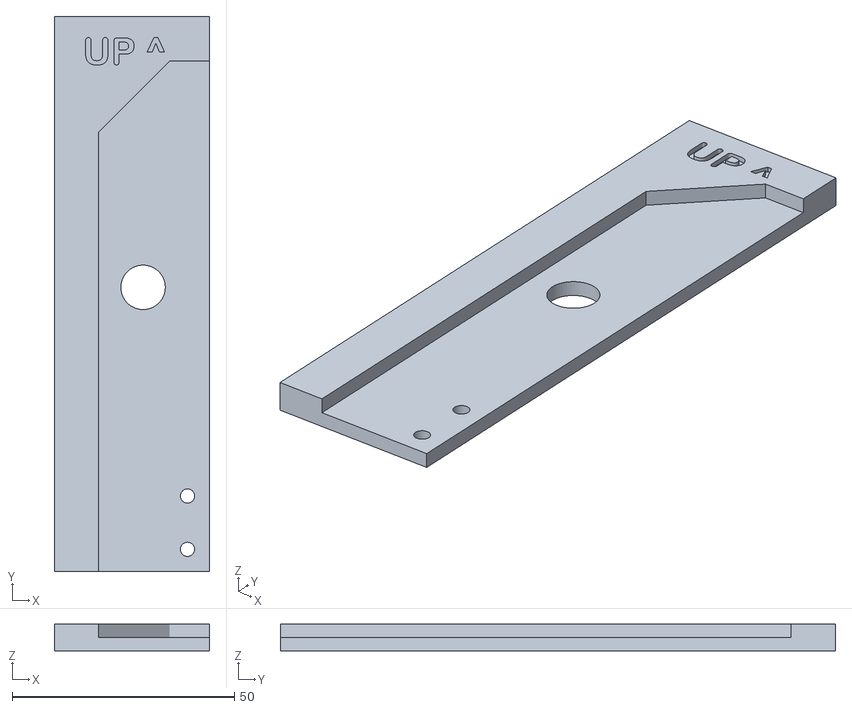
[picture p187: CAD file, 2021-12-10]
stls/FlashForgeCreator-Qidi/DrillingTemplate.stl
35.0 x 125.0 x 6.00
