nionio6915/Euclid_Probe/stls/Rail Core/RC_CornerMountV4.5.stl

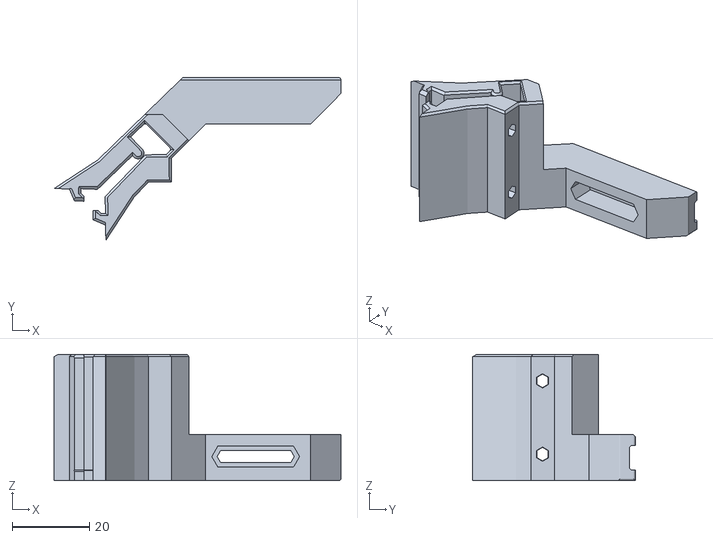
[picture p188: CAD file, 2022-01-09]
stls/Rail Core/RC_CornerMountV4.5.stl
74.4 x 42.2 x 32.7
