nionio6915/Euclid_Probe/stls/Voron/TopMountDockCloseV1.1.stl

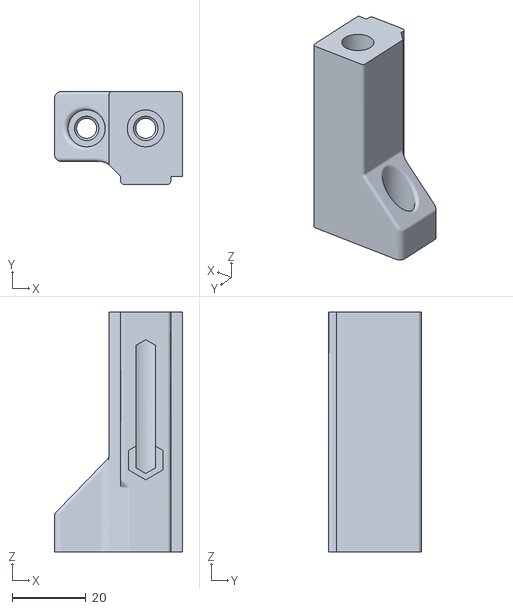
[picture p189: CAD file, 2022-03-30]
stls/Voron/TopMountDockCloseV1.1.stl
34.8 x 25.2 x 65.0
