nionio6915/Euclid_Probe/stls/Building Blocks/GraftingDockFlushM3PilotHoles.stl

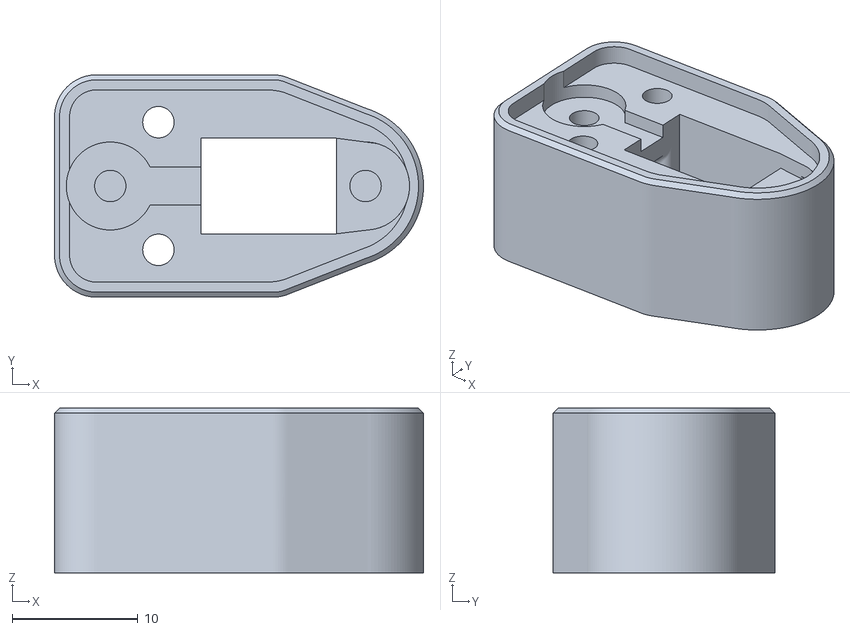
[picture p190: CAD file, 2021-08-17]
stls/Building Blocks/GraftingDockFlushM3PilotHoles.stl
29.4 x 17.7 x 13.1
