nionio6915/Euclid_Probe/CAD/Voron/Gantry_Mount_Short_Adjustable.stp

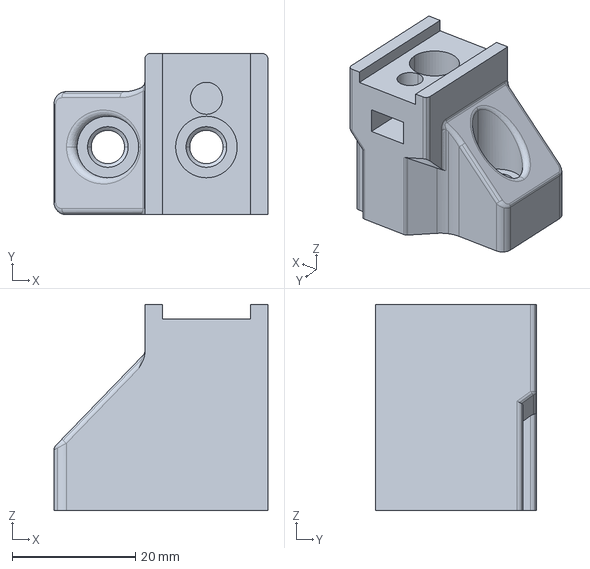
[picture p192: CAD file, 2022-06-27]
CAD/Voron/Gantry_Mount_Short_Adjustable.stp
34.8 x 26.2 x 33.5 mm
