nionio6915/Euclid_Probe/stls/Rail Core/RC_CornerMountV4.5Dock.stl

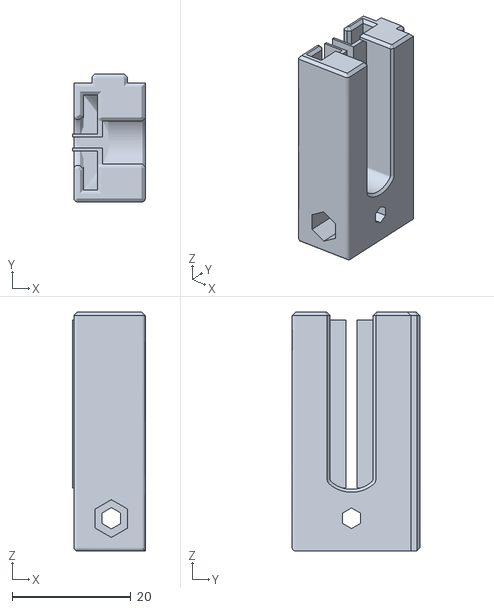
[picture p193: CAD file, 2022-01-09]
stls/Rail Core/RC_CornerMountV4.5Dock.stl
12.2 x 21.5 x 40.2
