nionio6915/Euclid_Probe/stls/Voron/Clockwork1_2XMGN9_Native_Left_M3HtSrt.stl

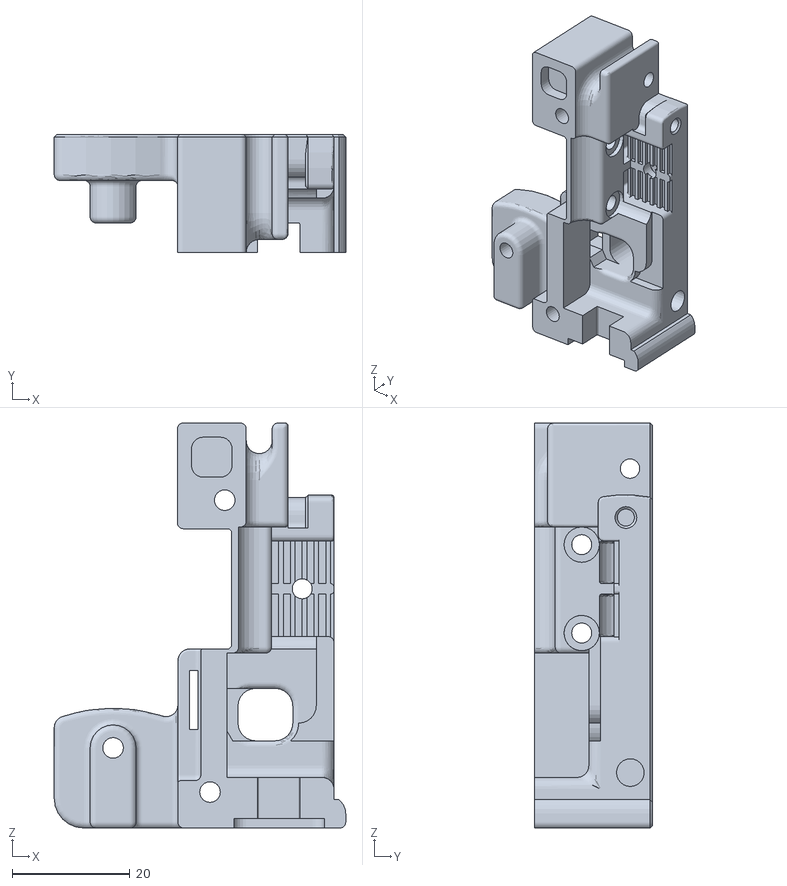
[picture p194: CAD file, 2022-02-17]
stls/Voron/Clockwork1_2XMGN9_Native_Left_M3HtSrt.stl
49.5 x 20.0 x 68.8
