nionio6915/Euclid_Probe/CAD/Voron/VoronGantryMountRev_4_OnePiece.stp

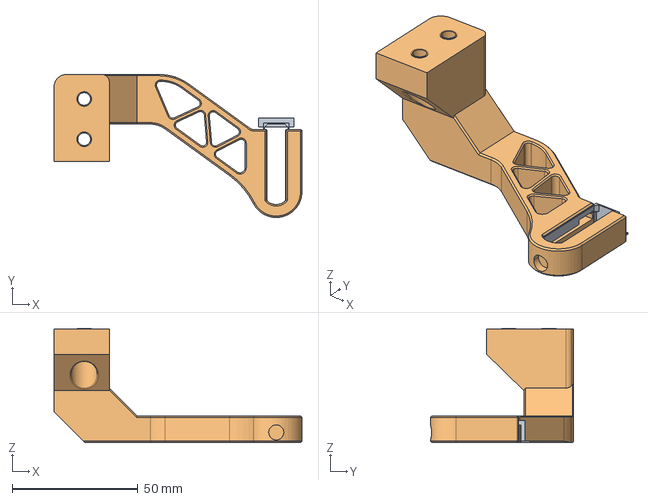
[picture p195: CAD file, 2022-06-27]
CAD/Voron/VoronGantryMountRev_4_OnePiece.stp
98.6 x 56.9 x 45.5 mm
