nionio6915/Euclid_Probe/stls/Rail Core/RailCorePetsfangMountV2.stl

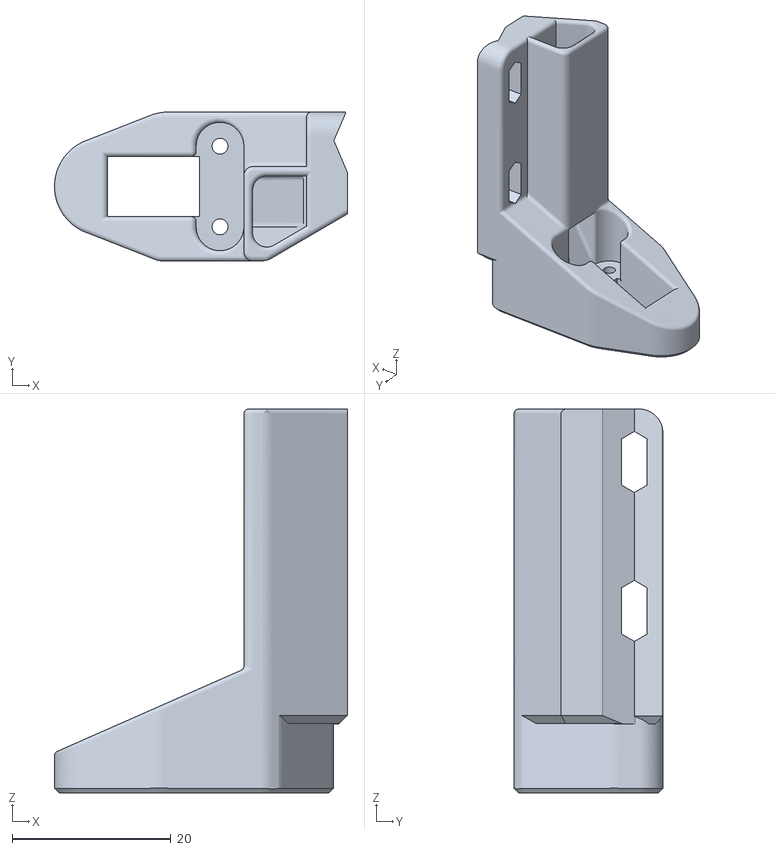
[picture p197: CAD file, 2022-01-09]
stls/Rail Core/RailCorePetsfangMountV2.stl
36.9 x 18.8 x 48.4
