nionio6915/Euclid_Probe/stls/Voron/Clockwork1_MGN12_Right_Strain_ReliefM2.5.stl

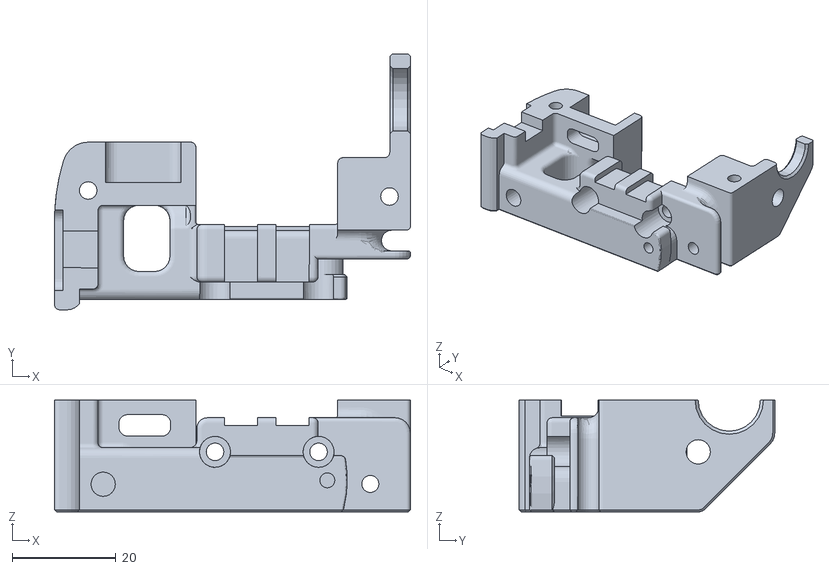
[picture p198: CAD file, 2022-02-17]
stls/Voron/Clockwork1_MGN12_Right_Strain_ReliefM2.5.stl
68.8 x 49.4 x 21.6
