nionio6915/Euclid_Probe/CAD/Voron/Gantry_Mount_Short_CrookArmStraight.stp

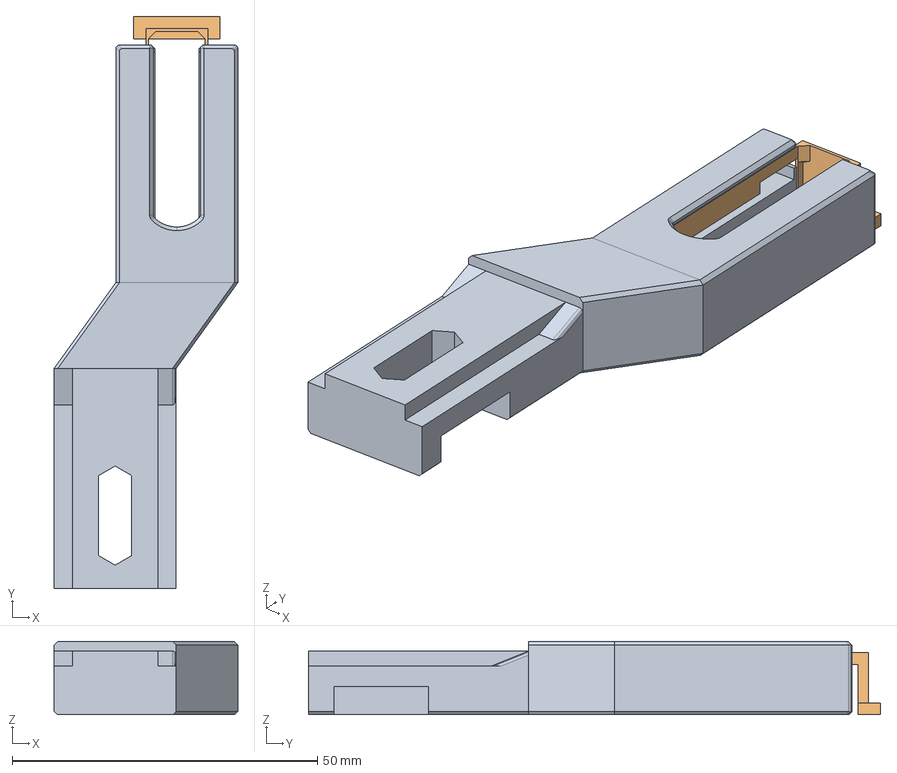
[picture p199: CAD file, 2022-06-27]
CAD/Voron/Gantry_Mount_Short_CrookArmStraight.stp
30.1 x 93.7 x 12.0 mm
