nionio6915/Euclid_Probe/stls/Rail Core/RailCoreTopMountDock.stl

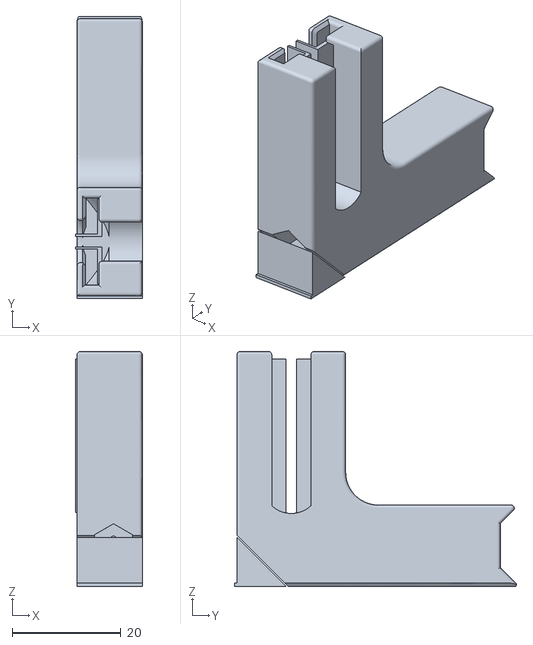
[picture p200: CAD file, 2022-01-09]
stls/Rail Core/RailCoreTopMountDock.stl
12.3 x 52.0 x 43.2
