nionio6915/Euclid_Probe/CAD/Voron/TridentMountV2.stp

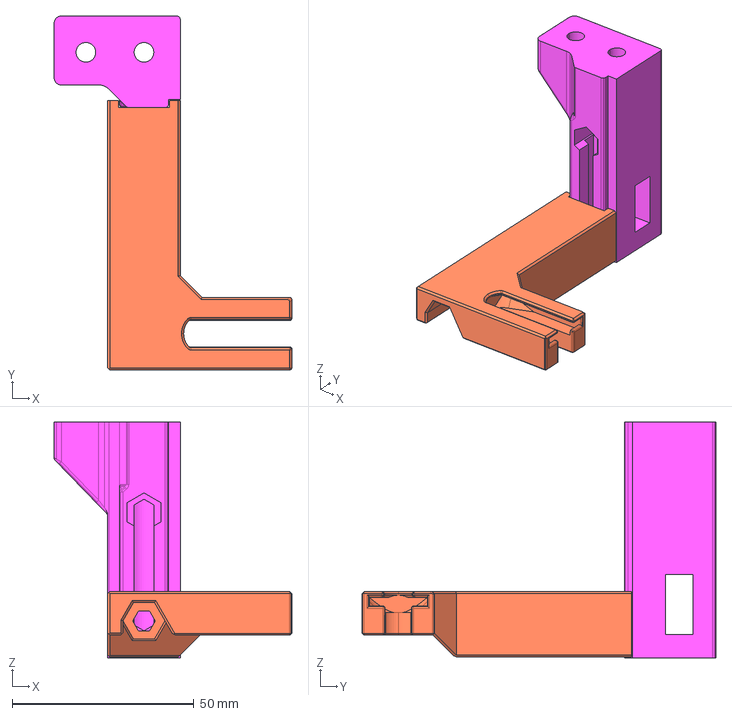
[picture p201: CAD file, 2022-06-27]
CAD/Voron/TridentMountV2.stp
65.5 x 97.5 x 65.0 mm
