nionio6915/Euclid_Probe/stls/Voron/Clockwork1_2XMGN9_Native_Right_CableStrainMod.stl

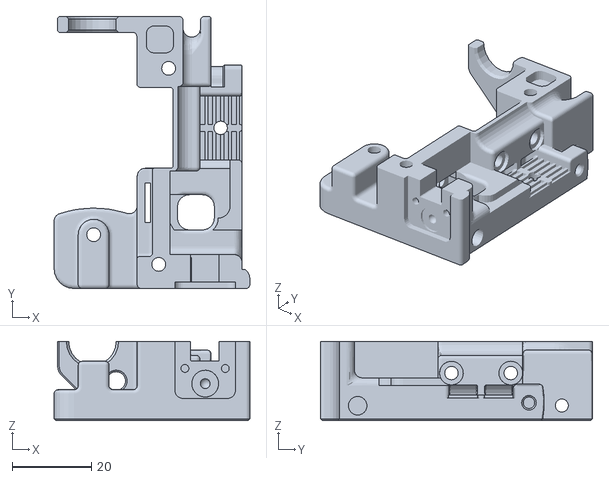
[picture p202: CAD file, 2022-02-17]
stls/Voron/Clockwork1_2XMGN9_Native_Right_CableStrainMod.stl
49.5 x 68.8 x 20.0
