nionio6915/Euclid_Probe/CAD/Voron/CW1_2xMGN9.stp

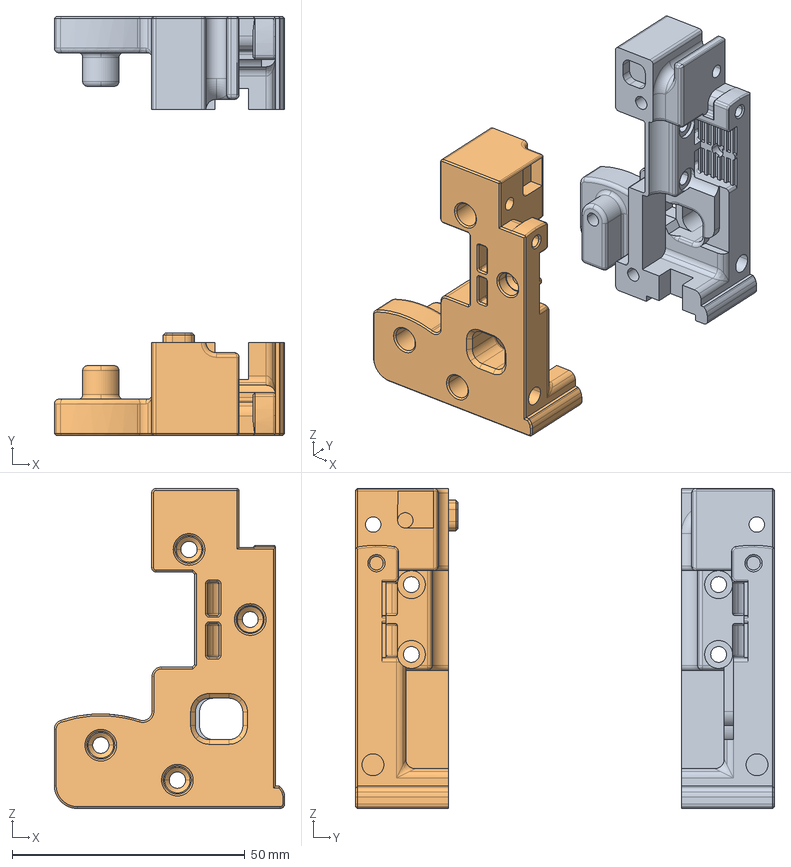
[picture p203: CAD file, 2022-02-07]
CAD/Voron/CW1_2xMGN9.stp
49.5 x 90.0 x 68.8 mm
