nionio6915/Euclid_Probe/stls/Rail Core/RailCoreMountMRW_SD_V3.stl

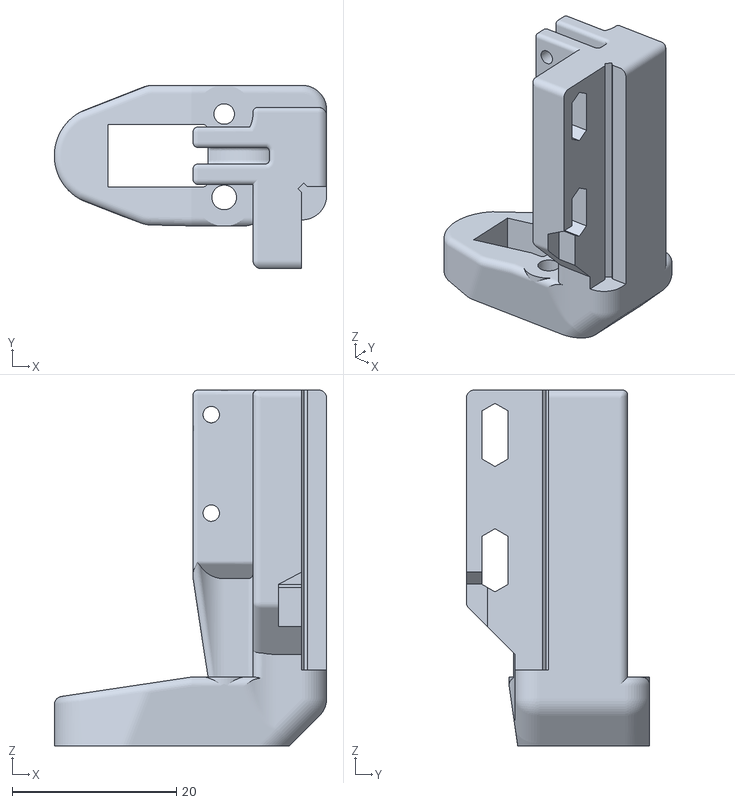
[picture p204: CAD file, 2021-12-06]
stls/Rail Core/RailCoreMountMRW_SD_V3.stl
33.2 x 22.3 x 43.4
