nionio6915/Euclid_Probe/Firmware_Examples/Duet/DeploySteps.png

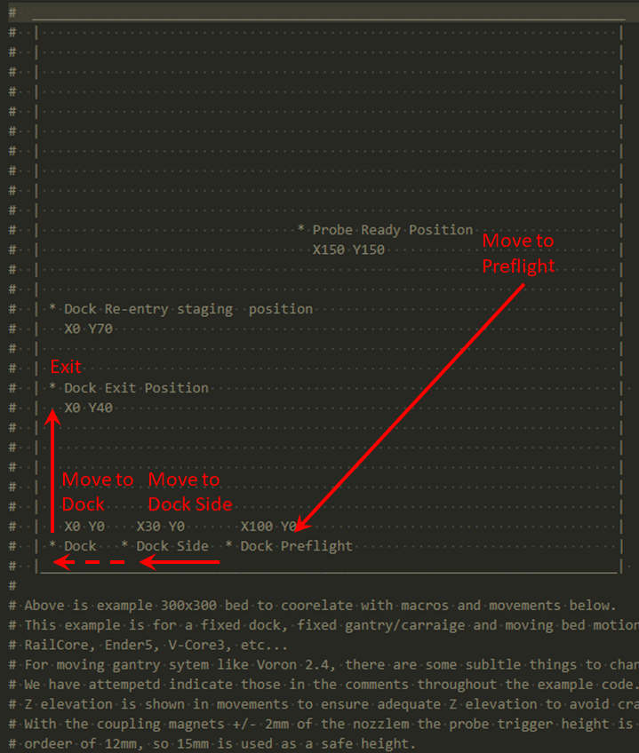
Firmware_Examples/Duet/DeploySteps.png
