nionio6915/Euclid_Probe/Firmware_Examples/Duet/Retract Steps.png

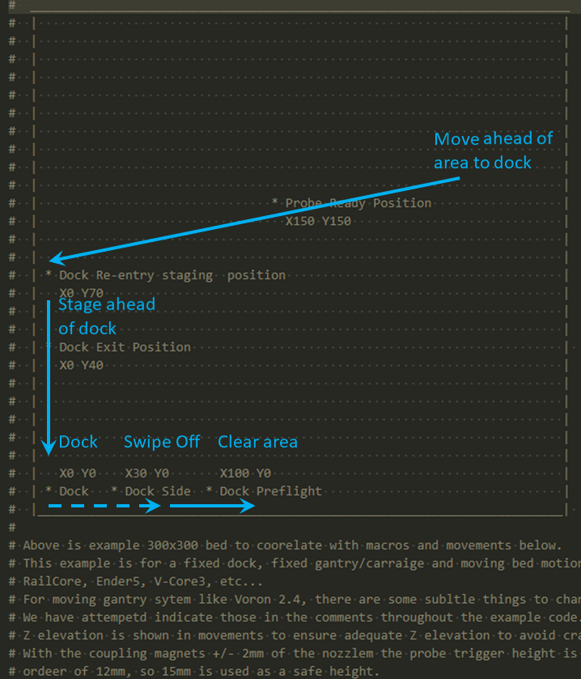
Firmware_Examples/Duet/Retract Steps.png
