nionio6915/Euclid_Probe/images/SolderMaskTop.png

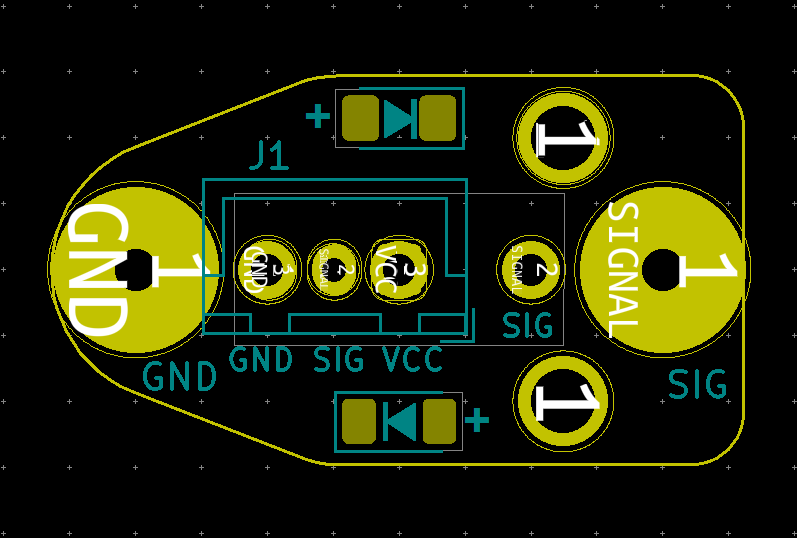
images/SolderMaskTop.png
