nionio6915/Euclid_Probe/stls/Assembly Jigs/1515_Drilling_Jig.png

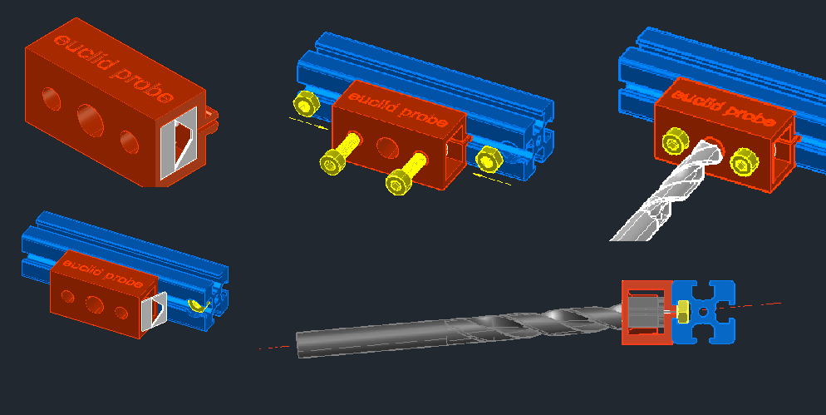
stls/Assembly Jigs/1515_Drilling_Jig.png
