nionio6915/Euclid_Probe/stls/Assembly Jigs/Guide_Block-1-300x166.jpg

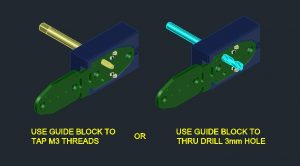
stls/Assembly Jigs/Guide_Block-1-300x166.jpg
