nionio6915/Euclid_Probe/stls/Building Blocks/GraftingDockFlush-256x300.jpg

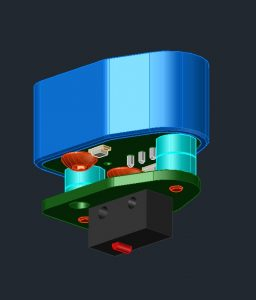
stls/Building Blocks/GraftingDockFlush-256x300.jpg
