nionio6915/Euclid_Probe/stls/Building Blocks/GraftingDockSurface.jpg

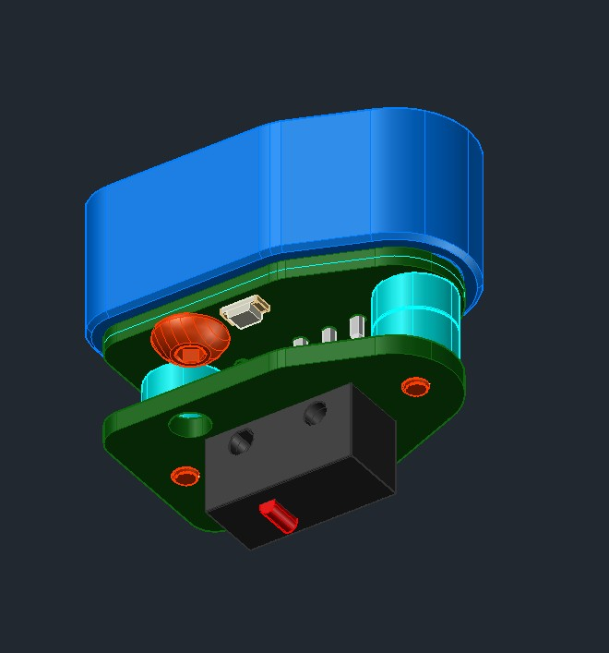
stls/Building Blocks/GraftingDockSurface.jpg
