nionio6915/Euclid_Probe/Firmware_Examples/Klipper/user_contrib/railcore/RailCore_JohnOCFII_printer-22October2021.cfg

# Klipper config for RailCore 300ZL with Duet2 and Duex5 - osh - 22 October 2021

# This file contains common pin mappings for Duet2 Eth/Wifi boards
# that have the Duex expansion board. To use this config, the firmware
# should be compiled for the SAM4E8E.

# See docs/Config_Reference.md for a description of parameters.

## Drivers
# Here are the pins for the 10 stepper drivers supported by a Duet2 board
# | Drive |  DIR pin |  STEP pin |  ENDSTOP pin |  SPI EN pin |
# |-------|----------|-----------|--------------|-------------|
# | X     |  PD11    |  PD6      |  PC14        |  PD14       |
# | Y     |  PD12    |  PD7      |  PA2         |  PC9        |
# | Z     |  PD13    |  PD8      |  PD29        |  PC10       |
# | E0    |  PA1     |  PD5      |  PD10        |  PC17       |
# | E1    |  PD9     |  PD4      |  PC16        |  PC25       |
# | E2    |  PD28    |  PD2      |  PE0*        |  PD23       |
# | E3    |  PD22    |  PD1      |  PE1*        |  PD24       |
# | E4    |  PD16    |  PD0      |  PE2*        |  PD25       |
# | E5    |  PD17    |  PD3      |  PE3*        |  PD26       |
# | E6    |  PC0     |  PD27     |  PA17*       |  PB14       |
# Pins marked with asterisks (*) are only assigned to these functions
# if no duex is connected. If a duex is connected, these endstops are
# remapped to the SX1509 on the Duex (unfortunately they can't be used
# as endstops in klipper, however one may use them as digital outs or
# PWM outs). The SPI EN pins are required for the TMC2660 drivers (use
# the SPI EN pin as 'cs_pin' in the respective config block). The
# **enable pin for all steppers** is TMC_EN = !PC6.
#
## Fans
# | FAN  |          PIN          |
# |------|-----------------------|
# | FAN0 |  PC23                 |
# | FAN1 |  PC26                 |
# | FAN2 |  PA0                  |
# | FAN3 |  sx1509_duex:PIN_12*  |
# | FAN4 |  sx1509_duex:PIN_7*   |
# | FAN5 |  sx1509_duex:PIN_6*   |
# | FAN6 |  sx1509_duex:PIN_5*   |
# | FAN7 |  sx1509_duex:PIN_4*   |
# | FAN8 |  sx1509_duex:PIN_15*  |
# Pins marked with (*) assume the following sx1509 config section:
# [sx1509 duex]
# i2c_address: 62
#
## Heaters and Thermistors
# | Extruder Drive |  HEAT pin |  TEMP pin |
# |----------------|-----------|-----------|
# | BED            |  PA19     |  PC13     |
# | E0             |  PA20     |  PC15     |
# | E1             |  PA16     |  PC12     |
# | E2             |  PC3      |  PC29     |
# | E3             |  PC5      |  PC30     |
# | E4             |  PC8      |  PC31     |
# | E5             |  PC11     |  PC27     |
# | E6             |  PA15     |  PA18     |
#
## Misc pins
# |    Name     |   Pin   |
# |-------------|---------|
# | ZProbe_IN   |  PC1    |
# | PS_ON       |  PD15   |
# | LED_ONBOARD |  PC2    |
# | SPI0_CS0    |  PC24   |
# | SPI0_CS1    |  PB2    |
# | SPI0_CS2    |  PC18   |
# | SPI0_CS3    |  PC19   |
# | SPI0_CS4    |  PC20   |
# | SPI0_CS5    |  PA24   |
# | SPI0_CS6    |  PE1*   |
# | SPI0_CS7    |  PE2*   |
# | SPI0_CS8    |  PE3*   |
# | SX1509_IRQ  |  PA17*  |
# | SG_TST      |  PE0*   |
# | ENC_SW      |  PA7    |
# | ENC_A       |  PA8    |
# | ENC_B       |  PC7    |
# | LCD_DB7     |  PD18   |
# | LCD_DB6     |  PD19   |
# | LCD_DB5     |  PD20   |
# | LCD_DB4     |  PD21   |
# | LCD_RS      |  PC28   |
# | LCD_E       |  PA25   |
# Pins marked with one asterisk (*) replace E2_STOP-E6_STOP if a duex is present
# For the remaining pins check the schematics provided here: https://github.com/T3P3/Duet
# https://duet3d.dozuki.com/Wiki/Duet_2_Pinout_table

[virtual_sdcard]
path: ~/gcode_files

[pause_resume]

[display_status]

###########
#   MCU   #
###########

[mcu]

serial: /dev/serial/by-id/usb-Klipper_sam4e8e_00313753595252533136303230303132-if00

[sx1509 duex]
i2c_address: 62 # Address is fixed on duex boards

# what is this for?  Do I need this?  check
#[static_digital_output onboard_led]
#pins: !PC2

[mcu rpi]
serial: /tmp/klipper_host_mcu

[adxl345]
cs_pin: rpi:None

[resonance_tester]
accel_chip: adxl345
probe_points:
    150,150,20


###############
#   Printer   #
###############

[printer]
kinematics: corexy
max_velocity: 500  
max_accel: 3600              # Tested 21 June 2021		     		
max_z_velocity: 16 			 #Max 15 for 12V TMC Drivers, can increase for 24V
max_z_accel: 200   			 #Max ?
square_corner_velocity: 5.0  #Can experiment with 8.0, default 5.0

[idle_timeout]
timeout: 600

####################
#   X/Y Steppers   #
####################

#___ X ___#
[stepper_x]
step_pin: PD6
dir_pin: PD11
enable_pin: !PC6

# 16T Pulley / 0.9 stepper motor
microsteps: 16
rotation_distance: 32
full_steps_per_rotation: 400

# Axis limits and homing
endstop_pin: ^PC14
position_endstop: 0
position_max: 300
homing_speed: 50.0
homing_retract_dist: 5.0

[tmc2660 stepper_x]
cs_pin: PD14 				# X_SPI_EN Required for communication
spi_bus: usart1 			# All TMC2660 drivers are connected to USART1
interpolate: True 			# 1/16 micro-steps interpolated to 1/256
run_current: 0.850
sense_resistor: 0.051
idle_current_percent: 25

#___ Y ___#
[stepper_y]
step_pin: PD7
dir_pin: !PD12
enable_pin: !PC6

# 16T Pulley / 0.9 stepper motor
microsteps: 16
rotation_distance: 32
full_steps_per_rotation: 400

# Axis limits and homing
endstop_pin: ^PA2
position_endstop: 0
position_max: 306
homing_speed: 50.0
homing_retract_dist: 5.0

[tmc2660 stepper_y]
cs_pin: PC9
spi_bus: usart1
interpolate: True
run_current: 0.850
sense_resistor: 0.051
idle_current_percent: 25

##################
#   Z Steppers   #
##################

#___ Z (E2) left/right front/rear___#
[stepper_z]
step_pin: PD2
dir_pin: !PD28
enable_pin: !PC6

# T8x4 Leadscrew / 0.9 stepper motor
# step_distance: 0.0003125 (for TR8x2)
# step distance: 0.00015625 (?)
microsteps: 16
rotation_distance: 4 				
full_steps_per_rotation: 400

# Why is there here in the middle of 3 Z stepper configs?

endstop_pin: probe:z_virtual_endstop
##  Z-position of nozzle (in mm) to z-endstop trigger point relative to print surface (Z0)
##  (+) value = endstop above Z0, (-) value = endstop below
##	Increasing position_endstop brings nozzle closer to the bed
##  After you run Z_ENDSTOP_CALIBRATE, position_endstop will be stored at the very end of your config

position_max: 320
position_min: -5
homing_speed: 5.0
homing_retract_dist: 3.0

[tmc2660 stepper_z]
cs_pin: PD23
spi_bus: usart1
interpolate: True
run_current: 0.850
sense_resistor: 0.051
idle_current_percent: 25

#___ Z (E3) ___#
[stepper_z1]
step_pin: PD1
dir_pin: !PD22
enable_pin: !PC6

# T8x4 Leadscrew / 0.9 stepper motor
# step_distance: 0.0003125 (for TR8x2)
# step distance: 0.00015625 (?)
microsteps: 16
rotation_distance: 4 				
full_steps_per_rotation: 400

[tmc2660 stepper_z1]
cs_pin: PD24
spi_bus: usart1
interpolate: True
run_current: 0.850
sense_resistor: 0.051
idle_current_percent: 25

#___ Z (E4) ___#
[stepper_z2]
step_pin: PD0
dir_pin: !PD16
enable_pin: !PC6

# T8x4 Leadscrew / 0.9 stepper motor
# step_distance: 0.0003125 (for TR8x2)
# step distance: 0.00015625 (?)
microsteps: 16
rotation_distance: 4 				
full_steps_per_rotation: 400

[tmc2660 stepper_z2]
cs_pin: PD25
spi_bus: usart1
interpolate: True
run_current: 0.850
sense_resistor: 0.051
idle_current_percent: 25

################
#   Extruder   #
################

#___ E0 ___#
[extruder]
step_pin: PD5
dir_pin: PA1
enable_pin: !PC6
heater_pin: !PA20

# Bondtech BMG / 0.9 stepper motor
rotation_distance: 7.7108433728
microsteps: 16
full_steps_per_rotation: 400

nozzle_diameter: 0.400
filament_diameter: 1.75

# Hotend thermistor (check)
sensor_type: ATC Semitec 104GT-2
sensor_pin: PC15

# Run PID_CALIBRATE HEATER=extruder TARGET=XXX to calibrate

# Temperature limits
min_temp: 10
max_temp: 350
max_power: 1.0
min_extrude_temp: 170
max_extrude_only_distance: 250.0

# Pressure advance

pressure_advance: 0.0730             # 3D-Fuel Workday PLA 21 June2021
pressure_advance_smooth_time: 0.040

[tmc2660 extruder]
cs_pin: PC17
spi_bus: usart1
interpolate: True
run_current: 0.610
sense_resistor: 0.051

[verify_heater extruder]
check_gain_time: 30
hysteresis: 5
max_error: 180

################
#   Bed Heat   #
################

##	SSR connected to bed header
[heater_bed]
heater_pin: !PA19
sensor_type: NTC 100K beta 3950
sensor_pin: PC13
max_power: 1
min_temp: 0
max_temp: 120

# Run PID_CALIBRATE HEATER=heater_bed TARGET=XX to calibrate

############
#   Fans   #
############

# Hotend Fan
# Connected to Fan yy header
[heater_fan hotend_fan]
pin: PC26
max_power: 1.0
kick_start_time: 0.3
heater: extruder
heater_temp: 45
fan_speed: 1.0

# Part Cooling Fan 
# Connected to Fan xx header
[fan]
pin: PC23
max_power: 1.0
kick_start_time: 0.3
off_below: 0.05

###################################
#   Probes / Sensors / Switches   #
###################################

#___ Euclid Probe ___#
[probe]
pin: ^PC1
x_offset: -1
y_offset: 35
#z_offset: 0
# Run PROBE_CALIBRATE to calibrate Z offset
speed: 5
samples: 3
samples_result: average
sample_retract_dist: 5.0
samples_tolerance: 0.050
samples_tolerance_retries: 3
lift_speed: 30

#___ LED Lights - left ___#
[output_pin led-l]
pin: sx1509_duex:PIN_15
pwm: True 
value: 0.25
hardware_pwm: True

#___ LED Lights - right ___#
[output_pin led-r]
pin: sx1509_duex:PIN_4
pwm: True 
value: 0.15
hardware_pwm: True

#___ Keenevo Thermistor ___#
[temperature_sensor keenovo_temp]
sensor_type: NTC 100K beta 3950
sensor_pin: PA18
min_temp: 0
max_temp: 150
gcode_id: K

#___ Board temp sensors ___#
[temperature_sensor raspberry_pi]
sensor_type: temperature_host
min_temp: 10
max_temp: 100

[temperature_sensor mcu_temp]
sensor_type: temperature_mcu
min_temp: 0
max_temp: 100

#___ Filament Sensor ___#
[filament_motion_sensor fe_sensor]
detection_length: 6.0
#   The minimum length of filament pulled through the sensor to trigger
#   a state change on the switch_pin
#   Default is 7 mm.
extruder: extruder
#   The name of the extruder section this sensor is associated with.
#   This parameter must be provided.
switch_pin: ^PC16
pause_on_runout: True
runout_gcode:
 {action_respond_info("Filament Sensor reports FILAMENT OUT")}
 PAUSE
#insert_gcode:
#event_delay:
#pause_delay:
#   See the "filament_switch_sensor" section for a description of the
#   above parameters.

#############################
#   Homing and Z-leveling   #
#############################

# Disable HE heater during probe to avoid interference with BLT
[homing_heaters]
steppers: stepper_z
heaters: extruder

## Mutually exclusive with homing_override
# [safe_z_home]
# home_xy_position: 150,150 
# speed: 100
# z_hop: 5                 
# z_hop_speed: 4

[homing_override]
gcode:
    G28 X
    G28 Y
    M401                   # deploy probe
    G1 X150 Y150 F4000
    M400
    G28 Z
    M400
    G1 Z10                 # fails without this G1 command here -- don't know why... 24 July 2021
    M402                   # retract probe    
axes: z 
set_position_z: 00

[bed_mesh]
speed: 250
mesh_min: 2,36
mesh_max: 299,299
probe_count: 6,6

[z_tilt]
# Position of bed pivot points - Measure at bed retaining bolts

z_positions:
    -11,20
    -11,274
    347,148

points:
# Three point (probe location)
    17, 2        # was 15, 20 -- and can't go too far forward as a negative would hit X carriage)
    17, 230   
    298, 112 

retries: 4
retry_tolerance: 0.008 
speed: 100             #   The speed (in mm/s) of non-probing moves during the calibration.
horizontal_move_z: 5   #   The height (in mm) that the head should be commanded to move to just prior to starting a probe operation.

####################
#   Input Shaping  #
####################

[input_shaper]
shaper_type_x = 2hump_ei
shaper_freq_x = 80.8

shaper_type_y = 2hump_ei
shaper_freq_y = 91.8


######################
#   Skew Correction  #
######################

[skew_correction]


##############################################################################
#   Macros  #                                                    #   Macros  #
##############################################################################

[gcode_macro PROBE]
rename_existing:    PROBE_ORIGINAL
gcode:
    M401
    G1 X150 Y150 F4000
    PROBE_ORIGINAL
    G1 Z8
    M402
    
[gcode_macro PROBE_ACCURACY]
rename_existing:    PROBE_ACCURACY_ORIGINAL
gcode:
    M401
    G1 X150 Y150 F4000
    PROBE_ACCURACY_ORIGINAL
    G1 Z8
    M402

[gcode_macro PROBE_CALIBRATE]
rename_existing:    PROBE_CALIBRATE_ORIGINAL
gcode:
    M401
    G1 X150 Y150 F4000
    PROBE_CALIBRATE_ORIGINAL
    G1 Z8
    M402

[gcode_macro Z_TILT_ADJUST]
rename_existing:    Z_TILT_ADJUST_ORIGINAL
gcode:
    M401
    Z_TILT_ADJUST_ORIGINAL
    M402


[gcode_macro G32]
gcode:
    Z_TILT_ADJUST

[gcode_macro BED_MESH_CALIBRATE]
rename_existing:    BED_MESH_CALIBRATE_ORIGINAL
gcode:
    M401
    BED_MESH_CALIBRATE_ORIGINAL
    M402

[gcode_macro G29]
gcode:
    BED_MESH_CALIBRATE

[gcode_macro GO_HOME]
gcode:    
    G91
    G1 Z5
    G90
    G1 X1 Y1
    G91
    G1 Z-5
    G90
    
[gcode_macro GO_CENTER]
gcode:    
    G91
    G1 Z5
    G90
    G1 X150 Y150
    G91
    G1 Z-5
    G90
    
[gcode_macro GO_PARK]
gcode:    
    G91
    G1 Z5
    G90
    G1 X298 Y298 F8000 ; park at limits
    G91
    G1 Z-5
    G90

[gcode_macro START_PRINT]
gcode:
    {% set BED_TEMP = params.BED_TEMP|default(60)|float %}
    {% set EXTRUDER_TEMP = params.EXTRUDER_TEMP|default(210)|float %}
    # Start bed heating
    M140 S{BED_TEMP}
    # Use absolute coordinates
    G90
    # Reset the G-Code Z offset (adjust Z offset if needed)
    SET_GCODE_OFFSET Z=0.0
    # Home the printer
    G28
    error_if_probe_deployed        ; If probe is currently deployed, error
    # Wait for bed to reach temperature
    M190 S{BED_TEMP}
    # Tram the bed
    G32
    BED_MESH_PROFILE LOAD=default       # Load default bed mesh
    # Move bed down 10
    G1 Z10 F600
    # Set and wait for nozzle to reach temperature
    M109 S{EXTRUDER_TEMP}
    # prepare to prime
    G1 X0.2 Y0.2 Z1.0 F2000.0
    # reset extrusion distance  
    G92 E0
    G1 Z0.2 F600
    # prime in two steps
    G1 X60.0 E9.0  F1000.0
    G1 X125.0 E12.5  F1000.0
    G1 Z0.5 F600
    # reset extrusion distance  
    G92 E0
    # Activate skew correction
    SKEW_PROFILE LOAD=my_skew_profile
    # End of Start macro

[gcode_macro END_PRINT]
gcode:
    M400         ; Wait for buffer to clear
    # De-activate skew correction
    SET_SKEW CLEAR=1
    # Turn off bed, extruder, and fan
    M140 S0
    M104 S0
    M106 S0
    # Move nozzle away from print while retracting
    G91
    G1 X-2 Y-2 E-3 F300
    # Raise nozzle by 10mm
    G1 Z10 F3000
    # absolute moves
    G90
    # Move Y-carriage for part removal
    G1 X10 Y280 F2000
    # Disable steppers
    M84

[gcode_macro CANCEL_PRINT]
rename_existing: BASE_CANCEL_PRINT
gcode:
  TURN_OFF_HEATERS
  CLEAR_PAUSE
  SDCARD_RESET_FILE
  BASE_CANCEL_PRINT

[gcode_macro PAUSE]
rename_existing: BASE_PAUSE
# change this if you need more or less extrusion
variable_extrude: 1.0
gcode:
  ##### read E from pause macro #####
  {% set E = printer["gcode_macro PAUSE"].extrude|float %}
  ##### set park positon for x and y #####
  # default is your max posion from your printer.cfg
  {% set x_park = printer.toolhead.axis_maximum.x|float - 5.0 %}
  {% set y_park = printer.toolhead.axis_maximum.y|float - 5.0 %}
  ##### calculate save lift position #####
  {% set max_z = printer.toolhead.axis_maximum.z|float %}
  {% set act_z = printer.toolhead.position.z|float %}
  {% if act_z < (max_z - 2.0) %}
      {% set z_safe = 2.0 %}
  {% else %}
      {% set z_safe = max_z - act_z %}
  {% endif %}
  ##### end of definitions #####
  SAVE_GCODE_STATE NAME=PAUSE_state
  BASE_PAUSE
  G91
  G1 E-{E} F2100
  G1 Z{z_safe} F900
  G90
  G1 X{x_park} Y{y_park} F6000

[gcode_macro RESUME]
rename_existing: BASE_RESUME
gcode:
  ##### read E from pause macro #####
  {% set E = printer["gcode_macro PAUSE"].extrude|float %}
  ##### end of definitions #####
  G91
  G1 E{E} F2100
  RESTORE_GCODE_STATE NAME=PAUSE_state
  BASE_RESUME

[gcode_macro Z_UP_TENTH]
gcode:
    error_if_probe_deployed
    TESTZ Z=-.1

[gcode_macro Z_DOWN_TENTH]
gcode:
    error_if_probe_deployed
    TESTZ Z=-.1

[gcode_macro Z_DOWN_HUNDREDTH]
gcode:
    error_if_probe_deployed
    TESTZ Z=-.01

[gcode_macro Z_SAVE_CALIBRATION]
gcode:
    ACCEPT
    SAVE_CONFIG

# actually check if probe is deplyed and error out.  Needs to be called by routine which does QUERY_PROBE due to the way klipper does expansion of macros
[gcode_macro do_error_if_probe_deployed]
gcode:
    {% if not printer.probe.last_query %}
      {action_raise_error("probe already deployed - remove and return to dock")}
    {% endif %}

[gcode_macro error_if_probe_deployed]
gcode:
    G4 P300
    QUERY_PROBE
    do_error_if_probe_deployed

[gcode_macro do_error_if_probe_not_deployed]
gcode:
    {% if printer.probe.last_query %}
      {action_raise_error("probe unsuccessfully deployed")}
    {% endif %}

[gcode_macro error_if_probe_not_deployed]
gcode:
    G4 P300
    QUERY_PROBE
    do_error_if_probe_not_deployed

# Macro to Deploy Bed Probe
[gcode_macro M401]
gcode:
    {action_respond_info("Entering M401")}
    error_if_probe_deployed
    G91                          ; relative positioning
    G1 Z8 F4000                  ; move Z 8 for clearance above dock
    G90                          ; absolute positioning
    G1 X5.0 Y290 F6000           ; move adjacent to probe dock location
    M400                         ; wait for moves to finish
    G1 X5 Y305.3 F3000           ;  move over dock
    G1 X60 Y305.3 F1200          ;  slide probe out of dock - slowly
    M400
    error_if_probe_not_deployed
    {action_respond_info("Exit M401")}

# Macro to Retract (Stow) Bed Leveling Probe
[gcode_macro M402]
gcode:
    {action_respond_info("Entering M402")}
    error_if_probe_not_deployed
    G1 X90 Y280 F6000             ; move to the starting point (6000 for normal speed)
    G1 X90 Y305.3  F3000          ; move to intermediate point (3000 for normal speed)
    M400
    G1 X40 Y305.3  F3000          ; move to just outside dock position - leave at speed 300
    M400
    G1 X5.0 Y305.3  F1200         ; move to dock and drop off probe
    M400
    G1 X5.0 Y280  F3000           ; move to the side adjacent to the dock
    M400
    error_if_probe_deployed
    {action_respond_info("Exit M402")}

[gcode_macro FILAMENT_LOAD]
gcode:
    G91             ; set extruder to relative
    G1 E90 F900		; load filament/extrude 90mm at 15mm/sec
    G1 E120 F120	; extrude 120mm at 2mm/sec
    G90

[gcode_macro FILAMENT_UNLOAD]
gcode:
    G91             ; set extruder to relative
    G1 E-180 F900 	; unload 180mm at 15mm/sec speed
    G90
		
## 	Thermistor Types
#      "EPCOS 100K B57560G104F"
#      "ATC Semitec 104GT-2"
#      "NTC 100K beta 3950"
#      "Honeywell 100K 135-104LAG-J01"
#      "NTC 100K MGB18-104F39050L32" (Keenovo Heater Pad)
#      "AD595"
#      "PT100 INA826"

[force_move]
enable_force_move: True

#*# <---------------------- SAVE_CONFIG ---------------------->
#*# DO NOT EDIT THIS BLOCK OR BELOW. The contents are auto-generated.
#*#
#*# [extruder]
#*# control = pid
#*# pid_kp = 30.113
#*# pid_ki = 1.521
#*# pid_kd = 149.059
#*#
#*# [heater_bed]
#*# control = pid
#*# pid_kp = 48.658
#*# pid_ki = 0.537
#*# pid_kd = 1102.109
#*#
#*# [probe]
#*# z_offset = 2.920
#*#
#*# [skew_correction my_skew_profile]
#*# xy_skew = 0.00106478605119
#*# xz_skew = 0.000779231131148
#*# yz_skew = -0.00254994294792
#*#
#*# [bed_mesh default]
#*# version = 1
#*# points =
#*# 	  -0.004650, 0.005350, -0.004858, -0.012150, 0.024725, 0.070975
#*# 	  -0.099025, -0.094650, -0.075275, -0.056108, -0.036525, 0.040142
#*# 	  -0.168816, -0.166108, -0.139441, -0.117358, -0.069650, -0.002775
#*# 	  -0.243608, -0.251108, -0.207150, -0.176733, -0.106733, -0.017775
#*# 	  -0.125066, -0.244233, -0.232150, -0.199441, -0.146733, -0.066525
#*# 	  -0.150691, -0.262358, -0.290483, -0.259441, -0.189025, -0.086316
#*# tension = 0.2
#*# min_x = 2.0
#*# algo = lagrange
#*# y_count = 6
#*# mesh_y_pps = 2
#*# min_y = 36.0
#*# x_count = 6
#*# max_y = 299.0
#*# mesh_x_pps = 2
#*# max_x = 299.0
