nionio6915/Euclid_Probe/Firmware_Examples/Klipper/user_contrib/Ender5/Ender5_euclid 25-9-2021.cfg

# Movement Locations to work out
# Pre-flight position X100 Y20
# Dock Adjacent  position X30 Y0
# Probe pikcup over dock X0 Y0
# Dock exit Position X0 Y40
# Probe Ready Position X150 Y30

[gcode_macro move_to_dockside]
# Location adjacent to dock Y-30
gcode:
  G90                 ; absolute coordinate system
  G90 X100 Y20 Z15    ; Step 1, Pre-flight
  G0 X40 Y8 Z15       ; Step 2, Dock Adjacent move to X53 Y350


[gcode_macro move_to_dock]
# Dock position at X53 Y350 Z3.7
gcode:
  G90                  ; absolute coordinate system
  G0 X10 Y8 Z15         ; step 3, move to dock at X53 Y350


[gcode_macro move_outof_dock]
# Location adjacent to dock for exit X+40 
gcode:
  G90                 ; absolute coordinate system
  G0 X10 Y40 Z15       ; move to X93 Y350 Z3.7
  G0 X150 Y30 Z15     ;


[gcode_macro move_to_dockside_stow]
# Location adjacent to dock Y-30
gcode:
  G90                 ; absolute coordinate system
  G0 X40 Y8 Z15       ; Step 2, Dock Adjacent move to X53 Y350


[gcode_macro move_to_dock_stow]
# Dock position at X53 Y350 Z3.7
gcode:
  G90                  ; absolute coordinate system
  G0 X150 Y30 Z15      ; step 3, move to dock at X53 Y350


[gcode_macro move_in_dock]
# Location adjacent to dock for exit X+40 
gcode:
  G90                 ; absolute coordinate system
  G0 X10 Y40 Z15       ; move to X93 Y350 Z3.7
  G0 X10 Y8  Z15
  G0 X40 Y8 Z15 
  
# Macro to Deploy Bed Probe
[gcode_macro M401]
gcode:
    G90
    {% if printer.probe.last_query %}
      G0 Z15 F14000        ;  set approach elevation of Z10
      move_to_dockside     ;  
      move_to_dock         ;  translate over probe pickup location
      move_outof_dock      ;  translate to side to exit dock   
      G0 Z15 F14000        ;  raise to elevation of Z20
      error_if_probe_not_deployed
    {% endif %}


# Macro to Stow Bed Leveling Probe
[gcode_macro M402]
gcode:
    G90
    {% if not printer.probe.last_query %}
     G0 Z15 F14000               ;  set approach elevation of Z20
     #move_outof_dock             ;  move toolhead to dock exit position
     #move_to_dock                ;  move probe into to dock 
     #move_to_dockside            ;  swipe probe off 
     move_to_dock_stow
     move_in_dock
     G0 Z15 F14000               ;  move up to elevation of Z20
     error_if_probe_deployed
    {% endif %}

[gcode_macro do_error_if_probe_deployed]
gcode:
    {% if not printer.probe.last_query %}
      {action_raise_error("Euclid Probe is already deployed - Remove and Return it to the dock")}
    {% endif %}

[gcode_macro error_if_probe_deployed]
gcode:
    G4 P300
    QUERY_PROBE
    do_error_if_probe_deployed

[gcode_macro do_error_if_probe_not_deployed]
gcode:
    {% if printer.probe.last_query %}
      {action_raise_error("Euclid Probe Unsuccessfully Deployed!")}
    {% endif %}

[gcode_macro error_if_probe_not_deployed]
gcode:
    G4 P300
    QUERY_PROBE
    do_error_if_probe_not_deployed
